Scaniox/Glassphones/V1 - esp32/electronics/glassphones - main pcb/components/esp32 - tinypico/TinyPICO V2 Schematics/README.rst

TinyPICO V2 Schematics
======================

PDF schematics for TinyPICO V2 for both USB-C and Micro-B boards

Unexpected Maker
===================

http://unexpectedmaker.com

http://youtube.com/c/unexpectedmaker

https://www.patreon.com/unexpectedmaker

http://twitter.com/unexpectedmaker

https://www.facebook.com/unexpectedmaker/

https://www.instagram.com/unexpectedmaker/
