Scaniox/Glassphones/V1 - esp32/mechanical/photogrammetry/photo/MeshroomCache/StructureFromMotion/d71c1582ed01c90abd0e8f21b0806b4d62578cae/bundle_adjustment.csv

Time/BA(s) | RefinedPose | ConstPose | IgnoredPose | RefinedPts | ConstPts | IgnoredPts | RefinedK | ConstK | IgnoredK | ResidualBlocks | SuccessIteration | BadIteration | InitRMSE | FinalRMSE | d=-1 | d=0 | d=1 | d=2 | d=3 | d=4 | d=5 | d=6 | d=7 | d=8 | d=9 | d=10+
0.0121821 | 2 | 0 | 0 | 1470 | 0 | 0 | 0 | 1 | 0 | 2940 | 4 | 0 | 0.357994 | 0.327687 | 0 | 0 | 0 | 0 | 0 | 0 | 0 | 0 | 0 | 0 | 0 | 0
0.137033 | 3 | 0 | 0 | 6186 | 0 | 0 | 1 | 0 | 0 | 12372 | 9 | 0 | 0.859424 | 0.383543 | 0 | 0 | 0 | 0 | 0 | 0 | 0 | 0 | 0 | 0 | 0 | 0
1.13852 | 4 | 0 | 0 | 8314 | 0 | 0 | 1 | 0 | 0 | 16628 | 48 | 3 | 1.23038 | 0.613462 | 0 | 0 | 0 | 0 | 0 | 0 | 0 | 0 | 0 | 0 | 0 | 0
1.58042 | 5 | 0 | 0 | 12751 | 0 | 0 | 1 | 0 | 0 | 25502 | 51 | 0 | 0.928391 | 0.694446 | 0 | 0 | 0 | 0 | 0 | 0 | 0 | 0 | 0 | 0 | 0 | 0
1.9575 | 6 | 0 | 0 | 16011 | 0 | 0 | 1 | 0 | 0 | 32022 | 51 | 0 | 1.33581 | 1.04123 | 0 | 0 | 0 | 0 | 0 | 0 | 0 | 0 | 0 | 0 | 0 | 0
2.25359 | 7 | 0 | 0 | 17949 | 0 | 0 | 1 | 0 | 0 | 35898 | 51 | 0 | 1.16084 | 0.9656 | 0 | 0 | 0 | 0 | 0 | 0 | 0 | 0 | 0 | 0 | 0 | 0
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
