Scaniox/Glassphones/V1 - esp32/mechanical/IMG_20210727_0002.jpg

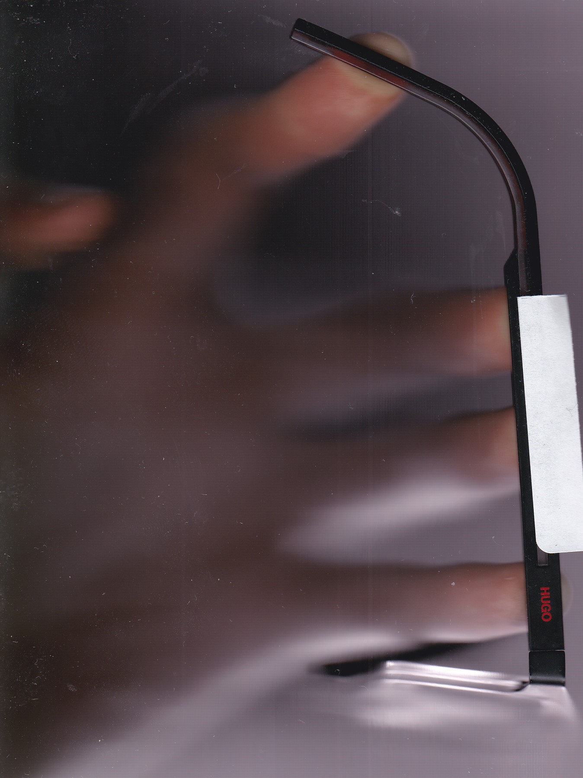
V1 - esp32/mechanical/IMG_20210727_0002.jpg
