Scaniox/Glassphones/V1 - esp32/mechanical/photogrammetry/photo/MeshroomCache/DepthMapFilter/24b79df3ac3274988167803b87b50ed05e469bb3/31802105_nmodMap.png

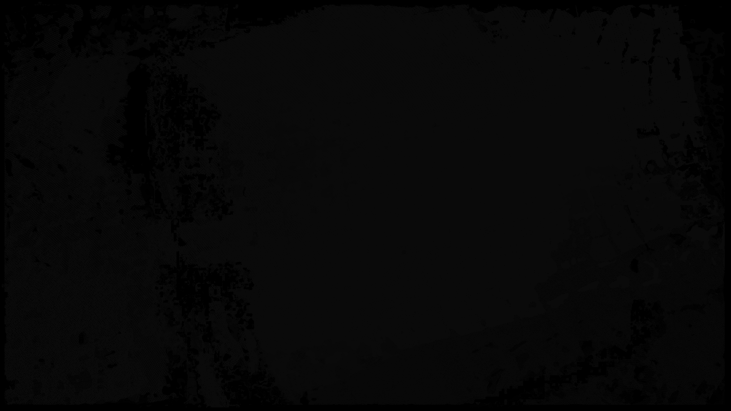
V1 - esp32/mechanical/photogrammetry/photo/MeshroomCache/DepthMapFilter/24b79df3ac3274988167803b87b50ed05e469bb3/31802105_nmodMap.png
