Scaniox/Glassphones/V1 - esp32/mechanical/photogrammetry/photo/MeshroomCache/DepthMapFilter/24b79df3ac3274988167803b87b50ed05e469bb3/286981042_nmodMap.png

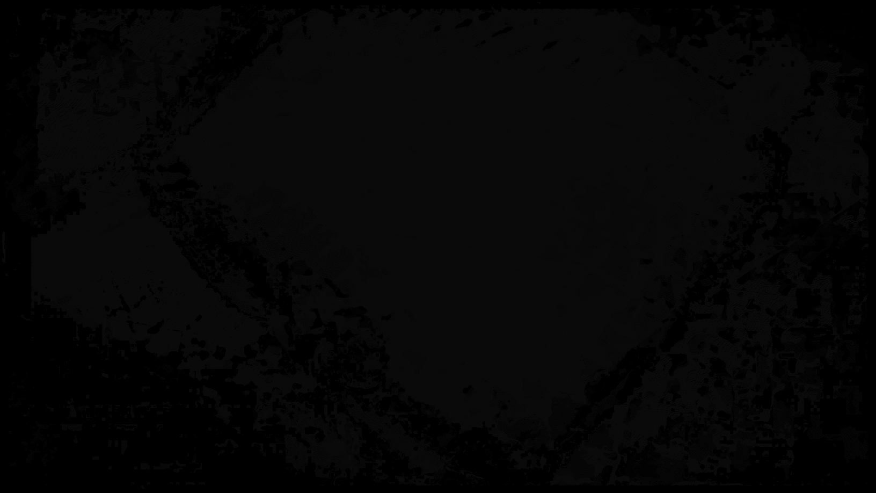
V1 - esp32/mechanical/photogrammetry/photo/MeshroomCache/DepthMapFilter/24b79df3ac3274988167803b87b50ed05e469bb3/286981042_nmodMap.png
