Scaniox/Glassphones/V1 - esp32/mechanical/photogrammetry/video/MeshroomCache/Texturing/2c468ecf00575808510a90f24e992894a4d70658/texture_1001.png

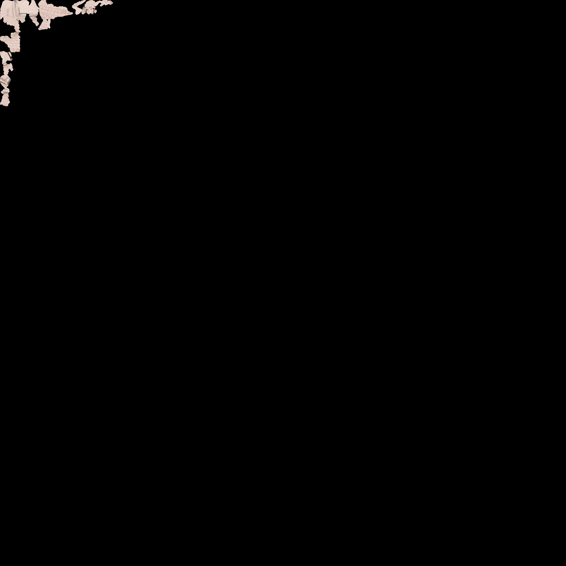
V1 - esp32/mechanical/photogrammetry/video/MeshroomCache/Texturing/2c468ecf00575808510a90f24e992894a4d70658/texture_1001.png
