Scaniox/Glassphones/V1 - esp32/mechanical/photogrammetry/video/r50 imgs/scene00001.png

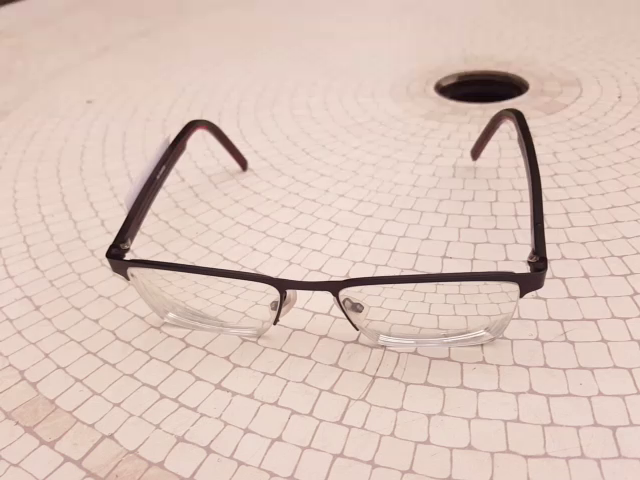
V1 - esp32/mechanical/photogrammetry/video/r50 imgs/scene00001.png
