Scaniox/Glassphones/V1 - esp32/mechanical/photogrammetry/video/r50 imgs/scene00701.png

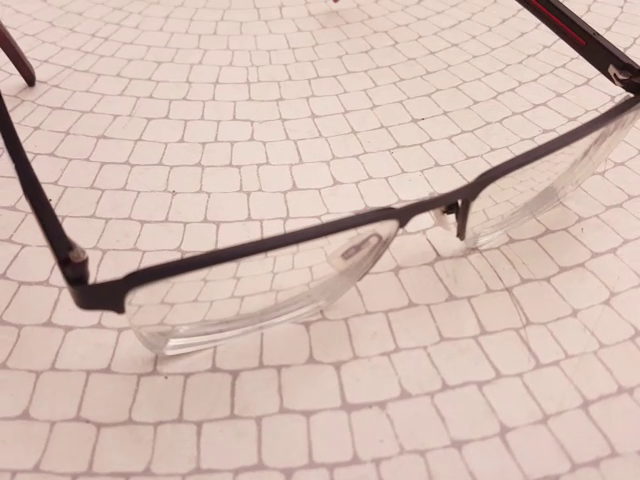
V1 - esp32/mechanical/photogrammetry/video/r50 imgs/scene00701.png
