Scaniox/Glassphones/V1 - esp32/mechanical/photogrammetry/video/r50 imgs/scene00851.png

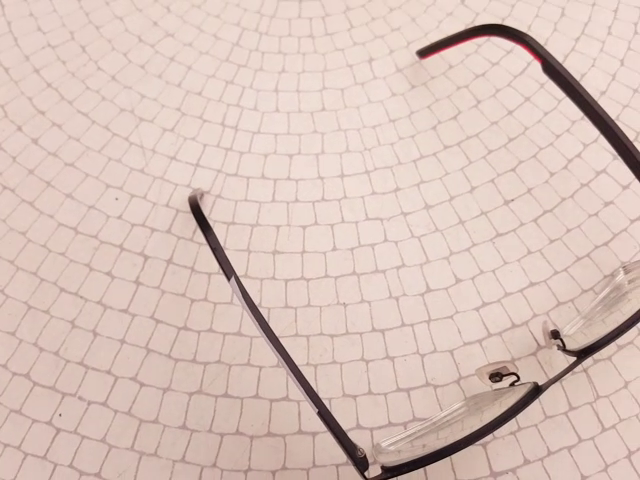
V1 - esp32/mechanical/photogrammetry/video/r50 imgs/scene00851.png
