Scaniox/Glassphones/V1 - esp32/mechanical/photogrammetry/video/r50 imgs/scene00901.png

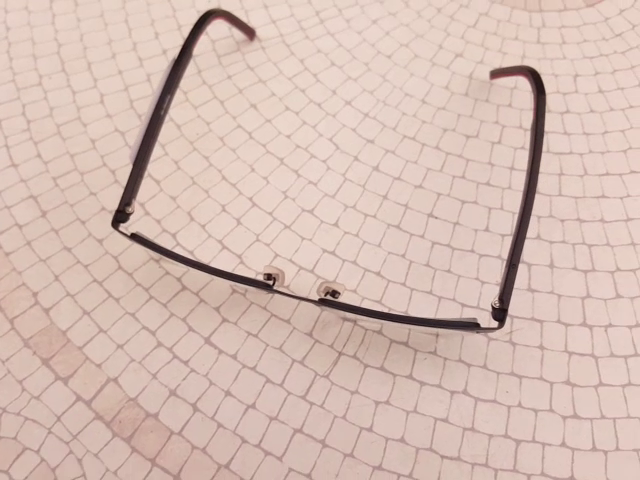
V1 - esp32/mechanical/photogrammetry/video/r50 imgs/scene00901.png
