Scaniox/Glassphones/V1 - esp32/mechanical/photogrammetry/video/r50 imgs/scene01051.png

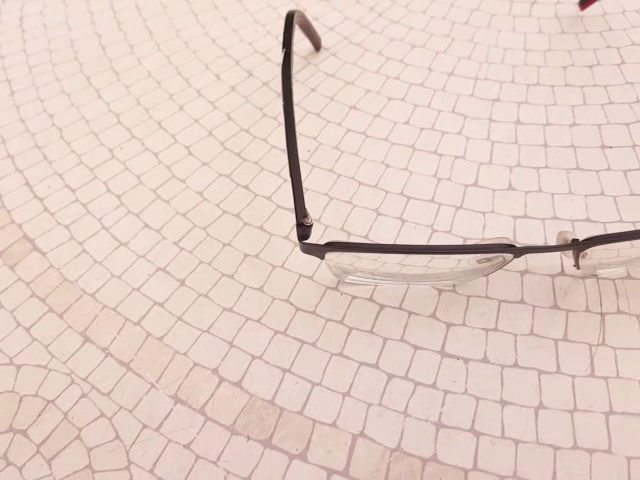
V1 - esp32/mechanical/photogrammetry/video/r50 imgs/scene01051.png
