Scaniox/Glassphones/V1 - esp32/mechanical/photogrammetry/video/r50 imgs/scene01151.png

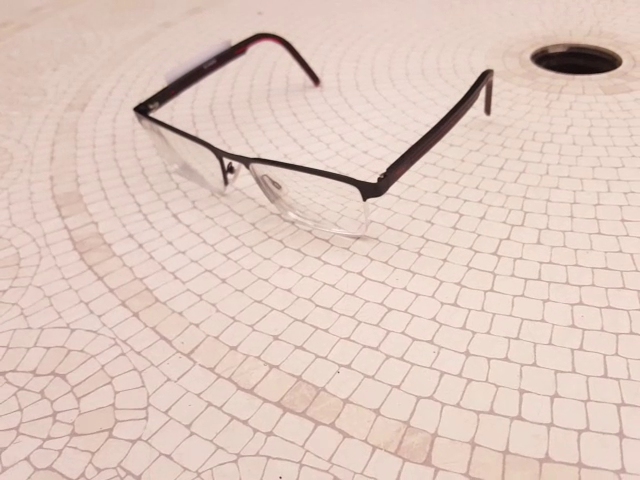
V1 - esp32/mechanical/photogrammetry/video/r50 imgs/scene01151.png
