Scaniox/Glassphones/V1 - esp32/mechanical/photogrammetry/video/r50 imgs/scene01651.png

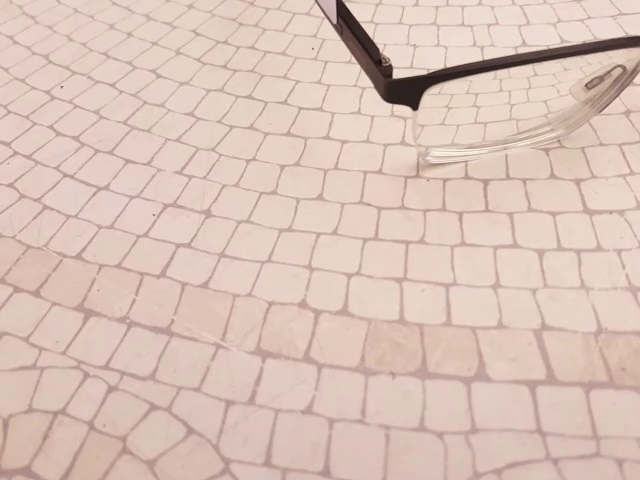
V1 - esp32/mechanical/photogrammetry/video/r50 imgs/scene01651.png
