Scaniox/Glassphones/V2/mechanical/power-led-1.snapshot.1/Power Led.jpg

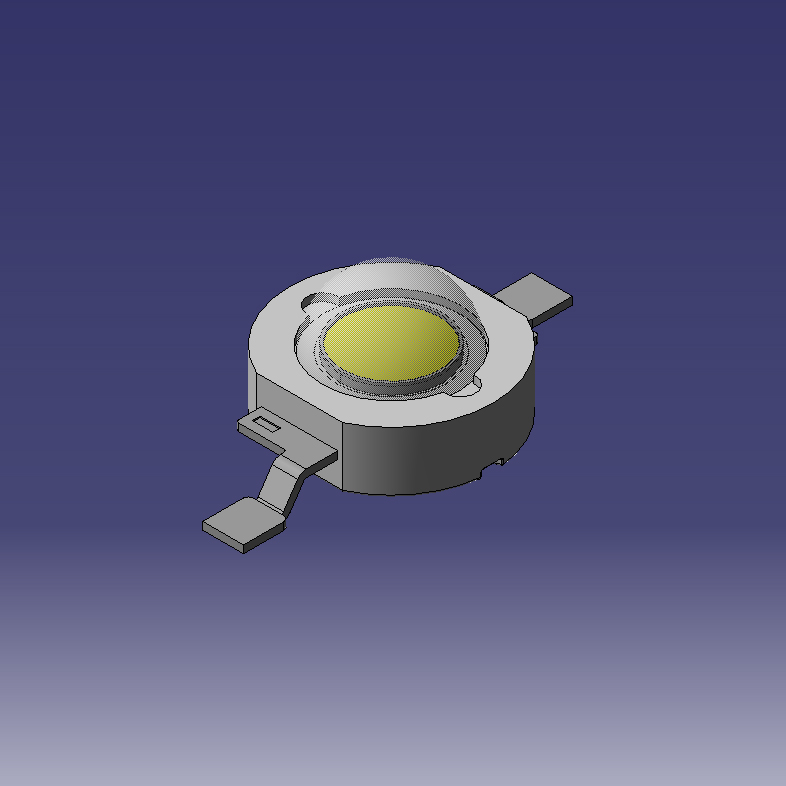
V2/mechanical/power-led-1.snapshot.1/Power Led.jpg
