Scaniox/Glassphones/V2/code/IS2083 Software & Tools (v1.0.3)/Tools/OTA DSP Tuning/IS187x_202_BLEDK3v2.00_UI v2.13/BLEDK_UI_Parameter_Table.xls

FW : | BLEDK3 v2 |  | Date: 2017/06/20
UI Table Version: | 0100
Parameter | Offset | Length | Name | Display | Range | Help | ID
NameFragment | 800 | 32 | Name Fragment | Edit Box | 32 characters | NameFragment is a local device name. If a remote device requires a local name, a local device replies the local device name. | IDC_STATIC_NAME_FRAGMENT
hci_baud_rate_index | 820 | 1 | HCI Baud Rate Index | ComboBox | 0x00 : 921600 0x01 : 460800 0x02 : 230400 0x03 : 115200 0x04 : 57600 0x05 : 38400 0x06 : 28800 0x07 : 19200 0x08 : 14400 0x09 : 9600 0x0A : 4800 0x0B : 2400 | Baud rate index of the HCI UART port. | IDC_STATIC_HCI_BAUD_RATE_INDEX
system_option_3 | 824 | bit0 | H/W Flow Control | ComboBox | Disable Enable | UART H/W flow control (CTS). This parameter need to be set as disable if MCU not support flow control. If Operation Pattern select Manual Pattern, the flow control will be set as disable automatically. | IDC_STATIC_CTS_RTS_FLOW_CONTROL
rxNotifyLength | 828 | 1 | Rx Notify Length | Edit Box | 0x00 ~ 0xFF | The time interval that BLEDK3 checks the received data buffer. When set as “00”, the default value in BLEDK3 for each baud rate is as below: 921600 ~ 19200:0x01 14400 ~ 9600:0x02 4800:0x04 Others:0x07 (Unit: 0.625ms) This parameter can be modified when the default setting can’t meet the requirement. The new set up value must greater than the default value. | IDC_STATIC_CHECK_RX_DATA_INTERVAL
system_option_1 | 822 | bit1 | UART RX_IND | ComboBox | Enable Disable | Enable / Disable UART RX IND | IDC_STATIC_UART_RX_IND
system_option_2 | 823 | bit2 | Operation Pattern | ComboBox | Auto Pattern Manual Pattern | This parameter is used to set the operation pattern between Auto Pattern and Manual Pattern. | IDC_STATIC_OPERATION_PATTERN
Configure_TO | 829 | 1 | Configure Mode Timeout | Edit Box | 0x00: Disable Configure Mode, 0x01~0xFF | This parameter is used to set BLEDK3 configure mode timeout period in Auto Pattern Tool option. | IDC_STATIC_CONFIGURE_MODE_TIMEOUT
PowerOn_Standby_Time | 825 | 1 | Power On Standby Time | Edit Box | 0x01 ~ 0xFF | The standby time duration after power on. Device will enter Shut Down mode when time is up. 0x00~0xFE: Standby time parameter range. 0xFF: Disable Enter shut down mode. | IDC_STATIC_POWER_ON_STANDBY_TIME
Remote_Disconnent_Standby_Time | 826 | 1 | Disconnection Standby Time | Edit Box | 0x01 ~ 0xFF | The standby time duration after link disconnected. Device will enter shut down mode when time is up. 0x00~0xFE: Standby time parameters. 0xFF: Disable enter shut down mode. | IDC_STATIC_REMOTE_DISCONNECT_STANDBY_TIME
Wakeup_External_MCU_Wait_Time | 827 | 1 | Wakeup Externel MCU Wait Time | Edit Box | 0x00 ~ 0xFF | The time interval between UART_TX_IND enabled and UART_TXD start transmit data. | IDC_STATIC_WAKEUP_EXTERNAL_MCU_WAIT_TIME
system_option_3 | 824 | bit2 | Wakeup Pin Option | ComboBox | Enable waken up from shutdown mode by wakeup pin Disable waken up from shutdown mode by wakeup pin | This parameter is used to decide BLEDK3 can be woken up from shutdown mode by wakeup pin or not. If option is enabled, GPIO P2_3 will be configured as wakeup Pin. | IDC_STATIC_WAKEUP_PIN_OPTION
system_option_1 | 822 | bit3~4 | BLE Security | ComboBox | Disable Pairing Request Permission Enable | This parameter is used to set BLE Security. Refer to BLUETOOTH SPECIFICATION 4.0 or latest version for the detail. | IDC_STATIC_BLE_SECURITY
IO_Capability | 87D | 1 | IO Capability | ComboBox | 0x00: DisplayOnly 0x01: DisplayYesNo 0x02: KeyboardOnly 0x03: NoInputNoOutput 0x04: KeyboardDisplay | This parameter is used to configure IO Capability. Refer to BLUETOOTH SPECIFICATION 4.0 or latest version for the detail. | IDC_STATIC_IO_CAPABILITY
system_option_2 | 823 | bit0 | BLE User Confirm Option | ComboBox | Disable LE user confirm refer to passkey Enable LE user confirm refer to passkey | This parameter is used to enable/disable LE(Low Energy) user confirmation referring to passkey. The passkey must set 6 digits if enabled. | IDC_STATIC_BLE_USER_CONFIRM_OPTION
Fix_Passkey | 8 | 6 | Passkey | Edit Box | 6 Numbers | The Passkey which is six byte ASCII code and be used in passkey confirm. | IDC_STATIC_PASSKEY
system_option_2 | 823 | bit6 | Trust Device Connection | ComboBox | Disable Enable | This parameter is used to enable/disable trust (paired) device connection. | IDC_STATIC_TRUST_DEVICE_CONNECTION
system_option_1 | 822 | bit2 | LE Secure Connections Only Mode | ComboBox | Disable Enable | This parameter is used to enable/disable bluetooth 4.2 LE secure connections only mode. | IDC_STATIC_LE_SECURE_CONNECTIONS
system_option_1 | 822 | bit5 | Link Manager Version | ComboBox | Link Manager version is BT4.0 Link Manager version is BT4.2 | This parameter is used to choose Link Manager Version between BT4.0 and BT4.2 . | IDC_STATIC_LINK_MANAGER_VERSION
system_option_1 | 822 | bit6 | Data Length Extension | ComboBox | Disable Enable | This parameter is used to enable/disable Data Length Extension. | IDC_STATIC_DATA_LENGTH_EXTENSION
system_option_1 | 822 | bit0 | Link Quality Detection | ComboBox | Disable Enable | Enable/Disable link quality detection. The RF_Tx_Power_Control_feature will be disabled if Enable this parameter. | IDC_STATIC_LINK_QUALITY_DETECTION
rssi_normal_threshold | 82A | 1 | RSSI Normal Threshold | Edit Box | 50 ~ 90 | RSSI: RF Signal Strength Indication. This parameter is used to set RSSI normal threshold value If detected RSSI value greater or lower than normal threshold level, the configured RSSI_IND GPIO pin will output high or low level respectively. | IDC_STATIC_RSSI_NORMAL_THRESHOLD
rssi_weak_threshold | 82B | 1 | RSSI Weak Threshold | Edit Box | 50 ~ 90 | If detected RSSI value greater or lower than weak threshold level, the configured RSSI_IND GPIO pin will output high or low level respectively. | IDC_STATIC_RSSI_WEAK_THRESHOLD
battery_det_interval | 83A | 1 | Battery Detection Interval | Edit Box | (1~255) | This parameter is used to set battery detection interval. | IDC_STATIC_BATTERY_DETECTION
High_Battery_Level | 83C | 1 | High Battery Level | ComboBox | 0x48 0x4C … 0x90 | High battery level. | IDC_STATIC_HIGH_BATTERY_LEVEL
Normal_Battery_Level | 83D | 1 | Normal Battery Level | ComboBox | 0x48 0x4C … 0x90 | This parameter is defined a normal voltage value of a battery. When the voltage is lower than this value,the device will start low battery warring. | IDC_STATIC_NORMAL_BATTERY_LEVEL
Low_Battery_Level | 83E | 1 | Low Battery Level | ComboBox | 0x48 0x4C … 0x90 | This parameter is defined a low voltage value of a battery. When the voltage is lower than this value, the configured “LOW_BATTERY_IND” GPIO will output low and the device will enter shutdown mode after the “Low Battery Into Shutdown Time”. | IDC_STATIC_LOW_BATTERY_LEVEL
Dangerous_Battery_Level | 83F | 1 | Dangerous Battery Level | ComboBox | 0x48 0x4C … 0x90 | When the voltage is lower than Dangerous Battery Level, the device will enter shutdown mode. | IDC_STATIC_DANGEROUS_BATTERY_LEVEL
Low_Battery_Into_Shutdown_Time | 839 | 1 | Low Battery Into Shutdown Time | Edit Box | 0x00:Disable，0x01~0xFF(Unit:640ms) | This parameter is used to set the waiting time befor enter into shutdown mode if low battery happens. (0x00: Disable enter into shutdown mode when low battery happens) | IDC_STATIC_LOW_BATTERY_INTO_POWER_DOWN_TIME
RF_Class | 821 | 1 | RF Class | ComboBox | 0x01: class 1 0x02: class 2 | The RF_Class is the RF class type. If class 1 is selected, GPIO P1_0 and P2_4 will be set as TX and RX control respectively (High Enable). | IDC_STATIC_RF_CLASS
GPIO_Configured_P36 | 868 | 1 | P36 | Button | 0x01: UART_RTS_CONFIGURE 0x02: BATTERY_LOW_CONFIGURE 0x03: LINK_QUALITY_CONFIGURE 0x05: LINK_DROP_CONFIGURE 0x06: UART_RX_IND_CONFIGURE 0x07: PAIRING_CONFIGURE 0x08: RF_ACTIVE_IND_CONFIGURE 0x09: STATUS1_IND 0x0A: STATUS2_IND 0x0B: AUTO_MODE_DATA_TX_CTRL | Configure function to the GPIO pins. For detail description please refer to the BLEDK3 release note in “IS187x_BM7X BLEDK3 Application Note” document. | IDC_STATIC_P36
GPIO_Configured_P10 | 869 | 1 | P10 | Button | 0x02: BATTERY_LOW_CONFIGURE 0x03: LINK_QUALITY_CONFIGURE 0x05: LINK_DROP_CONFIGURE 0x06: UART_RX_IND_CONFIGURE 0x07: PAIRING_CONFIGURE 0x08: RF_ACTIVE_IND_CONFIGURE 0x09: STATUS1_IND 0x0A: STATUS2_IND 0x0B: AUTO_MODE_DATA_TX_CTRL |  | IDC_STATIC_P10
GPIO_Configured_P00 | 86A | 1 | P00 | Button | 0x02: BATTERY_LOW_CONFIGURE 0x03: LINK_QUALITY_CONFIGURE 0x04: UART_CTS_CONFIGURE 0x05: LINK_DROP_CONFIGURE 0x06: UART_RX_IND_CONFIGURE 0x07: PAIRING_CONFIGURE 0x08: RF_ACTIVE_IND_CONFIGURE 0x09: STATUS1_IND 0x0A: STATUS2_IND 0x0B: AUTO_MODE_DATA_TX_CTRL |  | IDC_STATIC_P00
GPIO_Configured_P31 | 86B | 1 | P31 | Button | 0x02: BATTERY_LOW_CONFIGURE 0x03: LINK_QUALITY_CONFIGURE 0x05: LINK_DROP_CONFIGURE 0x06: UART_RX_IND_CONFIGURE 0x07: PAIRING_CONFIGURE 0x08: RF_ACTIVE_IND_CONFIGURE 0x09: STATUS1_IND 0x0A: STATUS2_IND 0x0B: AUTO_MODE_DATA_TX_CTRL |  | IDC_STATIC_P31
GPIO_Configured_P32 | 86C | 1 | P32 | Button | 0x02: BATTERY_LOW_CONFIGURE 0x03: LINK_QUALITY_CONFIGURE 0x05: LINK_DROP_CONFIGURE 0x06: UART_RX_IND_CONFIGURE 0x07: PAIRING_CONFIGURE 0x08: RF_ACTIVE_IND_CONFIGURE 0x09: STATUS1_IND 0x0A: STATUS2_IND 0x0B: AUTO_MODE_DATA_TX_CTRL |  | IDC_STATIC_P32
GPIO_Configured_P33 | 86D | 1 | P33 | Button | 0x02: BATTERY_LOW_CONFIGURE 0x03: LINK_QUALITY_CONFIGURE 0x05: LINK_DROP_CONFIGURE 0x06: UART_RX_IND_CONFIGURE 0x07: PAIRING_CONFIGURE 0x08: RF_ACTIVE_IND_CONFIGURE 0x09: STATUS1_IND 0x0A: STATUS2_IND 0x0B: AUTO_MODE_DATA_TX_CTRL |  | IDC_STATIC_P33
GPIO_Configured_P34 | 86E | 1 | P34 | Button | 0x02: BATTERY_LOW_CONFIGURE 0x03: LINK_QUALITY_CONFIGURE 0x05: LINK_DROP_CONFIGURE 0x06: UART_RX_IND_CONFIGURE 0x07: PAIRING_CONFIGURE 0x08: RF_ACTIVE_IND_CONFIGURE 0x09: STATUS1_IND 0x0A: STATUS2_IND 0x0B: AUTO_MODE_DATA_TX_CTRL |  | IDC_STATIC_P34
GPIO_Configured_P07 | 86F | 1 | P07 | Button | 0x02: BATTERY_LOW_CONFIGURE 0x03: LINK_QUALITY_CONFIGURE 0x05: LINK_DROP_CONFIGURE 0x06: UART_RX_IND_CONFIGURE 0x07: PAIRING_CONFIGURE 0x08: RF_ACTIVE_IND_CONFIGURE 0x09: STATUS1_IND 0x0A: STATUS2_IND 0x0B: AUTO_MODE_DATA_TX_CTRL |  | IDC_STATIC_P07
GPIO_Configured_P11 | 870 | 1 | P11 | Button | 0x02: BATTERY_LOW_CONFIGURE 0x03: LINK_QUALITY_CONFIGURE 0x05: LINK_DROP_CONFIGURE 0x06: UART_RX_IND_CONFIGURE 0x07: PAIRING_CONFIGURE 0x08: RF_ACTIVE_IND_CONFIGURE 0x09: STATUS1_IND 0x0A: STATUS2_IND 0x0B: AUTO_MODE_DATA_TX_CTRL |  | IDC_STATIC_P11
GPIO_Configured_P22 | 871 | 1 | P22 | Button | 0x02: BATTERY_LOW_CONFIGURE 0x03: LINK_QUALITY_CONFIGURE 0x05: LINK_DROP_CONFIGURE 0x06: UART_RX_IND_CONFIGURE 0x07: PAIRING_CONFIGURE 0x08: RF_ACTIVE_IND_CONFIGURE 0x09: STATUS1_IND 0x0A: STATUS2_IND 0x0B: AUTO_MODE_DATA_TX_CTRL |  | IDC_STATIC_P22
GPIO_Configured_P24 | 872 | 1 | P24 | Button | 0x02: BATTERY_LOW_CONFIGURE 0x03: LINK_QUALITY_CONFIGURE 0x05: LINK_DROP_CONFIGURE 0x06: UART_RX_IND_CONFIGURE 0x07: PAIRING_CONFIGURE 0x08: RF_ACTIVE_IND_CONFIGURE 0x09: STATUS1_IND 0x0A: STATUS2_IND 0x0B: AUTO_MODE_DATA_TX_CTRL |  | IDC_STATIC_P24
GPIO_Configured_P35 | 873 | 1 | P35 | Button | 0x02: BATTERY_LOW_CONFIGURE 0x03: LINK_QUALITY_CONFIGURE 0x05: LINK_DROP_CONFIGURE 0x06: UART_RX_IND_CONFIGURE 0x07: PAIRING_CONFIGURE 0x08: RF_ACTIVE_IND_CONFIGURE 0x09: STATUS1_IND 0x0A: STATUS2_IND 0x0B: AUTO_MODE_DATA_TX_CTRL |  | IDC_STATIC_P35
GPIO_Configured_P12 | 864 | 1 | P12 | Button | 0x02: BATTERY_LOW_CONFIGURE 0x03: LINK_QUALITY_CONFIGURE 0x05: LINK_DROP_CONFIGURE 0x06: UART_RX_IND_CONFIGURE 0x07: PAIRING_CONFIGURE 0x08: RF_ACTIVE_IND_CONFIGURE 0x09: STATUS1_IND 0x0A: STATUS2_IND 0x0B: AUTO_MODE_DATA_TX_CTRL |  | IDC_STATIC_P12
GPIO_Configured_P13 | 865 | 1 | P13 | Button | 0x02: BATTERY_LOW_CONFIGURE 0x03: LINK_QUALITY_CONFIGURE 0x05: LINK_DROP_CONFIGURE 0x06: UART_RX_IND_CONFIGURE 0x07: PAIRING_CONFIGURE 0x08: RF_ACTIVE_IND_CONFIGURE 0x09: STATUS1_IND 0x0A: STATUS2_IND 0x0B: AUTO_MODE_DATA_TX_CTRL |  | IDC_STATIC_P13
GPIO_Configured_P16 | 866 | 1 | P16 | Button | 0x02: BATTERY_LOW_CONFIGURE 0x03: LINK_QUALITY_CONFIGURE 0x05: LINK_DROP_CONFIGURE 0x06: UART_RX_IND_CONFIGURE 0x07: PAIRING_CONFIGURE 0x08: RF_ACTIVE_IND_CONFIGURE 0x09: STATUS1_IND 0x0A: STATUS2_IND 0x0B: AUTO_MODE_DATA_TX_CTRL |  | IDC_STATIC_P16
GPIO_Configured_P17 | 867 | 1 | P17 | Button | 0x02: BATTERY_LOW_CONFIGURE 0x03: LINK_QUALITY_CONFIGURE 0x05: LINK_DROP_CONFIGURE 0x06: UART_RX_IND_CONFIGURE 0x07: PAIRING_CONFIGURE 0x08: RF_ACTIVE_IND_CONFIGURE 0x09: STATUS1_IND 0x0A: STATUS2_IND 0x0B: AUTO_MODE_DATA_TX_CTRL |  | IDC_STATIC_P17
 |  |  | LE Connection Parameter Update Request | ComboBox | Disable Enable | The LE Connection Setting will be assigned by remote side if select disable. If Enable, device will sent the LE connection parameter update request. | IDC_STATIC_LE_CONNECTION_PARAMETER_UPDATE
LE_Connection_Interval_Min | 82C | 2 | Min LE Connection Interval | Edit Box | 0x0006 ~ 0x0C80, Unit: 1.25ms | This parameter is used to set LE min connection interval | IDC_STATIC_MIN_LE_CONNECTION_INTERVAL
LE_Connection_Interval_Max | 82E | 2 | Max LE Connection Interval | Edit Box | 0x0006 ~ 0x0C80, Unit: 1.25ms | This parameter is used to set LE max connection interval | IDC_STATIC_MAX_LE_CONNECTION_INTERVAL
LE_Slave_Latency | 830 | 2 | LE Slave Latency | Edit Box | 0x0000 ~ 0x01F3 | This parameter is used to set LE slave latency. Slave Latency allows a slave to use a reduced number of connection events. The LE Slave Latency parameter defines the number of consecutive connection events that the slave device is not required to listen for the master. More latency, more power saving but reduced connection event. For example, If slave latency=3, Connection event interval is 100msec, Slave device will wake up every 400msec. (100*(1+3)=400). That is slave only has one Connection event while master already have three connection events. | IDC_STATIC_LE_SLAVE_LATENCY
LE_Supervision_Timeout | 832 | 2 | LE Supervision Timeout | Edit Box | 0x000A ~ 0x0C80 | This parameter is used to set LE supervision timeout | IDC_STATIC_LE_SUPERVISION_TIMEOUT
LE_Fast_Adv_Interval | 834 | 2 | LE Fast Advertising Interval | Edit Box | 0x0020 ~ 0x4000 | This parameter is used to set “LE fast advertising interval”, which will make LE device work in fast advertising interval after power on. The fast advertising time period is limited and can be set in“LE Fast Advertising Timeout”. | IDC_STATIC_LE_FAST_ADVERTISING_INTERVAL
LE_Reduced_Power_Adv_Interval | 836 | 2 | LE Reduced Power Advertising Interval | ComboBox | 645ms 768ms 961ms 1065ms 1294ms | This parameter is used to set LE reduced power advertising interval. The interval is longer than “Fast Advertising Interval” so that the power consumption can be reduced. | IDC_STATIC_LE_REDUCED_POWER_ADVERTISING
LE_Fast_Adv_Timeout | 838 | 1 | LE Fast Advertising Timeout | Edit Box | 0x00 ~ 0xFF 設為0x00就不會離開Fast Advertising Mode | This parameter is uesd to set LE fast advertising timeout value | IDC_STATIC_LE_FAST_ADVERTISING_TIMEOUT
 |  |  | Power On LE Reduced Power Advertising Timeout | Edit Box |  | This parameter is uesd to show Power On LE Reduced Power Advertising timeout value. Power On LE Reduced Power Advertising timeout = Power on Standby Time - LE Fast Advertising Timeout. | IDC_STATIC_POWER_ON_LE_REDUCED_POWER_ADVERTISING_TIMEOUT
 |  |  | Disconnection LE Reduced Power Advertising Timeout | Edit Box |  | This parameter is uesd to show Disconnection LE Reduced Power Advertising Timeout value. Disconnection LE Reduced Power Advertising Timeout = Disconnection Standby Time - LE Fast Advertising Timeout | IDC_STATIC_DISCONNECTION_LE_REDUCED_POWER_ADVERTISING_TIMEOUT
ADV_Prefered_Power_Level | 87E | 1 | Advertising Prefered Power Level | ComboBox | 0x00: 0 dBm 0x01: -6 dBm 0x02: -12 dBm 0x03: -18 dBm 0x04: -24 dBm 0x05: -30 dBm | Preferred Tx power level when advertising. There are six power level can be selected.(0,-5,-10,-15,-20,-25 dBm) | IDC_STATIC_ADVERTISING_TX_POWER_LEVEL
CONN_Prefered_Power_Level | 87F | 1 | Connected Prefered Power Level | ComboBox | 0x00: 0 dBm 0x01: -6 dBm 0x02: -12 dBm 0x03: -18 dBm 0x04: -24 dBm 0x05: -30 dBm | Preferred TX power level when connected. (0,-5,-10,-15,-20,-25 dBm) | IDC_STATIC_CONNECTED_TX_POWER_LEVEL
Advertising_Data | 881 | 31 | Advertising Data Setting |  |  | This parameter is uesd to set advertising data. | IDC_STATIC_ADVERTISING_DATA_SETTING
Scan_Rsp_Data | 8A1 | 31 | Scan Response Data Setting |  |  | This parameter is uesd to set scan response data | IDC_STATIC_SCAN_RESPONSE_DATA_SETTING
LED_Type | 840 | 8 | Type | ComboBox | 0x00 : LED1 OFF, LED2 OFF 0x01 : LED1 ON, LED2 ON 0x02 : LED1 ON, LED2 OFF 0x03 : LED1 OFF, LED2 ON 0x04 : LED1 OFF, LED2 FLASH 0x05 : LED1 FLASH, LED2 OFF 0x06 : LED1 ON, LED2 FLASH 0x07 : LED1 FLASH, LED2 ON 0x08 : LED1, LED2 FLASH (simultaneous) 0x09 : LED1, LED2 FLASH (alternate) | The LED0(P0_2)display type setting for Standby, Link, Power On and Low Battery mode. There are 3 types are selectable: Always OFF, Always ON and Flash. The Flash method is set as below: | IDC_STATIC_LED_TYPE
LED_Flash_On_Time | 848 | 8 | On Duration | Edit Box | (1-255) Unit: 50ms | The LED on time during flash. | IDC_STATIC_LED_ON_TIME
LED_Flash_Off_Time | 850 | 8 | Off Duration | Edit Box | (1-255) Unit: 50ms | The LED off time during flash. | IDC_STATIC_LED_OFF_TIME
LED_Flash_Count | 858 | 8 | Count | Edit Box | (0-3) or (0-255) | This is the number of the flashing times for a cycle. | IDC_STATIC_LED_COUNT
LED_Flash_Interval | 860 | 4 | Interval | Edit Box | (0-255) Unit: 50ms | This is the time interval of a cycle. | IDC_STATIC_LED_INTERVAL
low_battery_LED_warning_time | 83B | 1 | Interval | Edit Box | 0x00:Disable，0x01~0xFF(Unit:1sec) | This parameter is uesd to set LED warning time interval if low battery happens | IDC_STATIC_LOW_BATTERY_LED_INTERVAL
system_option_2 | 823 | bit4 | Beacon Feature | ComboBox | Disable Enable | Enable/Disable Beacon function | IDC_STATIC_BEACON_FEATURE
system_option_2 | 823 | bit5 | Beacon Admin Mode | ComboBox | Disable Enable | Enable/Disable Beacon administration mode. | IDC_STATIC_BEACON_ADMIN_MODE
Beacon_Admin_TO | 874 | 1 | Beacon Admin Timeout | Edit Box | (0-255) Unit: 640ms | This parameter is used to configure Beacon administration timeout value 0x00: Disable Beacon Administration Feature Range: 0x01~0xFF, Unit: 640mS | IDC_STATIC_BEACON_ADMIN_TIMEOUT
system_option_2 | 823 | bit7 | Beacon In Connection | ComboBox | Stop Beacon Advertising Beacon Advertising | This option is enabled when BeaconThings function enabled on UI Feature page. If BeaconThings function is enabled: Stop Beacon Advertising: Stop beacon advertising when LE connection is established. Beacon Advertising: Continue beacon advertising when LE connection is established. | IDC_STATIC_BEACON_IN_CONNECTION
Beacon_ADV_Interval | 875 | 2 | Beacon Advertising Interval | Edit Box | (2 Bytes) | This parameter is used to configure the advertising interval for Beacon. | IDC_STATIC_BEACON_ADVERTISING_INTERVAL
Beacon_Adv_Data_Len | 8C0 | 1 | Beacon Advertising Data Length | Edit Box | (1 Bytes) | This paraeter is used to configure advertising data length for Beacon using | IDC_STATIC_BEACON_ADVERTISING_DATA_LENGTH
Beacon_Adv_Data | 8C1 | 31 | Beacon Advertising Data | Edit Box | Max: 31 bytes | This paraeter is used to configure advertising data for Beacon using | IDC_STATIC_BEACON_ADVERTISING_DATA
Beacon_Secret_Key | 877 | 6 | Beacon Secret Key | Edit Box | (6 Bytes) | This parameter is used to configure Secret key for Beacon Admin usage | IDC_STATIC_BEACON_SECRET_KEY
Specific_Pattern |  | 4 | Specific Pattern | Edit Box | (4 Bytes) | This parameter is used to configure specific pattern for auto connection feature. | IDC_STATIC_MANUFACTURE_DATA
Auto_Connection_TO | 8EB | 1 | Inquiry Timeout Value | Edit Box | 0x00:Disable，0x01~0xFF(Unit: 640 ms) |  | IDC_STATIC_INQUIRY_TIMEOUT_VALUE
system_option_2 | 823 | bit3 | Privacy | ComboBox | Disable Enable | If enabled the option, BLEDK3 will broadcast random address. | IDC_STATIC_PRIVACY
Private_Address_Diversification_Time | 8EC | 1 | Random Address Interval | Edit Box | 0x01~0xFF(Unit: 10.24 s) | This parameter is used to configure random address interval. Valid only when "Privacy" is enabled. | IDC_STATIC_PRIVATE_ADDRESS_DIVERSIFICATION_TIME
Manual_Handle_Value_Confirmation | 822 | bit5 | Manual Handle Value Confirmation | ComboBox | Disable Enable | This parameter is used to enable/disable Manual Handle Value Conrifmation.If this parameter is enable, ATT stack will be configured as manual transmission of confirmation when an indication is received. | IDC_STATIC_ATT_SETTING1
UART_Parity | 8ED | bit0 | UART Parity | ComboBox | Disable Enable | Enable/Disable UART parity. | IDC_STATIC_UART_PARITY
 |  | bit1~2 | Parity Mode | ComboBox | 0x00: Odd Parity 0x01: Space Parity 0x02: Even Parity 0x03: Mark Parity |  | IDC_STATIC_UART_PARITY_MODE
 |  | bit3 | Stop Bit | ComboBox | 1 stop bit 2 stop bit |  | IDC_STATIC_STOP_BIT
