Scaniox/Glassphones/V2/code/IS2083 Software & Tools (v1.0.3)/Tools/Config Tool/IS208x_Config_Parameter_Table_R0.xls

eeprom table file | BT5506_Multi-SPK_V1_eeprom_table_R8 |  |  |  |  | Release Date: 2018/10/17
default eeprom table file | UITool_IS206XGM_002_nSPK05_Default_Table.txt |  |  |  |  | Author: Kiki Ko(A23171)
Parameter File | IS206XGM_002_nSPK_UI_Parameter_Table_R0.xls |  |  |  |  | Contents Updated Conversation | Marked with Red
Tester |  |  |  |  |  | Report Date:
Parameter |  | Length Default:Byte | Default Value(Hex) | Name | Display | Range | Relation | Description | Help | ID
SYS_CFG_KEY_CLASS | 0x0101 | 3 | 0x140424 | Class of Device | Dropdown menu | Address 0x07: 0x04: Headset 0x14: Speaker |  |  | The Class is the class of device/service field (CoD). It is indicated using the 'Format Type field' within the CoD. The value could be 0x040424(HS) or 0x001F00(Uncategorized) | IDC_STATIC_MISC_OPTION11
SYS_CFG_KEY_HCI_BAUD_RATE_INDEX | 0x0102 | 1 | 0x03 | UART Baudrate | Dropdown menu | 0x00: 921600 0x01: 460800 0x02: 230400 0x03: 115200 0x04: 57600 0x05: 38400 0x06: 28800 0x07: 19200 0x08: 14400 0x09: 9600 0x0A: 4800 0x0B: 2400 |  | Valid only when 'HCI Uart' is enabled. | The UART Baudrate is the baud rate index of the HCI UART. (Unit: BPS) | IDC_STATIC_UART_SETTING2
SYS_CFG_KEY_AUTO_POWER_OFF_TIME | 0x0103 | 1 | 0x0F | Auto Power Off Time | Text box | 1~254 |  | Valid only when 'Auto Power Off Enable' is enabled | Set the Auto Power Off timer.The minimum is 1 | IDC_STATIC_POWER_SAVE1
SYS_CFG_KEY_MUTE_ALARM_TIME | 0x0104 | 1 | 0x05 | Mute Alarm Time | Text box | 3~254 |  |  | If the speaker has calls and its microphone is muted , it will ring the mute tone to alert user periodically with this interval(unit in 640 ms). | IDC_STATIC_WARRING_TIME3
SYS_CFG_KEY_MCU_WAKEUP_TIME | 0x0105 | 1 | 0x1E | Wake Up Delay Time | Text box | 0~254 |  | Valid only when 'CPU Idle Mode' is enabled. | Waiting time to start BT UART TX after wakeup MCU | IDC_STATIC_UART_SETTING4
SYS_CFG_KEY_USER_MMI_DATA | 0x0106 | 80 | {0} | User MMI Data Enable/n User MMI Data | Text box |  |  | The option can be configured only when SPK in embedded mode. | Enable/Disable embedded spp predefine user data | IDC_STATIC_USER_MMI_DATA0
SYS_CFG_KEY_OPTION1 | 0x010B | bit0:1bit | 0x42 | None | None |  |  | This bit will be enabled when 'HCI Uart' is enabled | Report status and event to MCU if this option is enabled. This option must be enabled if the speaker has external MCU.
 |  | bit1: 1bit |  | UART Command (in Mainfeature Window) Enable HCI UART | Check box Dropdown menu | 0: Not select Uart function 1: Select Uartr function 0: Disable 1: Enable |  | The enable setting in MAIN FEATURE table | Enable/Disable Application to use HCI UART. | IDC_STATIC_UART_SETTING1
 |  | bit2: 1bit |  | Disable Wait for ACK | Dropdown menu | 0: Disable 1: Enable |  |  | If this option is enabled, it will not wait the ACK of UART event from MCU after reporting transparent data (UART event ID 0x22) to MCU. It is usually used in throughput sensitive case and MCU has capability to process burst data. | IDC_STATIC_UART_SETTING9
 |  | bit4:1bit |  | UART Protocol Tx Padding | Dropdown menu | 0:Disable 1:Enable |  | Valid only when 'HCI Uart' is enabled | Pad one byte 0x00 in the front of the start byte 0xAA of UART event. | IDC_STATIC_UART_SETTING8
 |  | bit6: 1bit |  | CLIP Name or Number | Dropdown menu | 0: Phone Number Only; 1: Name Priority; |  |  | CLIP= Calling Line Identification Presentation "Number Only" : Send phone number to MCU only. "Name Piority" : Send name data to MCU is priority | IDC_STATIC_UART_SETTING6
 |  | bit7:1bit |  | None | None |  |  | This bit will be enabled when 'HCI Uart' is disabled | Embedded SPP for the case that has no MCU
SYS_CFG_KEY_OPTION2 | 0x010C | bit0:1bit | 0x99 | Simple Pairing | Dropdown menu | Disable Enable |  |  | Enable: Use simple pairing method when pairing. Disable: A PIN Code will be required when pairing. | IDC_STATIC_MISC_OPTION7
 |  | bit1: 1bit |  | Hang Up a Call When Switch Off | Dropdown menu | 0: Disable 1: Enable |  |  | Hang up all calls when the speaker is turned off by slide switch. | IDC_STATIC_MISC_OPTION20
 |  | bit2:1bit |  | Keep BLE In Power Off | Dropdown menu | 0: Disable 1: Enable |  |  | Enable/Disable keep BLE connection when SPK in power off state. | IDC_STATIC_MISC_OPTION27
 |  | bit3:1bit |  | Disconnect All In Pairing | Dropdown menu | 0: Disable 1: Enable |  |  | Enable/Disable disconnect all link when SPK in pairing state. | IDC_STATIC_MISC_OPTION26
 |  | bit6:1bit |  | Only Accept Paired Device | Dropdown menu | 0: Disable 1: Enable |  |  | If this option is enabled, the speaker only accepts the connect request from paired devices when it is not in pairing mode. | IDC_STATIC_MISC_OPTION25
 |  | bit7: 1bit |  | A2DP Link Silence | Check box | 0: Not Select 1: Select |  |  | If Enable this one, then system will be shut down automatically, when A2DP/AVRCP is only one link、'Auto Power Off Timer' has been timeout、no key is pressed、no adapter plug in and BT device doesn't receive any audio packet from AG any more. | IDC_CHECK_AUTO_POWER_OFF_MASK3
SYS_CFG_KEY_OPTION3 | 0x010D | bit0: 1bit | 0x00 | Auto Power Off Enable | Check box | 0: Not Select 1: Select |  |  | When system enter standby state, then set 'Auto Power Off Time' to shut down power. | IDC_CHECK_AUTO_POWER_OFF_MASK1
 |  | bit1: 1bit |  | Pairing Timeout Shut Down Directly Enable | Check box | 0: Not select 1: Select |  |  | When system pairing timeout, then shut down system directly if enable this option. | IDC_CHECK_AUTO_POWER_OFF_MASK2
 |  | bit3: 1bit |  | Line In Silence Detect | Dropdown menu | 0: Disable 1: Enable |  |  | Detect silence status for Aux-in signal if this option is enabled. The duration to determine the Aux-in is silence is about 33 seconds. | IDC_STATIC_LINE_IN_SETTING6
 |  | bit4:1bit |  | Rx IND (in Mainfeature Window) | Check box | 0: Not select 1: Select |  |  | If this option is enabled, UART RX data will wakeup the speaker from power down without GPIO.
 |  | bit6:1bit |  | Power On by "Power On" Command | Dropdown menu | 0: Disable 1: Enable |  | 1. Enable/Disable requre to send power on command after HW power on 2. Valid only when HCI Uart enabled | BTM enter fake power on(wait MCU send power on command) | IDC_STATIC_UART_SETTING7
SYS_CFG_KEY_MAX_PAIRED_DEVICES | 0x010E | 1 | 0x08 | Enable Save Max.Number of Paired Devices | Text box | 1~8 |  |  | The max number of paired device that the speaker stores in EEPROM. FW basically support 8 device records, and use this parameter for application to set really max paired records. | IDC_STATIC_CONNECTION_SETTING3
SYS_CFG_KEY_NFC_STABLE_TIME | 0x010F | 1 | 0x04 | NFC StableTime | Text box | 0~254 |  |  | The timing setting for system to make sure NFC contect happen | IDC_STATIC_NFC_SETTING2
SYS_CFG_KEY_POWER_SAVE_OPTION | 0x0110 | bit0:1bit | 0x01 | CPU Idle Mode | Dropdown menu | Bit 0~3 : Setting this bit to allow enter 32K mode. 0: Disable 32K mode 1: Enable 16M 32K mode. 2: Enable ULPC 32 mode Bit 4~7 : Setting this bit to allow enter CPU_IDLE mode. 0: Disable the CPU_IDLE function. 1: Enable the CPU_IDLE function. |  | The option can be configured only when 'UART command' is disabled or Rx is enabled. The UART command setting in MAIN FEATURE table. | Disable/Enable BT CPU idle function. | IDC_STATIC_UART_SETTING5
SYS_CFG_KEY_SNIFF_INTERVAL | 0x0112 | 2 | 0x0320 | Max Sniff Interval | Text box | 0~65535 |  |  |  | IDC_STATIC_POWER_SAVE4
 |  | 2 | 0x0320 | Min Sniff Interval | Text box | 0~65535 |  |  |  | IDC_STATIC_POWER_SAVE5
SYS_CFG_KEY_OPYION4 | 0x0113 | bit0:1bit | 0x00 | Auto Unsniff in Data Transmission | Dropdown menu | 0: Disable 1: Enable |  |  | After system enter sniff mode, it would not auto exit sniff mode if received packets or send packets. | IDC_STATIC_MISC_OPTION32
SYS_CFG_KEY_OTA_DFU_KEY | 0x0115 | 0x10 | 0x22222222222222222222222222222222 | OTA DFU Key | Text box |  |  |  | The encryption key for OTA DFU. | IDC_STATIC_OTA_DFU_SETTING1
BT_CFG_KEY_APP_FIX_PIN_CODE | 0x0201 | 4 | 0x30303030 | PIN Code | Text box | 0x30303030~0x39393939 |  | Valid when 'Eanble Simple Pairing' is disabled. | The PIN code which is four-byte ASCII code is a fixed PIN code of a local device. The local device replies the remote devices using the PIN code when remote devices send a PIN code request command. | IDC_STATIC_PIN_CODE
BT_CFG_KEY_NO_SERVICE_WARNING_TIME | 0x0202 | 1 | 0x1E | No Service Warning Time | Text box | 3~254 |  |  | When mobile phone can not receive the signal from base station, headset alert user periodically with this interval(unit in 640 ms). This function is through HFP. | IDC_STATIC_WARRING_TIME1
BT_CFG_KEY_LINK_LOSS_RECONNECT_TIME | 0x0203 | 1 | 0x0C | Link Loss Reconnect Timeout | Text box | 0~255 |  |  | When HF link loss, it will try to link back until page fail times reached this value | IDC_STATIC_CONNECTION_SETTING2
BT_CFG_KEY_PAGE_HS_TIME | 0x0204 | 1 | 0x0C | Link HF Timeout | Text box | 8~254 |  | Link HF Timeout' must greater or equal to 'Enable Save Max. Number of Paired' | The timeout to reconnecting to link loss device. 0x00 : don't reconnect 0xFF : recover without timeout other : (unit in 5 second) | IDC_STATIC_CONNECTION_SETTING7
BT_CFG_KEY_PAIRING_TIMEOUT | 0x0205 | 1 | 0x2F | Pairing Timeout | Text box | 0~254 |  |  | System will close pairing mode when time out(unit in 30 second), 0 means no timeout. | IDC_STATIC_CONNECTION_SETTING1
BT_CFG_KEY_PAGE_A2DP_TIME | 0x0207 | 1 | 0x0C | Link A2DP Timeout | Text box | 8~254 |  | Link A2DP Timeout' must greater or equal to 'Enable Save Max. Number of Paired' | A2DP device page fail retry duration | IDC_STATIC_CONNECTION_SETTING4
BT_CFG_KEY_RSSI_WEAK_THRESHOLD | 0x0208 | 1 | 0xBA | RSSI Weak Threshold | Text box | 0~90 |  |  | "RSSI Weak Threshold" will be compared with the average of real RSSI data , the average of real RSSI was calculated by (2^Average_RSSI_Counter) times RSSI data | IDC_STATIC_TONE_SETTING24
BT_CFG_KEY_SPECIFIC_SPP_UUID_0 | 0x0209 | 0x10 | 0x91,0x81,0x9D,0x50,0x5D,0x72,0x44,0x78,0xA0,0x01,0x29,0xEB,0x2C,0x76,0x35,0x68 | Custom SPP UUID 1 | Text box |  |  |  | custom SPP UUID | IDC_STATIC_SPP_UUID_SETTING3
BT_CFG_KEY_SPECIFIC_SPP_UUID_1 | 0x020A | 0x10 | 0x00 0x00 0x00 0x00 0x00 0x00 0x00 0x00 0x00 0x00 0x00 0x00 0x00 0x00 0x00 0x00 | Custom SPP UUID 2 | Text box |  |  |  | custom SPP UUID | IDC_STATIC_SPP_UUID_SETTING4
BT_CFG_KEY_DEVICE_NAME | 0x020B | 0x0B | "MCHP BM83" | Name Fragment | Text box |  |  |  | Name Fragment is your bluetooth product name that will be shown on a remote device,ex:a phone | IDC_STATIC_NAME1
BT_CFG_KEY_PAIRED_DEVICES[0][0] | 0x020C | 6 | {0} | Address | Text box |  |  |  | The BT address of a specified Audio Gateway. When you enter the data to a headset, it connects with a specified Audio Gateway directly after power on. | IDC_STATIC_AUDIO_GATEWAY_ADDRESS
BT_CFG_KEY_PAIRED_DEVICES[0][7] |  | 1 |  | Bundle | Dropdown menu | 0: Disable 1: Enable |  |  | The flag for the Audio Gateway that defined the chip inside from IS208x. This column must be enable if you want to connect with IS208x. | IDC_STATIC_AUDIO_GATEWAY_BUNDLE
BT_CFG_KEY_LINK_QUALITY_DETECT_OPTION | 0x020E | bit4: 1bit | 0x43 | Link Quality Detection | Dropdown menu | 0: Disable 1: Enable |  |  | Enable link quality detection. | IDC_STATIC_LINK_QUALITY_SETTING1
BT_CFG_KEY_SPP_OPTION | 0x020F | bit0~bit2:3bit | 0x04 | SPP Option | Dropdown menu | 0x01: Single customer SPP 0x02: Double customer SPP 0x04: Use standard UUID |  |  | Select to use standard UUID or customer SPP UUID. | IDC_STATIC_SPP_UUID_SETTING2
BT_CFG_KEY_LINK_OPTION | 0x0210 | bit[3~0] | 0x00 | Power On Link Back Profile(s) Setting | Dropdown menu | 0: Last Device; 1: Hands-free Profile; 2: A2DP Profile; |  | Last Device: the system will link back all proifle(s) that last disconnected device supported and recorded in the Device Hands-free Profile: only link back hands-free profile that last disconnected device supported and recorded in the Device A2DP Profile : only link back A2DP profile that last disconnected device supported and recorded in the Device Notice: for some mobile phone,even if you set the parameter on your bluetooth device side, but phone will perhaps establish the others profile(s) that supported by your bluetooth device and recorded in these phone | Select link back profils when power on. | IDC_STATIC_CONNECTION_SETTING6
BT_CFG_KEY_HF_SUPPORT_FEATURE_LLBYTE | 0x0211 | bit7: 1bit | 0x9E | Wide Band Speech Enable (mSBC) | Dropdown menu | 0: Disable 1: Enable |  |  |  | IDC_STATIC_MISC_OPTION29
BT_CFG_KEY_OPTION1 | 0x0212 | bit0:1bit | 0x00 | Power On Link Back Setting | Dropdown menu | 0: Disable 1: Enable |  |  | Enable link back feature when power on. | IDC_STATIC_CONNECTION_SETTING8
 |  | bit1: 1bit |  | Enter Pairing when Power On Link Back Failed | Dropdown menu | 0: Disable 1: Enable |  |  | Enable this option to enter pairing automatically if it fails to reconnect to phone when power on. | IDC_STATIC_MISC_OPTION23
 |  | bit2: 1bit |  | Search Paired Devices Pattern Setting | Dropdown menu | 0: Last Device Only; 1: All Devices; |  |  | If select All Devices,then Search all devices in paired device list and link back to one of all devices. If select Last Device Only,then only find the last disconnected device in Paired list and link it back. | IDC_STATIC_CONNECTION_SETTING10
 |  | bit4: 1bit |  | Always Answer Incoming Call | Dropdown menu | 0: Disable 1: Enable |  |  | If this option is enabled and HFP connection exists, it will always answer incoming calls automatically. | IDC_STATIC_MISC_OPTION18
 |  | bit5: 1bit |  | Auto Answer Incoming Call When Link Back | Dropdown menu | 0: Disable 1: Enable |  |  | When the speaker links back HF link and call status is incoming call, then it will answer the call automatically if this option is enabled. | IDC_STATIC_MISC_OPTION24
 |  | bit6: 1bit |  | Enter Pairing Mode When Power On | Dropdown menu | 0: Disable 1: Enable |  |  | If the speaker doesn't try to create CSB link when power on or doesn't need to reconnect to remove device when power on, then it will enter pairing mode when power on. | IDC_STATIC_MISC_OPTION5
 |  | bit7: 1bit |  | Enable Pairing as Standby Mode | Dropdown menu | 0: Disable 1: Enable |  |  | Open Inquiry scan window in when the speaker is in standby mode. That is, if this option is enabled the speaker is discoverable in not only pairing mode but also standby mode. | IDC_STATIC_MISC_OPTION4
BT_CFG_KEY_OPTION2 | 0x0213 | bit1: 1bit | 0x62 | Link Application | Dropdown menu | 0: Single-Link; 1: Multi-Link; |  |  | Single-link: Only one HF link exists. Multi-link: Two HF links exist. | IDC_STATIC_MISC_OPTION8
 |  | bit3: 1bit |  | NFC Handsover | Dropdown menu | 0: Disable 1: Enable |  |  | Force the speaker to disconnect original profile connection when second profile connection is connected if this option is enabled. | IDC_STATIC_NFC_SETTING3
 |  | bit4: 1bit |  | NFC (in Mainfeature Window) NFC Detection Enable | Dropdown menu | 0: Not Select 1: Select 0: Disable 1: Enable |  | The enable setting in MAIN FEATURE table | Enable/disable NFC function. It needs some hardware circuit to support NFC function. | IDC_STATIC_NFC_SETTING1
 |  | bit5: 1bit |  | Report Battery Status to Smart Phone | Dropdown menu | 0: Disable 1: Enable |  |  | Report speaker/hs battery status via AT command base on HFP to mobile phone. | IDC_STATIC_MISC_OPTION14
 |  | bit6:1bit |  | AVRCP Version Option | Dropdown menu | 0: AVRCP v1.3 1: AVRCP v1.6 |  |  | Select to use AVRCP v1.6 or AVRCP v1.3. | IDC_STATIC_MISC_OPTION31
BT_CFG_KEY_PROFILES_OPTION | 0x0214 | bit0: 1bit | 0x3F | Support HS Profile | Dropdown menu | 0: Disable 1: Enable | Interlocking address: 1.If A2DP is unselected, the AVRCP controller/Target will be forced set unselected. | The enable setting in MAIN FEATURE table. | This profile let your device can establish a voice channel with your mobile phone. | IDC_STATIC_PROFILE_SETTING1
 |  | bit1: 1bit |  | Support HF Profile | Dropdown menu Check box | 0: Disable 1: Enable |  |  | This profile let your device support more features than HS. E.g.calling line identification, three way calling, echo canceling and noise reducion, phone status information,includeing signal strength, and so on. | IDC_STATIC_PROFILE_SETTING2
 |  | bit2: 1bit |  | Support A2DP Profile | Dropdown menu Check box | 0: Disable 1: Enable |  |  | Supporting this profile means you can enjoy music by your device connected with an AG that also supports A2DP. | IDC_STATIC_PROFILE_SETTING3
 |  | bit3: 1bit |  | Support AVRCP Controller | Dropdown menu Check box | 0: Disable 1: Enable |  |  | If support AVRCP controller,it means your BT device could be controller that can remote another device by sending commands. | IDC_STATIC_PROFILE_SETTING4
 |  | bit4: 1bit |  | Support AVRCP Target | Dropdown menu Check box | 0: Disable 1: Enable |  |  | If support AVRCP target,it means your BT device can receive a command from a remote device. | IDC_STATIC_PROFILE_SETTING5
 |  | bit5: 1bit |  | Support SPP Profile | Dropdown menu Check box | 0: Disable 1: Enable |  |  | Response SPP profile in SDP query. The speaker supports SPP profile if this option is enabled. | IDC_STATIC_PROFILE_SETTING10
 |  | bit6:1bit |  | Support iAP Profile | Dropdown menu Check box | 0: Disable 1: Enable |  |  | Response iAP in SDP query, The speaker support Apple iAP protocol if this bit is enabled | IDC_STATIC_PROFILE_SETTING11
BT_CFG_KEY_MAX_RF_TX_POWER_LEVEL | 0x0217 | bit[3~0] | 0x66 | Inquiry TX Power Level | Dropdown menu | 0~6 |  | TX power is calibrated in MP process, where Power Level 6 (PL0 in MPSE setting) is configured around 10dBm as default. | The inquiry TX power level is selectable from 0 to 6. For level 6, the default TX power is around 10dBm. While decrease the level number, the TX power will degrade around 5 dB for one step. | IDC_STATIC_RF_TX_POWER_SETTING1
 |  | bit[7~4] |  | BT Connected TX Power Level | Dropdown menu | 0~6 |  | TX power is calibrated in MP process, where Power Level 6 (PL0 in MPSE setting) is configured around 10dBm as default. | The BT connected TX power level is selectable from 0 to 6. For level 6, the default TX power is around 10dBm. While decrease the level number, the TX power will degrade around 5 dB for one step. | IDC_STATIC_RF_TX_POWER_SETTING2
AUD_MCU_CFG_KEY_A2DP_LATENCY | 0x0301 | 1 | 0xF0 | A2DP Latency | Text box | 0~255 |  |  | To set a2dp latency timer. (Unit: ms) | IDC_STATIC_MULTI_SPK_SETTING3
AUD_MCU_CFG_KEY_SUPPORT_CODEC_TYPE | 0x0302 | bit0:1bit | 0x03 | SBC | Check box | 0: Not Select 1: Select |  |  |  | IDC_CHK_SBC_CODEC_MASK
 |  | bit1: 1bit |  | AAC | Check box | 0: Not Select 1: Select |  |  |  | IDC_CHK_AAC_CODEC_MASK
 |  | bit2: 1bit |  | LDAC | Check box | 0: Not Select 1: Select |  |  |  | IDC_CHK_NEWDAC_CODEC_MASK
AUD_MCU_CFG_KEY_TX_EQ_MODE | 0x0304 | 1 | 0x00 | Initial Equalizer Mode | Dropdown menu | 0: Disable 1: Enable |  |  | For audio(A2DP), similar to voice setting. | IDC_STATIC_EQUIZER_SETTING2
AUD_MCU_CFG_KEY_LINE_IN_GAIN | 0x0308 | 1 | 0x0A | Initial Line In SPK Gain | Dropdown menu | 0~15 |  |  | Default gain level for line in mode. "Initial Line In SPK Gain" should be between max and min level. | IDC_STATIC_LINE_IN_SETTING10
AUD_MCU_CFG_KEY_MAX_MIN_LINE_IN_GAIN | 0x0309 | bit[3~0]:4bit | 0xF0 | Line In Min Level | Dropdown menu | 0~15 |  |  | Minimum line in gain level. | IDC_STATIC_LINE_IN_SETTING12
 |  | bit[7~4]:4bit |  | Line In Max Level | Dropdown menu | 0~15 |  |  | Maximum line in gain level. | IDC_STATIC_LINE_IN_SETTING11
AUD_MCU_CFG_KEY_AUDIO_GAIN_TABLE | 0x030A | 16 | 0x00, 0xA2, 0xA5, 0xC2, 0xC5, 0xE2, 0xE5, 0xE8, 0xEB, 0xEE, 0xF1, 0xF4, 0xF7, 0xFA, 0xFB, 0xFC | Audio Speaker Gain Table | Dropdown menu |  |  |  | Audio speaker gain. | IDC_STATIC_AUDIO_SPK_GAIN_SETTING4
AUD_MCU_CFG_KEY_VOICE_GAIN_TABLE | 0x030E | 16 | 0x00, 0xA2, 0xA5, 0xC2, 0xC5, 0xE2, 0xE5, 0xE8, 0xEB, 0xEE, 0xF1, 0xF4, 0xF7, 0xFA, 0xFB, 0xFC | Voice Speaker Gain Setting | Dropdown menu |  |  |  | Voice speaker gain. | IDC_STATIC_VOICE_SPK_GAIN_SETTING
AUD_MCU_CFG_KEY_EQ_MASK | 0x030C | 2 | 0x0401 | Equalizer Mode Mask | Check box | bit1: OFF bit2: Soft bit3: Bass bit4: Treble bit5: Classical bit6: Jazz bit7: Pop bit8: Dance bit9: R&B bit10: Custom EQ |  |  | To mask which equalizer modes be used. | IDC_STATIC_EQUIZER_SETTING3
AUD_MCU_CFG_KEY_AUDIO_RPU_STATUS | 0x030F | bit5:1bit | 0x00 | Equalizer Function Enable | Dropdown menu | 0: Disable 1: Enable |  |  | Open EQ module if Enable. | IDC_STATIC_EQUIZER_SETTING1
 |  | bit7:1bit |  | Sound Effect | Dropdown menu | 0: Disable 1: Enable |  |  | Enable/Disable sound effect. | IDC_STATIC_SOUND_EFFECT_SETTING1
AUD_MCU_CFG_KEY_AEC_MODE | 0x0310 | 1 | 0x00 | AEC On/Off | Dropdown menu | 0: Disable 1: Enable |  |  | Modified on enabling/disabling AEC. | IDC_STATIC_DSP_OPTION1
AUD_MCU_CFG_KEY_MODULE_ACTIVE_FLAG | 0x0318 | bit4:1bit | 0x00
AUD_MCU_CFG_KEY_VOICE_RPU_STATUS | 0x0317 | bit0:1bit | 0x00
AUD_MCU_CFG_KEY_MSBC_RPU_STATUS | 0x0311 | bit0:1bit | 0x00
AUD_MCU_CFG_KEY_NR_EQ_MODE | 0x030D | 1 | 0x11 | NR EQ Mode | Dropdown menu | 0: Disable 1: Enable |  |  | Modified on enabling/disabling NR EQ mode. | IDC_STATIC_DSP_OPTION2
AUD_MCU_CFG_KEY_MODULE_ACTIVE_FLAG | 0x0318 | bit0:1bit | 0x00
AUD_MCU_CFG_KEY_VOICE_RPU_STATUS | 0x0317 | bit[2~1]:2bit | 0x00
AUD_MCU_CFG_KEY_CVSD_RX_EQ_MODE | 0x0312 | 1 | 0x00 | MIC - EQ | Dropdown menu | 0x00: Disable 0x0A: Enable |  |  | The index of mic EQ mode. | IDC_STATIC_VOICE_EQUIZER_SETTING2
AUD_MCU_CFG_KEY_CVSD_TX_EQ_MODE | 0x0313 | 1 | 0x00 | Speaker - EQ | Dropdown menu | 0x00: Disable 0x0A: Enable |  |  | The index of speaker EQ mode. | IDC_STATIC_VOICE_EQUIZER_SETTING1
AUD_MCU_CFG_KEY_MSBC_RX_EQ_MODE | 0x0314 | 1 | 0x00 | mSBC MIC EQ | Dropdown menu | 0x00: Disable 0x0A: Enable |  |  | The index of custom mic EQ mode. | IDC_STATIC_VOICE_EQUIZER_SETTING4
AUD_MCU_CFG_KEY_MSBC_TX_EQ_MODE | 0x0315 | 1 | 0x00 | mSBC Speaker EQ | Dropdown menu | 0x00: Disable 0x0A: Enable |  |  | The index of custom EQ speaker mode. | IDC_STATIC_VOICE_EQUIZER_SETTING3
AUD_MCU_CFG_KEY_AMPLIFIER_CTRL_TIME | 0x0316 | bit[2~0]:3bit | 0x00 | Off Amplifier T2 | Text box | 0~7 |  |  | when AMP_CTRL_T1 expired, then wait at least this time to start play audio. Notice: AMP_ENABLE means external amplifier enable pin | IDC_STATIC_AMP_CONTROL_SETTING4
 |  | bit[5~3]:3bit |  | Off Amplifier T1 | Text box | 0~7 |  |  | when config codec ACTIVE, wait this time to turn on external amplifier, if this value is 0, then wait 100ms. | IDC_STATIC_AMP_CONTROL_SETTING3
 |  | bit[7~6]:2bit |  | Off Amplifier T0 | Text box | 0~3 |  |  | when codec mute, set this timer to turn off external amplifier, if this value set to 0, then turn off external amplifier directly | IDC_STATIC_AMP_CONTROL_SETTING2
AUD_MCU_CFG_KEY_OPTION1 | 0x0319 | bit0:1bit | 0x0E | Line-in Path | Dropdown menu | 0: Digital Path; 1: Analog Path; |  |  | Select the path of Line-in data through: Digital Path or Analog Path | IDC_STATIC_LINE_IN_SETTING4
 |  | bit2: 1bit |  | CHG/AUX-IN Ind (in Mainfeature Window) Stereo Line in Loop Back | Check box Dropdown menu | 0: Not Select 1: Select 0: Disable 1: Enable |  | The enable setting in MAIN FEATURE table. | Enable/disable Aux-in detection. | IDC_STATIC_LINE_IN_SETTING1
 |  | bit3: 1bit |  | Line In Priority | Dropdown menu | 0: SBC>LineIn 1:Linein>SBC |  | Line In > SBC: means when system detects LINE_IN plugs in, it will switch to line in mode. SBC> Line In: means system will still be in A2DP mode even if Line In is plugged in. | This parameter is used to set the priority of Aux-in is higher than A2DP. When Aux-in and A2DP streaming coexist, the speaker will output the audio with higher priority. | IDC_STATIC_LINE_IN_SETTING2
 |  | bit4: 1bit |  | Line In Mute/Unmute | Dropdown menu | 0: Disable 1: Enable |  |  | Enable mute/unmute feature by Play/Pause event when Line In priority | IDC_STATIC_LINE_IN_SETTING3
 |  | bit7: 1bit |  | DSP CODEC Always On Enable | Dropdown menu | 0: Disable 1: Enable |  |  | Never power down codec and DSP if this function be enabled | IDC_STATIC_CODEC_FUNC9
AUD_MCU_CFG_KEY_OPTION2 | 0x031A | bit0:1bit | 0x01 | Concert Mode Resync | Dropdown menu | 0: Disable 1: Enable |  |  | Enable audio resync function in Concert Mode. | IDC_STATIC_MULTI_SPK_SETTING5
 |  | bit3: 1bit |  | Cut Off Amplifier When Mute | Dropdown menu | 0: Disable 1: Enable |  |  | Off amplifier when CODEC is mute. | IDC_STATIC_AMP_CONTROL_SETTING1
 |  | bit6: 1bit |  | Suspend Stream When SCO Established | Dropdown menu | 0: Disable 1: Enable |  |  | This setting use for multi link status. If system build multi link with A and B mobile phone and have a A2DP stream with A, when phone B have a incoming call, system send "Suspend" command to phone A before establish SCO link with phone B. | IDC_STATIC_MISC_OPTION9
AUD_MCU_CFG_KEY_OPTION3 | 0x031B | bit0: 1bit | 0x2E | Audio SRC | Dropdown menu | 0: Disable 1: Enable |  |  | 44.1K to 48K for A2DP audio | IDC_STATIC_CODEC_FUNC13
 |  | bit1: 1bit |  | Voice SRC | Dropdown menu | 0: Disable 1: Enable |  |  | 8K/16K to 48K for ring tone or SCO voice | IDC_STATIC_CODEC_FUNC14
 |  | bit2:1bit |  | Voice Stereo | Dropdown menu | 0: Disable 1: Enable |  | The option can be configured only when "Voice SRC" is enabled | Enable the function that voice outputs both of L and R channel. | IDC_STATIC_CODEC_FUNC15
 |  | bit3:1bit |  | Tone Stereo | Dropdown menu | 0: Disable 1: Enable |  | The option can be configured only when "Voice SRC" is enabled | Enable the function that single tone and VP output both of L and R channel. | IDC_STATIC_CODEC_FUNC16
 |  | bit[6~5]: 2bit |  | CODEC Output Type | Dropdown menu | 1:External codec with I2S1 output 2:Internal codec |  |  | Select to use external codec or internal codec. | IDC_STATIC_CODEC_FUNC12
AUD_MCU_CFG_KEY_AUDIO_OUTPUT_CHANNEL_STYLE | 0x031C | bit0~bit2:3bit | 0x01 | Enable LR Sound Mix | Dropdown menu | 0x00:Disable 0x03:Enable |  | CODEC_STEREO_DAC_path.b2 =1 | Mix left and right channel speaker output to mono speaker output. | IDC_STATIC_CODEC_FUNC5
AUD_MCU_CFG_KEY_CODEC_ADC_PATH | 0x031E | 1 | 0x45 | ADC Path | Dropdown menu | 0x43: MIC2 to L 0x44: MIC2 to L, MIC1 to R 0x45: MIC1 to L 0x46: MIC1 to L, MIC2 to R |  |  | To set the ADP path for analog and digital Mics. | IDC_STATIC_GAIN_LEVEL_SETTING3
AUD_MCU_CFG_KEY_EFFECT_MASK | 0x0320 | 1 | 0x01 | Audio Effect Mask Selection | Check box | Bit 0 :All Off Bit 1:MB-DRC On Bit 2:AW Bit 3:All On |  |  | To mask which sound effect be used. | IDC_STATIC_SOUND_EFFECT_SETTING4
AUD_MCU_CFG_KEY_EFFECT | 0x0321 | bit0~bit1:2bit | 0x00 | Default Audio Effect | Check box | Bit 0 :All Off Bit 1:MB-DRC On Bit 2:AW Bit 3:All On |  |  | Default sound effect mode. | IDC_STATIC_SOUND_EFFECT_SETTING3
AUD_MCU_CFG_KEY_LINE_IN_LATENCY | 0x0322 | 1 | 0xF0 | Line In Latency | Text box | 0~240 |  |  | Line-in latency adjustment (unit: *1/3 ms) ex: 0xF0 => 240 * 1/3 = 80 ms | IDC_STATIC_LINE_IN_SETTING9
AUD_MCU_CFG_KEY_CLOSE_CODEC_TIME | 0x0323 | 1 | 0x08 | Close CODEC Time | Text box | 1~254 |  |  | When DSP in SBC decode state, and FW do not receive any stream data,it will close CODEC after this time | IDC_STATIC_CODEC_FUNC10
AUD_MCU_CFG_KEY_CODEC_PARAMETERS[0] | 0x0324 | bit[2~0]:3bit | 0x01 | Speaker Output | Dropdown menu | bit2~0: 001: Capless Speaker Output 010: Single End Speaker Output 110: Single End External Amp. |  |  | Capless: Speaker output without a DC blocking capacitor. Single end: Speaker output with a DC blocking capacitor | IDC_STATIC_CODEC_FUNC1
AUD_MCU_CFG_KEY_CODEC_PARAMETERS[1] |  | bit2~bit1:2bit | 0x00 | Filter Type For Stereo Audio Quality | Dropdown menu | 0: Filter Type 1; 1: Filter Type 2; 2: Filter Type 3; 3: Filter Type 4; |  |  | Stereo audio quality by selecting different filter type. Filter Type 1: Clear. Filter Type 2: Warm for Vocal. Filter Type 3: Filter 2 extended to 17KHz. Filter Type 4: Filter 2 extended to 15KHz. | IDC_STATIC_CODEC_FUNC3
 |  | bit1:1bit |  | Enable LR Sound Channel Swap | Dropdown menu | 0: L/R Normal 1: L/R Swap |  |  | Swap left and right channel speaker output(only for A2DP) | IDC_STATIC_CODEC_FUNC4
 |  | bit2:1bit
AUD_MCU_CFG_KEY_MICROPHONE_GAIN_LEVEL | 0x0326 | 1 | 0x04 | Analog Microphone Gain Level | Dropdown menu | 0x00 0x01 0x02 …. 0x0E 0x0F |  |  | To set the analog mic gain. | IDC_STATIC_GAIN_LEVEL_SETTING1
AUD_MCU_CFG_KEY_MICROPHONE_DIGITAL_GAIN_LEVEL | 0x0327 | 1 | 0x0C | Digital Microphone Gain Level | Dropdown menu | 0x00(means mute) 0x01 0x02 …. 0x0E 0x0F |  |  | To set the digital mic gain. | IDC_STATIC_GAIN_LEVEL_SETTING2
AUD_MCU_CFG_KEY_DIGITAL_MIC | 0x0328 | bit0:1bit | 0x00 | Digital Mic | Dropdown menu | 0: Disable 1: Enable |  |  | Enable/disable digital MIC. | IDC_STATIC_GAIN_LEVEL_SETTING4
 |  | bit[3~1]:3bit |  | Digital Mic Mode | Dropdown menu | 0 0 0 : Mono Raising 0 0 1 : Mono Falling 1 0 0 : L Rising - R Falling stereo 1 0 1 : L Falling - R Rising stereo |  |  | Configuring the digital Mic modes. | IDC_STATIC_GAIN_LEVEL_SETTING5
BLE_CFG_KEY_ADV_DATA | None | None | None | Advertising Data Length | Text box | 十六进制数据 | This is only used to show an information, it is not the real value that is wrotten into the setting file. | 1.Total Length = Name Length+1*Name Length+UUID Length+1*UUID Length+Manufacture Length+1*Manufacture Length+Others1 Length+1*Others1 Length+Others2 Length+1*Others2 Length | This parameter is uesd to set advertising data. | IDC_STATIC_ADVERTISING_DATA_SETTING
 | 0x0401 | Name Length | 0x00,0x00 | Device Name | Text box | 十六进制数据 |  | Name Length = Length of Device Name+Device Name Type(0x09)
 |  | UUID Length | 0x00,0x00 | UUID | Text box | 十六进制数据 |  | 1. 0x7xx = 0x772+Name Length+1 2. UUID Length = UUID type(0x06)
 |  | Manufacture Length | 0x00,0x00,0x00,0x00,0x00,0x00,0x00,0x00,0x00,0x00,0x00, 0x00 | Manufacture Data | Text box | 十六进制数据 |  | 1. 0x7yy = 0x7xx+UUID Length+1 2. Manufacture Length = Manufacture type(0xFF)+ Data Length
 |  | Others1 Length | 0x00,0x00,0x00,0x00,0x00,0x00,0x00,0x00,0x00,0x00,0x00, 0x00 | Others | Text box | 十六进制数据 |  | 1. 0x7zz = 0x7yy+Manufacture Length+1 2. Others Length = Other type(User Define)+ Data Length
 |  | Others2 Length | 0x00,0x00,0x00,0x00,0x00,0x00,0x00,0x00,0x00,0x00,0x00, 0x00 | Others | Text box | 十六进制数据 |  | 1. 0x7mm = 0x7zz+Others Length+1 2. Others Length = Other type(User Define)+ Data Length
BLE_CFG_KEY_SCAN_RSP_DATA | None | None | None | Scan Response Data Length | Text box | 十六进制数据 |  | 1.Total Length = Name Length+1*Name Length+UUID Length+1*UUID Length+Manufacture Length+1*Manufacture Length+Others1 Length+1*Others1 Length+Others2 Length+1*Others2 Length | This feature is uesd to set scan response data, the information will be sent to a LE scaner. | IDC_STATIC_SCAN_RESPONSE_DATA_SETTING
 | 0x0402 | Name Length | 0x0A, 0x09, 0x4D, 0x43, 0x48, 0x50, 0x00, 0x42, 0x4D, 0x38, 0x33 | Device Name | Text box | 十六进制数据 |  | Name Length = Length of Device Name+Device Name Type(0x09)
 |  | Tx Power Length | 02,0x0A,0x05 | Tx Power | Text box | 十六进制数据 |  | Tx Power Length = Type(0x0A)+Data Length
 |  | Scan Manufacture Length | 0x00, 0x00, 0x00, 0x00,0x00,0x00,0x00,0x00,0x00, 0x00,0x00,0x00,0x00,0x00,0x00, 0x00,0x00,0x00,0x00,0x00,0x00, 0x00,0x00,0x00,0x00,0x00,0x00,0x00 | Manufacture Data | Text box | 十六进制数据 |  | 1.0x7xx = 0x78E+Tx Power Length+1 2.Scan Manufacture Length = Type(0xFF)+Data Length
 |  | Scan Other1 Length |  | Others | Text box | 十六进制数据 |  | 1.0x7yy = 0x7xx+Scan Manufacture Length+1 2.Scan Other1 Length = Type(User Define)+Data Length
 |  | Scan Other2 Length |  | Others | Text box | 十六进制数据 |  | 1. 0x7zz = 0x7yy+Scan Other1 Length+1 2.Scan Other2 Length = Type(User Define)+Data Length
BLE_CFG_KEY_AUTO_DISCONNECT_TIME | 0x0403 | 1 | 0x00 | LE Reconnection Timeout | Text box | 0~255 |  |  | If no data is transmitted over this time, disconnect LE connection. (Unit: min, 0 means this function is disabled) | IDC_STATIC_LE_RECONNECTION_TIMEOUT
 |  |  | None | LE Update Request | Dropdown menu | 0: Disable 1: Enable |  |  | If Disable,then max and min connection inveral parameters will be cleared to 0 and disable max and min windows. If Enable,max and min windows will be enable. If Max or Min connection interval value is 0, then tool will set this item to disable.
BLE_CFG_KEY_CONNECTION_INTERVAL_MIN | 0x0407 | 2 | 0x0000 | Min. LE Connection Interval | Text box | 0:Disable 0x0008~0x0C80:Enable |  |  | This parameter is used to set LE min connection interval. (Unit: 1.25ms) The value 0x0000 means Speaker won't issue parameter update request command. | IDC_STATIC_MIN_LE_CONNECTION_INTERVAL
BLE_CFG_KEY_CONNECTION_INTERVAL_MAX | 0x0408 | 2 | 0x0000 | Max. LE Connection Interval | Text box | 0:Disable 0x000A~0x0C80:Enable |  |  | This parameter is used to set LE max connection interval. (Unit: 1.25ms) The value 0x0000 means Dual Speaker won't issue parameter update request command. | IDC_STATIC_MAX_LE_CONNECTION_INTERVAL
BLE_CFG_KEY_SLAVE_LATENCY | 0x0409 | 2 | 0x0000 | LE Slave Latency | Text box | 0x0000~0x03E8 |  |  | This parameter is used to set LE slave latency. | IDC_STATIC_LE_SLAVE_LATENCY
BLE_CFG_KEY_SUPERVISION_TIMEOUT | 0x040A | 2 | 0x0000 | LE Supervision Timeout | Text box | 0x000A~0x0C80 |  | The connection parameter request may be rejected if it does not comply with all of these rules: 1. Interval Max * (LE Slave Latency + 1) ≤2 seconds 2. Interval Min ≥20 ms 3. Interval Min + 20 ms ≤Interval Max 4. LE Slave Latency ≤4 5. LE Supervision Timeout ≤6 seconds 6.Interval Max * (LE Slave Latency + 1) * 3 < LE Supervision Timeout | This parameter is used to set LE supervision timeout. (Unit: 10ms) | IDC_STATIC_LE_SUPERVISION_TIMEOUT
BLE_CFG_KEY_BLE_OPTION | 0x040C | bit2:1bit | 0x0D | BLE Application in Embedded Mode | Dropdown menu | 0: Disable 1: Enable |  |  |  | IDC_STATIC_BLE_APPLICATION_SETTING1
 |  | bit3:1bit |  | Audio Beacon | Dropdown menu | 0: Disable 1: Enable |  |  | Enable/disable audio beacon. Put some information in Service data in advertising data such as battery level, BTM status. This option is used in Embedded mode. | IDC_STATIC_ADDITIONAL_DATA_IN_ADVERTISING
 |  | bit4:1bit |  | Audio Beacon | Dropdown menu | 0: Disable 1: Enable |  |  | Enable/disable audio beacon. Put some information in Service data to scan response data such as battery level, BTM status. This option is used in Embedded mode. | IDC_STATIC_ADDITIONAL_DATA_IN_SCAN_RESPONSE
 |  | bit5:1bit |  | Initiate Pairing Request in BLE Connected | Dropdown menu | 0: Disable 1: Enable |  |  | Enable/disable authentication for transparent service. | IDC_STATIC_PAIRING_REQEST_IN_BLE_CONNECTED
 |  | bit6:ibit |  | OTA DFU service | Dropdown menu | 0: Enable 1: Disable |  |  | Enable/disable OTA DFU service. | IDC_STATIC_OTA_DFU_SETTING2
BLE_CFG_KEY_TRANSPARENT_SRV_UUID | 0x040D | 16 | 0x49, 0x53, 0x53, 0x43, 0xFE, 0x7D, 0x4A, 0xE5, 0x8F, 0xA9, 0x9F, 0xAF, 0xD2, 0x05, 0xE4, 0x55 | Transparent Service UUID | Text box | 十六进制数据 |  |  | This parameter is used to config the sepcific Transparent Service UUID. | IDC_STATIC_UART_SERVICE_UUID
BLE_CFG_KEY_TRANSPARENT_TX_UUID | 0x040E | 16 | 0x49, 0x53, 0x53, 0x43, 0x1E, 0x4D, 0x4B, 0xD9, 0xBA, 0x61, 0x23, 0xC6, 0x47, 0x24, 0x96, 0x16 | Transparent TX UUID | Text box | 十六进制数据 |  |  | This parameter is used to config the sepcific Transparent TX UUID. | IDC_STATIC_UART_TX_UUID
BLE_CFG_KEY_TRANSPARENT_RX_UUID | 0x040F | 16 | 0x49, 0x53, 0x53, 0x43, 0x88, 0x41, 0x43, 0xF4, 0xA8, 0xD4, 0xEC, 0xBE, 0x34, 0x72, 0x9B, 0xB3 | Transparent RX UUID | Text box | 十六进制数据 |  |  | This parameter is used to config the sepcific Transparent RX UUID. | IDC_STATIC_UART_RX_UUID
BLE_CFG_KEY_MANUFACTURE_NAME_STRING | 0x0410 | 16 | "MCHP: | Manufacture Name | Text box | ASCII |  |  | This parameter is used to configure the name of the manufacturer of the device. | IDC_LE_DIS_SETTING_MANUNAME
BLE_CFG_KEY_MODEL_NAME_STRING | 0x0411 | 16 | "Dual Speaker" | Model Name | Text box | ASCII |  |  | Thisparameter is used to configure the model number that is assigned by the device vendor. | IDC_LE_DIS_SETTING_MODELNAME
BLE_CFG_KEY_SERIAL_NUMBERSTRING | 0x0412 | 16 | 0x00,0x00,0x00,0x00,0x00,0x00,0x00,0x00,0x00,0x00,0x00,0x00,0x00,0x00,0x00,0x00 | Serial Number | Text box | ASCII |  |  | This parameter is used to configure the serial number for a particular instance of the device. | IDC_LE_DIS_SETTING_SERIALNO
BLE_CFG_KEY_SOFTWARE_REVISION_STRING | 0x0413 | 16 | 0x00,0x00,0x00,0x00,0x00,0x00,0x00,0x00,0x00,0x00,0x00,0x00,0x00,0x00,0x00,0x00 | Software Revision | Text box | ASCII |  |  | This parameter is used to configure the software revision for the software within the device. | IDC_LE_DIS_SETTING_SW_REV
BLE_CFG_KEY_SLAVE_ADV_POLICY | 0x0418 | bit[3~0]:4bit | 0x33 | ADV Policy in Stereo Slave | Dropdown menu | 0x00: Disable 0x01: Non-Connectable Advertising 0x02: Scannable Advertising 0x03: Connectable Advertising |  |  | The Advertising policy for the TWS Slave. | IDC_STATIC_MULTI_SPK_SETTING8
 |  | bit[7~4]:4bit |  | ADV Policy in Concert Mode Slave | Dropdown menu | 0x00: Disable 0x01: Non-Connectable Advertising 0x02: Scannable Advertising 0x03: Connectable Advertising |  |  | The Advertising policy for the Concert Mode Slave. | IDC_STATIC_MULTI_SPK_SETTING7
BLE_CFG_KEY_MAX_RF_TX_POWER_LEVEL | 0x0419 | bit[3~0]:4bit | 0x66 | Advertising TX Power Level | Dropdown menu | 0~6 |  |  | The ADV TX power level. Level 0 ~ 6 (max) The max reference power is 5 dBm and decrease 5 dBm for each following level. The actual power is upon calibration in MP process. | IDC_STATIC_ADVERTISING_TX_POWER_LEVEL
 |  | bit[7~4]:4bit |  | Connected TX Power Level | Dropdown menu | 0~6 |  |  | The BLE connected TX power level. Level 0 ~ 6 (max) The max reference power is 5 dBm and decrease 5 dBm for each following level. The actual power is upon calibration in MP process. | IDC_STATIC_CONNECTED_TX_POWER_LEVEL
 |  |  | None | High Temp. Stop Charging | Dropdown menu | Degree: 35 degree C 40 degree C 45 degree C 50 degree C 55 degree C |  |  | To set the stop charging degree for high temperature.
 |  |  | None | Low Temp. Stop Charging | Dropdown menu | Degree: -5 degree C 0 degree C 5 degree C 10 degree C 15 degree C |  |  | To set the stop charging degree for low temperature.
POWER_CFG_KEY_STOP_CHARGING_SAR_MIN | 0x0501 | 2 | 0x00A7 | Stop Charging SAR Min | Text box | Degree: 0x00C3: 35 degree C 0x00A7: 40 degree C 0x0092: 45 degree C 0x0082: 50 degree C 0x0072: 55 degree C Customize: 0000~FFFF |  | Valid only when 'Ambient Temperature Charging Detection' is Degree or Customize. | The minimum SAR voltage for ambient temperature detection to stop charger. | IDC_STATIC_CHARGING_SETTING17
POWER_CFG_KEY_STOP_CHARGING_SAR_MAX | 0x0502 | 2 | 0x0331 | Stop Charging SAR Max | Text box | Degree: 0x0331: -5 degree C 0x02B0: 0 degree C 0x0239: 5 degree C 0x01D6: 10 degree C 0x0186: 15 degree C Customize: 0000~FFFF |  | Valid only when 'Ambient Temperature Charging Detection' is Degree or Customize. | The maximum SAR voltage for ambient temperature detection to stop charger. | IDC_STATIC_CHARGING_SETTING19
POWER_CFG_KEY_RESTART_CHARGING_SAR_MIN | 0x0503 | 2 | 0x00C3 | Restart Charging SAR Min | Text box | Degree: 0x00E4: 35 degree C 0x00C3: 40 degree C 0x00A7: 45 degree C 0x0092: 50 degree C 0x0082: 55 degree C Customize: 0000~FFFF |  | Valid only when 'Ambient Temperature Charging Detection' is Degree or Customize. | The minimum SAR voltage for ambient temperature detection to restart charger. | IDC_STATIC_CHARGING_SETTING18
POWER_CFG_KEY_RESTART_CHARGING_SAR_MAX | 0x0504 | 2 | 0x02B0 | Restart Charging SAR Max | Text box | Degree: 0x02B0: -5 degree C 0x0239: 0 degree C 0x01D6: 5 degree C 0x0186: 10 degree C 0x0144: 15 degree C Customize: 0000~FFFF |  | Valid only when 'Ambient Temperature Charging Detection' is Degree or Customize. | The maximum SAR voltage for ambient temperature detection to restart charger. | IDC_STATIC_CHARGING_SETTING20
POWER_CFG_KEY_BATTERY_CAPACITY | 0x0505 | 2 | 0x015F | Constant Current of Charging Complete | Text box | 8~5000 |  |  |  | IDC_STATIC_CHARGING_SETTING5
POWER_CFG_KEY_WARNING_BATTERY_LEVEL | 0x0506 | 2 | 0x0DAC | Low Battery Warning Level | Dropdown menu | 0x0BB8: 3.0V 0x0C1C: 3.1V 0x0C80: 3.2V 0x0CE4: 3.3V 0x0D48: 3.4V 0x0DAC: 3.5V 0x0E10: 3.6V |  |  | The lowest voltage level that device can work well,when battery voltage is under this value, device will generate some warning, such as tone, LED and buzzer (if buzzer is enabled). Range:(3V-to-4.2V) or( 3000 to 4200) | IDC_STATIC_BATTERY_DETECTION2
POWER_CFG_KEY_SHUTDOWN_BATTERY_LEVEL | 0x0507 | 2 | 0x0BB8 | Battery Shut Down Level | Dropdown menu | 0x0BB8: 3.0V 0x0C1C: 3.1V 0x0C80: 3.2V 0x0CE4: 3.3V 0x0D48: 3.4V 0x0DAC: 3.5V 0x0E10: 3.6V |  |  | When the battery voltage level is lower this value, the speaker will shutdown automatically. The value definitionl is the same with Warning_Battery_Level. Range:(3V-to-4.2V) or( 3000 to 4200) | IDC_STATIC_BATTERY_DETECTION3
POWER_CFG_KEY_CC_SUB_MODE_PROTECT_TIME | 0x0508 | 1 | 0x14 | Constant Current Protect Time for First Charging Stage | Text box | 0~254 |  |  | When cc mode over protective time expired, charging will be completed and stop charging. CC Mode protective timer stage 0 (unit in min) | IDC_STATIC_CHARGING_SETTING9
 |  | 1 | 0x14 | Constant Current Protect Time for Second Charging Stage |  | 0~254 |  |  | When cc mode over protective time expired, charging will be completed and stop charging. CC Mode protective timer stage 1 (unit in min) | IDC_STATIC_CHARGING_SETTING21
 |  | 1 | 0xB4 | Constant Current Protect Time for Third Charging Stage |  | 0~254 |  |  | When cc mode over protective time expired, charging will be completed and stop charging. CC Mode protective timer stage 2 (unit in min) | IDC_STATIC_CHARGING_SETTING23
 |  | 1 | 0xB4 | Constant Current Protect Time for Fourth Charging Stage |  | 0~254 |  |  | When cc mode over protective time expired, charging will be completed and stop charging. CC Mode protective timer stage 3 (unit in min) | IDC_STATIC_CHARGING_SETTING26
POWER_CFG_KEY_CV_PROTECT_TIME | 0x0509 | 1 | 0x78 | Constant Voltage Protect Time | Text box | 0~254 |  |  | Protect time in constant voltage charging mode. Charger will stop charging function when over this time. | IDC_STATIC_CHARGING_SETTING10
POWER_CFG_KEY_OPTION1 | 0x050A | bit0: 1bit | 0xE2 | Extra Charging Complete Led | Dropdown menu | 0:Disable 1:Enable |  | This option can be configured only when 'Charge OK Led Ind.' is enabled. The Charge OK Led Ind. setting in MAIN FEATURE table. | Use GPIO as acive low to indicate charging complete. | IDC_STATIC_CHARGING_LED_SETTING4
 |  | bit1: 1bit |  | Shut Down Power in Off State | Dropdown menu | 0: Disable 1: Enable |  |  | Cut off the power when the speaker enter off state. | IDC_STATIC_MISC_OPTION21
 |  | bit2: 1bit |  | Charging Detect Enable | Dropdown menu | 0: Disable 1: Enable |  |  | Enable/disable charger function. | IDC_STATIC_CHARGING_SETTING1
 |  | bit3: 1bit |  | Battery Detection Enable | Dropdown menu | 0: Disable 1: Enable |  |  | Enable/Disable polling the battery voltage. | IDC_STATIC_BATTERY_DETECTION1
 |  | bit6:1bit |  | None | None |  |  | This bit will be enabled when 'Charging Detect Enable' is enabled | Enable charger for all USB battery charging type.
 |  | bit7:1bit |  | Ambient Temperature Charging Detection | Dropdown menu | 0: Disable 1: Degree 1: Customize; |  | Both degree and customize can enable the 'Ambient Temperature Charging Detection'. | Enable/Disable ambient temperature detection during charging. | IDC_STATIC_CHARGING_SETTING13
POWER_CFG_KEY_OPTION2 | 0x050B | bit0:1bit | 0x00 | Low Battery Debounce | Dropdown menu | 0: Disable 1: Enable |  |  | If this option is enabled, the low battery warning will keep until power adaptor in or power cycle. | IDC_STATIC_BATTERY_DETECTION9
 |  | bit1: 1bit |  | Re-Charging As Charge Complete | Dropdown menu | 0: Disable 1: Enable |  |  | If this option is enabled, the speaker will check the battery voltage every minute after charging complete. If the battery voltage is less than 4.1V, it will start charging again. | IDC_STATIC_CHARGING_SETTING3
 |  | bit2:1bit |  | Working Temperature | Dropdown menu | 0: Disable 1: Enable |  |  | If this option is set to enable: •In operation mode: Once the ambient temperature is out of working temperature range, app code will process power off procedure. •In power off mode: If the ambient temperature is out of working temperature range, product will not powered on. | IDC_STATIC_CHARGING_SETTING27
POWER_CFG_KEY_VOLTAGE_LEVELS | 0x050D | 2 | 0x0BB8 | Voltage Level for First Charging Stage | Dropdown menu | 0x0BB8: 3.0V 0x0C1C: 3.1V 0x0C80: 3.2V 0x0CE4: 3.3V … 0x1004: 4.1V 0x1068: 4.2V |  |  | Constant current voltage for charging stage 0. Range:(3V-to-4.2V) or( 3000 to 4200) Unit :Voltage. Size:2bytes | IDC_STATIC_CHARGING_SETTING6
 |  | 2 | 0x0C80 | Voltage Level for Second Charging Stage | Dropdown menu | 0x0BB8: 3.0V 0x0C1C: 3.1V 0x0C80: 3.2V 0x0CE4: 3.3V … 0x1004: 4.1V 0x1068: 4.2V |  |  | Constant current voltage for charging stage 1. Range:(3V-to-4.2V) or( 3000 to 4200) Unit :Voltage. Size:2bytes | IDC_STATIC_CHARGING_SETTING16
 |  | 2 | 0x0E74 | Voltage Level for Third Charging Stage | Dropdown menu | 0x0BB8: 3.0V 0x0C1C: 3.1V 0x0C80: 3.2V 0x0CE4: 3.3V … 0x1004: 4.1V 0x1068: 4.2V |  |  | Constant current voltage for charging stage 2. Range:(3V-to-4.2V) or( 3000 to 4200) Unit :Voltage. Size:2bytes | IDC_STATIC_CHARGING_SETTING7
 |  | 2 | 0x0FA0 | Voltage Level for Fourth Charging Stage | Dropdown menu | 0x0BB8: 3.0V 0x0C1C: 3.1V 0x0C80: 3.2V 0x0CE4: 3.3V … 0x1004: 4.1V 0x1068: 4.2V |  |  | Constant current voltage for charging stage 3. Range:(3V-to-4.2V) or( 3000 to 4200) Unit :Voltage. Size:2bytes | IDC_STATIC_CHARGING_SETTING24
POWER_CFG_KEY_MAX_CC_CHARGING_CURRENT | 0x050E | 2 | 0x001E | Maximum Charging Current for First Charging Stage | Text box | 0~455 |  |  | Maximum charging current(unit :mA) for charging stage 0 Unit :mA Range :0 - Max 455mA. | IDC_STATIC_CHARGING_SETTING8
 |  | 2 | 0x001E | Maximum Charging Current for Second Charging Stage | Text box | 0~455 |  |  | Maximum charging current(unit :mA) for charging stage 1 Unit :mA (0 - Max 455mA) | IDC_STATIC_CHARGING_SETTING22
 |  | 2 | 0x012C | Maximum Charging Current for Third Charging Stage | Text box | 0~455 |  |  | Maximum charging current(unit :mA) for charging stage 2 Unit :mA (0 - Max 455mA) | IDC_STATIC_CHARGING_SETTING12
 |  | 2 | 0x012C | Maximum Charging Current for Fourth Charging Stage | Text box | 0~455 |  |  | Maximum charging current(unit :mA) for charging stage 3 Unit :mA (0 - Max 455mA) | IDC_STATIC_CHARGING_SETTING25
POWER_CFG_KEY_LOW_BATTERY_WARNING_TIME | 0x050F | 1 | 0x1E | Low Battery Warning Time | Text box | 3~254 |  |  | When the voltage battery is lower than Warning_Battery_Level (the voltage setting for low battery), the speaker alerts users periodically with this interval(unit in 640 ms). | IDC_STATIC_WARRING_TIME2
POWER_CFG_KEY_STOP_WORKING_SAR_MIN | 0x0510 | 2 | 0x0092 | Stop Working SAR Min | Text box | Degree: 0x00C3: 35 degree C 0x00A7: 40 degree C 0x0092: 45 degree C 0x0082: 50 degree C 0x0072: 55 degree C Customize: 0000~FFFF |  |  | The minimum SAR voltage for ambient temperature detection to stop charger. | IDC_STATIC_CHARGING_SETTING30
POWER_CFG_KEY_STOP_WORKING_SAR_MAX | 0x0511 | 2 | 0x0331 | Stop Working SAR Max | Text box | Degree: 0x0331: -5 degree C 0x02B0: 0 degree C 0x0239: 5 degree C 0x01D6: 10 degree C 0x0186: 15 degree C Customize: 0000~FFFF |  |  | The maximum SAR voltage for ambient temperature detection to stop charger. | IDC_STATIC_CHARGING_SETTING32
LED_CFG_KEY_CHARGER_LED_OPTION | 0x0601 | bit[3~0]:4bit | 0x00 | Charging Complete Led Indication Setting | Dropdown menu | 0x00 Normal; 0x01 Led1 On Then Normal; 0x02 Led1 always On; 0x03 Led1 always Off; |  |  | 0x00:Normal, No extra action to indicate. 0x01:LED1 flash one time then return to normal. 0x02:LED1 always On. 0x03:LED1 always Off | IDC_STATIC_CHARGING_LED_SETTING2
 |  | bit[7~4]:4bit |  | Charging Error Led Indication Setting | Dropdown menu | 0x00 Same as Charge Complete; 0x01 Led2 Flash, Led1 Always Off; |  |  | 0x00 Same as charge Complete, The LED behavior is the same as charging complete. 0x01 LED2 keeping flash and LED1 always off | IDC_STATIC_CHARGING_LED_SETTING3
LED_CFG_KEY_STANDBY_LED_INDICATION | 0x0602 | 1 | 0x01 | On Duration | Text box | 1~254 |  |  | This the LED turn on duration for flash | IDC_STATIC_LED_ON_TIME
 |  | 1 | 0x04 | Off Duration | Text box | 1~254 |  |  | This the LED turn off duration for flash | IDC_STATIC_LED_OFF_TIME
 |  | 1 | 0x01 | Count | Text box | 0~254 |  |  | This is the number of the flash times for a round | IDC_STATIC_LED_COUNT
 |  | 1 | 0x64 | Interval | Text box | 0~254 |  |  | This is the time interval for a round | IDC_STATIC_LED_INTERVAL
 |  | 1 | 0x05 | Type | Dropdown menu | 0~9 |  |  | Select one LED display type for specific function | IDC_STATIC_LED_TYPE
LED_CFG_KEY_LINK_LED_INDICATION | 0x0603 | 1 | 0x01 | On Duration | Text box | 1~254 |  |  | This the LED turn on duration for flash | IDC_STATIC_LED_ON_TIME
 |  | 1 | 0x04 | Off Duration | Text box | 1~254 |  |  | This the LED turn off duration for flash | IDC_STATIC_LED_OFF_TIME
 |  | 1 | 0x02 | Count | Text box | 0~254 |  |  | This is the number of the flash times for a round | IDC_STATIC_LED_COUNT
 |  | 1 | 0x64 | Interval | Text box | 0~254 |  |  | This is the time interval for a round | IDC_STATIC_LED_INTERVAL
 |  | 1 | 0x05 | Type | Dropdown menu | 0~9 |  |  | Select one LED display type for specific function | IDC_STATIC_LED_TYPE
LED_CFG_KEY_TALK_LED_INDICATION | 0x0604 | 1 | 0x01 | On Duration | Text box | 1~254 |  |  | This the LED turn on duration for flash | IDC_STATIC_LED_ON_TIME
 |  | 1 | 0x04 | Off Duration | Text box | 1~254 |  |  | This the LED turn off duration for flash | IDC_STATIC_LED_OFF_TIME
 |  | 1 | 0x03 | Count | Text box | 0~254 |  |  | This is the number of the flash times for a round | IDC_STATIC_LED_COUNT
 |  | 1 | 0x3C | Interval | Text box | 0~254 |  |  | This is the time interval for a round | IDC_STATIC_LED_INTERVAL
 |  | 1 | 0x08 | Type | Dropdown menu | 0~9 |  |  | Select one LED display type for specific function | IDC_STATIC_LED_TYPE
LED_CFG_KEY_PAIRING_LED_INDICATION | 0x0605 | 1 | 0x0A | On Duration | Text box | 1~254 |  |  | This the LED turn on duration for flash | IDC_STATIC_LED_ON_TIME
 |  | 1 | 0x0A | Off Duration | Text box | 1~254 |  |  | This the LED turn off duration for flash | IDC_STATIC_LED_OFF_TIME
 |  | 1 | 0x00 | Count | Text box | 0~3 |  |  | This is the number of the flash times for a round | IDC_STATIC_LED_COUNT
 |  | 1 | 0x00 | Interval | Text box | 0~254 |  |  | This is the time interval for a round | IDC_STATIC_LED_INTERVAL
 |  | 1 | 0x09 | Type | Dropdown menu | 0~9 |  |  | Select one LED display type for specific function | IDC_STATIC_LED_TYPE
LED_CFG_KEY_POWER_ON_LED_INDICATION | 0x0606 | 1 | 0x02 | On Duration | Text box | 1~254 |  |  | This the LED turn on duration for flash | IDC_STATIC_LED_ON_TIME
 |  | 1 | 0x02 | Off Duration | Text box | 1~254 |  |  | This the LED turn off duration for flash | IDC_STATIC_LED_OFF_TIME
 |  | 1 | 0x03 | Count | Text box | 1~254 |  |  | This is the number of the flash times for a round | IDC_STATIC_LED_COUNT
 |  | 1 | 0x08 | Type | Dropdown menu | 0~9 |  |  | Select one LED display type for specific function | IDC_STATIC_LED_TYPE
LED_CFG_KEY_POWER_OFF_LED_INDICATION | 0x0607 | 1 | 0x02 | On Duration | Text box | 1~254 |  |  | This the LED turn on duration for flash | IDC_STATIC_LED_ON_TIME
 |  | 1 | 0x02 | Off Duration | Text box | 1~254 |  |  | This the LED turn off duration for flash | IDC_STATIC_LED_OFF_TIME
 |  | 1 | 0x03 | Count | Text box | 1~254 |  |  | This is the number of the flash times for a round | IDC_STATIC_LED_COUNT
 |  | 1 | 0x08 | Type | Dropdown menu | 0~9 |  |  | Select one LED display type for specific function | IDC_STATIC_LED_TYPE
LED_CFG_KEY_PAIRING_OK_LED_INDICATION | 0x0608 | 1 | 0x02 | On Duration | Text box | 1~254 |  |  | This the LED turn on duration for flash | IDC_STATIC_LED_ON_TIME
 |  | 1 | 0x02 | Off Duration | Text box | 1~254 |  |  | This the LED turn off duration for flash | IDC_STATIC_LED_OFF_TIME
 |  | 1 | 0x0A | Count | Text box | 0~254 |  |  | This is the number of the flash times for a round | IDC_STATIC_LED_COUNT
 |  | 1 | 0x05 | Type | Dropdown menu | 0~9 |  |  | Select one LED display type for specific function | IDC_STATIC_LED_TYPE
LED_CFG_KEY_LOW_BATTERY_LED_INDICATION | 0x0609 | 1 | 0x02 | On Duration | Text box | 1~254 |  |  | This the LED turn on duration for flash | IDC_STATIC_LED_ON_TIME
 |  | 1 | 0x02 | Off Duration | Text box | 1~254 |  |  | This the LED turn off duration for flash | IDC_STATIC_LED_OFF_TIME
 |  | 1 | 0x02 | Count | Text box | 1~254 |  |  | This is the number of the flash times for a round | IDC_STATIC_LED_COUNT
 |  | 1 | 0x04 | Type | Dropdown menu | 0~9 |  |  | Select one LED display type for specific function | IDC_STATIC_LED_TYPE
LED_CFG_KEY_AV_LED_INDICATION | 0x060A | 1 | 0x02 | On Duration | Text box | 1~254 |  |  | This the LED turn on duration for flash | IDC_STATIC_LED_ON_TIME
 |  | 1 | 0x02 | Off Duration | Text box | 1~254 |  |  | This the LED turn off duration for flash | IDC_STATIC_LED_OFF_TIME
 |  | 1 | 0x01 | Count | Text box | 0~3 |  |  | This is the number of the flash times for a round | IDC_STATIC_LED_COUNT
 |  | 1 | 0x64 | Interval | Text box | 0~254 |  |  | This is the time interval for a round | IDC_STATIC_LED_INTERVAL
 |  | 1 | 0x08 | Type | Dropdown menu | 0~9 |  |  | Select one LED display type for specific function | IDC_STATIC_LED_TYPE
LED_CFG_KEY_INCOMING_CALL_LED_INDICATION | 0x060B | 1 | 0x01 | On Duration | Text box | 1~254 |  |  | This the LED turn on duration for flash | IDC_STATIC_LED_ON_TIME
 |  | 1 | 0x03 | Off Duration | Text box | 1~254 |  |  | This the LED turn off duration for flash | IDC_STATIC_LED_OFF_TIME
 |  | 1 | 0x03 | Count | Text box | 0~3 |  |  | This is the number of the flash times for a round | IDC_STATIC_LED_COUNT
 |  | 1 | 0x64 | Interval | Text box | 0~254 |  |  | This is the time interval for a round | IDC_STATIC_LED_INTERVAL
 |  | 1 | 0x05 | Type | Dropdown menu | 0~9 |  |  | Select one LED display type for specific function | IDC_STATIC_LED_TYPE
LED_CFG_KEY_LINK_BACK_LED_INDICATION | 0x060C | 1 | 0x01 | On Duration | Text box | 1~254 |  |  | This the LED turn on duration for flash | IDC_STATIC_LED_ON_TIME
 |  | 1 | 0x03 | Off Duration | Text box | 1~254 |  |  | This the LED turn off duration for flash | IDC_STATIC_LED_OFF_TIME
 |  | 1 | 0x01 | Count | Text box | 0~3 |  |  | This is the number of the flash times for a round | IDC_STATIC_LED_COUNT
 |  | 1 | 0x0A | Interval | Text box | 0~254 |  |  | This is the time interval for a round | IDC_STATIC_LED_INTERVAL
 |  | 1 | 0x05 | Type | Dropdown menu | 0~9 |  |  | Select one LED display type for specific function | IDC_STATIC_LED_TYPE
LED_CFG_KEY_MULTILINK_LED_INDICATION | 0x060D | 1 | 0x01 | On Duration | Text box | 1~254 |  |  | This the LED turn on duration for flash | IDC_STATIC_LED_ON_TIME
 |  | 1 | 0x04 | Off Duration | Text box | 1~254 |  |  | This the LED turn off duration for flash | IDC_STATIC_LED_OFF_TIME
 |  | 1 | 0x02 | Count | Text box | 0~3 |  |  | This is the number of the flash times for a round | IDC_STATIC_LED_COUNT
 |  | 1 | 0x64 | Interval | Text box | 0~254 |  |  | This is the time interval for a round | IDC_STATIC_LED_INTERVAL
 |  | 1 | 0x04 | Type | Dropdown menu | 0~9 |  |  | Select one LED display type for specific function | IDC_STATIC_LED_TYPE
LED_CFG_KEY_MIC_MUTE_LED_INDICATION | 0x060E | 1 | 0x01 | On Duration | Text box | 1~254 |  |  | This the LED turn on duration for flash | IDC_STATIC_LED_ON_TIME
 |  | 1 | 0x04 | Off Duration | Text box | 1~254 |  |  | This the LED turn off duration for flash | IDC_STATIC_LED_OFF_TIME
 |  | 1 | 0x03 | Count | Text box | 0~3 |  |  | This is the number of the flash times for a round | IDC_STATIC_LED_COUNT
 |  | 1 | 0x3C | Interval | Text box | 0~254 |  |  | This is the time interval for a round | IDC_STATIC_LED_INTERVAL
 |  | 1 | 0x08 | Type | Dropdown menu | 0~9 |  |  | Select one LED display type for specific function | IDC_STATIC_LED_TYPE
LED_CFG_KEY_LINEIN_LED_INDICATION | 0x060F | 1 | 0x02 | On Duration | Text box | 1~254 |  |  | This the LED turn off duration for flash | IDC_STATIC_LED_ON_TIME
 |  | 1 | 0x02 | Off Duration | Text box | 1~254 |  |  | This is the number of the flash times for a round | IDC_STATIC_LED_OFF_TIME
 |  | 1 | 0x01 | Count | Text box | 0~3 |  |  | This is the time interval for a round | IDC_STATIC_LED_COUNT
 |  | 1 | 0x64 | Interval | Text box | 0~254 |  |  | This the LED turn on duration for flash | IDC_STATIC_LED_INTERVAL
 |  | 1 | 0xFF | Type | Dropdown menu |  |  |  | This the LED turn on duration for flash | IDC_STATIC_LED_TYPE
LED_CFG_KEY_VOL_ADJUST_LED_INDICATION | 0x0610 | 1 | 0x02 | On Duration | Text box | 1~254 |  |  | This the LED turn on duration for flash | IDC_STATIC_LED_ON_TIME
 |  | 1 | 0x02 | Off Duration | Text box | 1~254 |  |  | This is the number of the flash times for a round | IDC_STATIC_LED_OFF_TIME
 |  | 1 | 0x02 | Count | Text box | 0~254 |  |  | This the LED turn off duration for flash | IDC_STATIC_LED_COUNT
 |  | 1 | 0xFF | Type | Dropdown menu |  |  |  | This is the number of the flash times for a round | IDC_STATIC_LED_TYPE
LED_CFG_KEY_TWIN_MODE_PAIRING_MASTER_INDICATION | 0x0611 | 1 | 0x03 | On Duration | Text box | 1~254 |  |  | This the LED turn off duration for flash | IDC_STATIC_LED_ON_TIME
 |  | 1 | 0x03 | Off Duration | Text box | 1~254 |  |  | This is the number of the flash times for a round | IDC_STATIC_LED_OFF_TIME
 |  | 1 | 0x03 | Count | Text box | 0~3 |  |  | This is the time interval for a round | IDC_STATIC_LED_COUNT
 |  | 1 | 0x25 | Interval | Text box | 0~254 |  |  | This the LED turn on duration for flash | IDC_STATIC_LED_INTERVAL
 |  | 1 | 0x05 | Type | Dropdown menu |  |  |  | This the LED turn on duration for flash | IDC_STATIC_LED_TYPE
LED_CFG_KEY_TWIN_MODE_PAIRING_SLAVE_INDICATION | 0x0612 | 1 | 0x03 | On Duration | Text box | 1~254 |  |  | This the LED turn off duration for flash | IDC_STATIC_LED_ON_TIME
 |  | 1 | 0x03 | Off Duration | Text box | 1~254 |  |  | This is the number of the flash times for a round | IDC_STATIC_LED_OFF_TIME
 |  | 1 | 0x03 | Count | Text box | 0~3 |  |  | This is the time interval for a round | IDC_STATIC_LED_COUNT
 |  | 1 | 0x25 | Interval | Text box | 0~254 |  |  | This the LED turn on duration for flash | IDC_STATIC_LED_INTERVAL
 |  | 1 | 0x04 | Type | Dropdown menu |  |  |  | This the LED turn on duration for flash | IDC_STATIC_LED_TYPE
LED_CFG_KEY_TWIN_MODE_CONNECTED_BT_CONNECTED_MASTER_INDICATION | 0x0613 | 1 | 0x01 | On Duration | Text box | 1~254 |  |  | This the LED turn off duration for flash | IDC_STATIC_LED_ON_TIME
 |  | 1 | 0x04 | Off Duration | Text box | 1~254 |  |  | This is the number of the flash times for a round | IDC_STATIC_LED_OFF_TIME
 |  | 1 | 0x02 | Count | Text box | 0~3 |  |  | This is the time interval for a round | IDC_STATIC_LED_COUNT
 |  | 1 | 0x05 | Interval | Text box | 0~254 |  |  | This the LED turn on duration for flash | IDC_STATIC_LED_INTERVAL
 |  | 1 | 0x02 | Type | Dropdown menu |  |  |  | This the LED turn on duration for flash | IDC_STATIC_LED_TYPE
LED_CFG_KEY_TWIN_MODE_CONNECTED_BT_PAIRING_MASTER_INDICATION | 0x0614 | 1 | 0x03 | On Duration | Text box | 1~254 |  |  | This the LED turn off duration for flash | IDC_STATIC_LED_ON_TIME
 |  | 1 | 0x03 | Off Duration | Text box | 1~254 |  |  | This is the number of the flash times for a round | IDC_STATIC_LED_OFF_TIME
 |  | 1 | 0x00 | Count | Text box | 0~3 |  |  | This is the time interval for a round | IDC_STATIC_LED_COUNT
 |  | 1 | 0x01 | Interval | Text box | 0~254 |  |  | This the LED turn on duration for flash | IDC_STATIC_LED_INTERVAL
 |  | 1 | 0x05 | Type | Dropdown menu |  |  |  | This the LED turn on duration for flash | IDC_STATIC_LED_TYPE
LED_CFG_KEY_TWIN_MODE_CONNECTED_BT_PAGING_MASTER_INDICATION | 0x0615 | 1 | 0x02 | On Duration | Text box | 1~254 |  |  | This the LED turn off duration for flash | IDC_STATIC_LED_ON_TIME
 |  | 1 | 0x02 | Off Duration | Text box | 1~254 |  |  | This is the number of the flash times for a round | IDC_STATIC_LED_OFF_TIME
 |  | 1 | 0x01 | Count | Text box | 0~3 |  |  | This is the time interval for a round | IDC_STATIC_LED_COUNT
 |  | 1 | 0x64 | Interval | Text box | 0~254 |  |  | This the LED turn on duration for flash | IDC_STATIC_LED_INTERVAL
 |  | 1 | 0xff | Type | Dropdown menu |  |  |  | This the LED turn on duration for flash | IDC_STATIC_LED_TYPE
LED_CFG_KEY_TWIN_MODE_CONNECTED_BT_WAITING_MASTER_INDICATION | 0x0616 | 1 | 0x10 | On Duration | Text box | 1~254 |  |  | This the LED turn off duration for flash | IDC_STATIC_LED_ON_TIME
 |  | 1 | 0x10 | Off Duration | Text box | 1~254 |  |  | This is the number of the flash times for a round | IDC_STATIC_LED_OFF_TIME
 |  | 1 | 0x00 | Count | Text box | 0~3 |  |  | This is the time interval for a round | IDC_STATIC_LED_COUNT
 |  | 1 | 0x00 | Interval | Text box | 0~254 |  |  | This the LED turn on duration for flash | IDC_STATIC_LED_INTERVAL
 |  | 1 | 0x05 | Type | Dropdown menu |  |  |  | This the LED turn on duration for flash | IDC_STATIC_LED_TYPE
LED_CFG_KEY_TWIN_MODE_CONNECTED_BT_WAINTING_SLAVE_INDICATION | 0x0617 | 1 | 0x10 | On Duration | Text box | 1~254 |  |  | This the LED turn off duration for flash | IDC_STATIC_LED_ON_TIME
 |  | 1 | 0x10 | Off Duration | Text box | 1~254 |  |  | This is the number of the flash times for a round | IDC_STATIC_LED_OFF_TIME
 |  | 1 | 0x00 | Count | Text box | 0~3 |  |  | This is the time interval for a round | IDC_STATIC_LED_COUNT
 |  | 1 | 0x00 | Interval | Text box | 0~254 |  |  | This the LED turn on duration for flash | IDC_STATIC_LED_INTERVAL
 |  | 1 | 0x03 | Type | Dropdown menu |  |  |  | This the LED turn on duration for flash | IDC_STATIC_LED_TYPE
LED_CFG_KEY_BROADCAST_MODE_CONNECTED_BT_WAITING_SLAVE_INDICATION | 0x0618 | 1 | 0x10 | On Duration | Text box | 1~254 |  |  | This the LED turn off duration for flash | IDC_STATIC_LED_ON_TIME
 |  | 1 | 0x10 | Off Duration | Text box | 1~254 |  |  | This is the number of the flash times for a round | IDC_STATIC_LED_OFF_TIME
 |  | 1 | 0x00 | Count | Text box | 0~3 |  |  | This is the time interval for a round | IDC_STATIC_LED_COUNT
 |  | 1 | 0x00 | Interval | Text box | 0~254 |  |  | This the LED turn on duration for flash | IDC_STATIC_LED_INTERVAL
 |  | 1 | 0x03 | Type | Dropdown menu |  |  |  | This the LED turn on duration for flash | IDC_STATIC_LED_TYPE
LED_CFG_KEY_LED_OPTION | 0x0619 | bit0: 1bit | 0x00 | Line In Indicate Led | Dropdown menu | 0: Disable 1: Enable |  | This option can be configured only when 'CHG/AUX-IN' is enabled and P3_7 is selected. The CHG/AUX-IN setting in MAIN FEATURE table. | Use the GPIO pin to indicate Aux-in status. | IDC_STATIC_LINE_IN_SETTING5
 |  | bit1: 1bit |  | Charging Led Indication Setting | Dropdown menu | 0x00: Led2 on 0x01: Led2 off |  |  | Don't indicate the charging status in LED1 and LED2 if this option is enabled. | IDC_STATIC_CHARGING_LED_SETTING1
LED_CFG_KEY_LED_BRIGHTNESS | 0x061A | bit3[3~0]:4bit | 0x88 | LED2 Brightness | Dropdown menu | 0~15 |  |  | The brightness setting of LED2 | IDC_STATIC_LED_BRIGHTNESS_SETTING2
 |  | bit[7~4]:4bit |  | LED1 Brightness | Dropdown menu | 0~15 |  |  | The brightness setting of LED1 | IDC_STATIC_LED_BRIGHTNESS_SETTING1
LED_CFG_KEY_LOW_BATT_DISALLOW_POWER_ON_LED_INDICATION | 0x061B | 1 | 0x02 | On Duration | Text box | 1~254 |  |  | This the LED turn on duration for flash | IDC_STATIC_LED_ON_TIME
 |  | 1 | 0x02 | Off Duration | Text box | 1~254 |  |  | This is the number of the flash times for a round | IDC_STATIC_LED_OFF_TIME
 |  | 1 | 0x03 | Count | Text box | 0~254 |  |  | This the LED turn off duration for flash | IDC_STATIC_LED_COUNT
 |  | 1 | 0x08 | Type | Dropdown menu |  |  |  | This is the number of the flash times for a round | IDC_STATIC_LED_TYPE
TONE_CFG_KEY_TONE_SET | 0x0701 | 1 | 0X00 | Use Tone Set | Dropdown menu | Tone Set1 Tone Set2 Tone Set3 Tone Set4 |  |  | which tone set been used : currently support max 4 tone sets:(0~3) | IDC_STATIC_TONE_SETTING23
TONE_CFG_KEY_SHORT_PRESS_TONE | 0x0702 | 1 | 0x02 | Short Press Tone | Dropdown menu | 0~0x26 |  |  | Tone type for button short press. It is uesd if the option 'Button Press Alarm' is enabled or the triggered button event is related to HFP or voice functions such as voice dial and redial. | IDC_STATIC_TONE_SETTING1
TONE_CFG_KEY_LONG_PRESS_TONE | 0x0703 | 1 | 0x07 | Long Press Tone | Dropdown menu | 0~0x26 |  |  | Tone type for button long press. | IDC_STATIC_TONE_SETTING2
TONE_CFG_KEY_DOUBLE_CLICK_TONE | 0x0704 | 1 | 0x0D | Double Click Tone | Dropdown menu | 0~0x26 |  |  | Tone type for button double click. It is uesd if the option 'Button Press Alarm' is enabled or the triggered button event is related to HFP or voice functions such as voice dial and redial. | IDC_STATIC_TONE_SETTING3
TONE_CFG_KEY_LINK_QUALITY_WARNING_TONE | 0x0705 | 1 | 0x00 | Link Quality Warning Tone | Dropdown menu | 0~0x26 |  |  | Tone type when out of range | IDC_STATIC_TONE_SETTING28
TONE_CFG_KEY_TONE_SET_MASK | 0x0706 | bit0:1bit | 0x0F | Tone Set1 | Check box | 0: Not select 1: Select |  |  | Tone set mask(English). | IDC_CHK_TONE_SET1
 |  | bit1:1bit |  | Tone Set2 | Check box | 0: Not select 1: Select |  |  | Tone set mask(Chinese). | IDC_CHK_TONE_SET2
 |  | bit2:1bit |  | Tone Set3 | Check box | 0: Not select 1: Select |  |  | Tone set mask(Spanish). | IDC_CHK_TONE_SET3
 |  | bit3:1bit |  | Tone Set4 | Check box | 0: Not select 1: Select |  |  | Tone set mask(French). | IDC_CHK_TONE_SET4
TONE_CFG_KEY_CONNECTED_TONE2 | 0x0708 | 1 | 0x1B | Connected Second Profile Tone | Dropdown menu | 0~0x26 |  |  | Select the tone type for the second profile connected | IDC_STATIC_TONE_SETTING62
TONE_CFG_KEY_FUNCTION_ALARM_TONE | 0x0709 | 1 | 0x02 | Master Reset Tone | Dropdown menu | 0~0x26 |  |  | Tone type when specific function be triggered | IDC_STATIC_TONE_SETTING32
TONE_CFG_KEY_RINGTONE_VOLUME | 0x070A | 1 | 0x09 | Ring Tone Volume | Text box | 0~15 |  |  | Gain level(0~15) for fix ring tone volume usage | IDC_STATIC_TONE_SETTING20
TONE_CFG_KEY_TONE MODE[0] | 0x070B | 1 | 0x1E | Power On Tone | Dropdown menu | 0~0x26, 0x80 |  |  | Tone type for power on | IDC_STATIC_TONE_SETTING10
 |  | 1 | 0x1F | Power Off Tone | Dropdown menu | 0~0x26, 0x81 |  |  | Tone type for power off | IDC_STATIC_TONE_SETTING11
 |  | 1 | 0x1D | Enter Pairing Tone | Dropdown menu | 0~0x26, 0x82 |  |  | Tone type for enter pairing mode | IDC_STATIC_TONE_SETTING12
 |  | 1 | 0x02 | Pairing Complete Tone | Dropdown menu | 0~0x26, 0x83 |  |  | Tone type for pariring complete | IDC_STATIC_TONE_SETTING6
 |  | 1 | 0x00 | Pairing Not Complete Tone | Dropdown menu | 0~0x26, 0x84 |  |  | Tone type for pairing fail | IDC_STATIC_TONE_SETTING29
 |  | 1 | 0x1C | Incoming Call Tone | Dropdown menu | 0~0x26, 0x87 |  |  | Tone type for incoming call | IDC_STATIC_TONE_SETTING7
 |  | 1 | 0x00 | Reject Incoming Call Tone | Dropdown menu | 0~0x26, 0x88 |  |  | Tone type for rejecting an incoming call | IDC_STATIC_TONE_SETTING34
 |  | 1 | 0x1B | Call Actvie Tone | Dropdown menu | 0~0x26 |  |  | Tone type for answering a call | IDC_STATIC_TONE_SETTING4
 |  | 1 | 0x1A | End Call Tone | Dropdown menu | 0~0x26,0x89 |  |  | Tone type for ending a call | IDC_STATIC_TONE_SETTING5
 |  | 1 | 0x00 | Charging Initiate Tone | Dropdown menu | 0~0x26,0x8F |  |  | Tone type for charger initialize | IDC_STATIC_TONE_SETTING35
 |  | 1 | 0x00 | Charging Complete Tone | Dropdown menu | 0~0x26,0x90 |  |  | Tone type for charging is completed | IDC_STATIC_TONE_SETTING36
 |  | 1 | 0x00 | Battery Level 1 Tone | Dropdown menu | 0~0x26,0x8D |  |  | Tone type for battery level one.(>=3.5v) | IDC_STATIC_TONE_SETTING37
 |  | 1 | 0x00 | Battery Level 2 Tone | Dropdown menu | 0~0x26,0x8D |  |  | Tone type for battery level two.(>=3.6v) | IDC_STATIC_TONE_SETTING38
 |  | 1 | 0x00 | Battery Level 3 Tone | Dropdown menu | 0~0x26,0x8D |  |  | Tone type for battery level three.(>=3.7v) | IDC_STATIC_TONE_SETTING39
 |  | 1 | 0x00 | Battery Level 4 Tone | Dropdown menu | 0~0x26,0x8D |  |  | Tone type for battery level four.(>=3.8v) | IDC_STATIC_TONE_SETTING40
 |  | 1 | 0x00 | Battery Level 5 Tone | Dropdown menu | 0~0x26,0x8D |  |  | Tone type for battery level five.(>=3.9v) | IDC_STATIC_TONE_SETTING41
 |  | 1 | 0x00 | Battery Level 6 Tone | Dropdown menu | 0~0x26,0x8D |  |  | Tone type for battery level six.(>=4.0v) | IDC_STATIC_TONE_SETTING42
 |  | 1 | 0x00 | Full Battery Tone | Dropdown menu | 0~0x26,0x8E |  |  | Tone type when battery is full.(>=4.1v) | IDC_STATIC_TONE_SETTING43
 |  | 1 | 0x16 | Low Battery Tone | Dropdown menu | 0~0x26,0x8C |  |  | Tone type for battery low | IDC_STATIC_TONE_SETTING8
 |  | 1 | 0x0C | Max Volume Tone | Dropdown menu | 0~0x26,0x91 |  |  | Tone type when volume level is maximum | IDC_STATIC_TONE_SETTING44
 |  | 1 | 0x0C | Min Volume Tone | Dropdown menu | 0~0x26,0x92 |  |  | Tone type when volume level is minimum | IDC_STATIC_TONE_SETTING45
 |  | 1 | 0x00 | HF Connected Tone | Dropdown menu | 0~0x26,0x85 |  |  | Tone type for HF Connected | IDC_STATIC_TONE_SETTING27
 |  | 1 | 0x1B | Music Mode Ready Tone | Dropdown menu | 0~0x26 |  |  | Tone type when A2DP linked | IDC_STATIC_TONE_SETTING17
 |  | 1 | 0x00 | Link Disconnect Tone | Dropdown menu | 0~0x26,0x86 |  |  | Tone type for normal ACL link disconnect | IDC_STATIC_TONE_SETTING13
 |  | 1 | 0x0F | Link Loss Tone | Dropdown menu | 0~0x26,0x86 |  |  | Tone type for link lost | IDC_STATIC_TONE_SETTING18
 |  | 1 | 0x00 | Toggle Tone Set Tone | Dropdown menu | 0~0x26,0x93 |  |  | Tone type when changing tone set. | IDC_STATIC_TONE_SETTING46
 |  | 1 | 0x00 | Voice Dial Tone | Dropdown menu | 0~0x26,0x8A |  |  | Tone type when initiate voice dial. | IDC_STATIC_TONE_SETTING47
 |  | 1 | 0x00 | Last Number Redial Tone | Dropdown menu | 0~0x26,0x8B |  |  | Tone type when redialing last phone number. | IDC_STATIC_TONE_SETTING48
 |  | 1 | 0x00 | No Service Tone | Dropdown menu | 0~0x26 |  |  | Tone type for no service waring tone. | IDC_STATIC_TONE_SETTING9
 |  | 1 | 0x01 | Mute Tone | Dropdown menu | 0~0x26 |  |  | Tone type when micphone mute. | IDC_STATIC_TONE_SETTING15
 |  | 1 | 0x06 | Button Lock Tone | Dropdown menu | 0~0x26 |  |  | Tone type when button lock. | IDC_STATIC_TONE_SETTING16
TONE_CFG_KEY_CSB_ENTER_PAIRING_TONE | 0x070C | 1 | 0x0F | CSB Enter Pairing Tone | Dropdown menu | 0~0x26 |  |  | The tone rings when the speaker enters CSB pairing. | IDC_STATIC_TONE_SETTING53
TONE_CFG_KEY_CSB_CONNECTION_TONE | 0x070D | 1 | 0x02 | CSB Connect Tone | Dropdown menu | 0~0x26 |  |  | The tone rings when the CSB link is connected. If Master of CSB link is playing music at this moment, it won’t ring the tone. | IDC_STATIC_TONE_SETTING54
TONE_CFG_KEY_CSB_DISCONNECTION_TONE | 0x070E | 1 | 0x0F | CSB Disconnect Tone | Dropdown menu | 0~0x26 |  |  | The tone rings when the CSB link is disconnected. | IDC_STATIC_TONE_SETTING55
TONE_CFG_KEY_TONE_OPTION | 0x070F | bit0: 1bit | 0x10 | Incoming Call Repetition | Dropdown menu | 0: Disable 1: Enable |  |  | Repeat incoming call ring tone automatically. This option is used for multi-tone. It isn't suitable for voice prompt. | IDC_STATIC_TONE_SETTING33
 |  | bit1: 1bit |  | Fixed Ring Tone Volume | Dropdown menu | 0: Disable 1: Enable |  | Using 0x00C7 value as ring tone volume | If enabled, the gain level of ring tone gain will use fixed value. Otherwise, it has two conditions: 1. The ring tone volume will follow the volume of playing sound. 2. The ring tone gain level will use the level of SCO if no sound is playing. | IDC_STATIC_TONE_SETTING19
 |  | bit2: 1bit |  | MFB Long Press Force Alarm | Dropdown menu | 0: No 1: Yes |  |  | Always ring a long press tone when button 0 is pressed over the time of Long Button Press. The button 0 is MFB button. | IDC_STATIC_TONE_SETTING22
 |  | bit3: 1bit |  | Button Press Alarm | Dropdown menu | 0: No 1: Yes |  |  | Always ring a tone when button(s) is pressed. The tone type depends on pressing behavior, it may be short press tone, long press tone and double click tone. | IDC_STATIC_TONE_SETTING21
 |  | bit4: 1bit |  | Use 2nd Connected Tone | Dropdown menu | 0: Disable 1: Enable |  |  | Disable: Use dedicate profile connected tone setting. Enable: Use connected_tone2 as 2nd connected profile indication tone | IDC_STATIC_TONE_SETTING50
 |  | bit5: 1bit |  | Battery Status Prompt When Button Triggered | Dropdown menu | 0: Disable 1: Enable |  |  | Enable/Disable Battery status prompt when triggered by MMI event | IDC_STATIC_TONE_SETTING51
 |  | bit6: 1bit |  | Battery Status Prompt When Power On | Dropdown menu | 0: Disable 1: Enable |  |  | Enable/Disable Battery Status Prompt When Power On | IDC_STATIC_TONE_SETTING52
BUZZER_CFG_KEY_POWER_ON_BUZZER_MODE | 0x0801 | 1 | 0x03 | Power On Buzzer Mode | Dropdown menu | 0x00~0x12 |  |  | Select a buzzer type for power on action | IDC_STATIC_BUZZER_SETTING4
BUZZER_CFG_KEY_POWER_OFF_BUZZER_MODE | 0x0802 | 1 | 0x02 | Power Off Buzzer Mode | Dropdown menu | 0x00~0x12 |  |  | Select a buzzer type for power off action | IDC_STATIC_BUZZER_SETTING5
BUZZER_CFG_KEY_RING_BUZZER_MODE | 0x0803 | 1 | 0x05 | Ring Buzzer Mode | Dropdown menu | 0x00~0x12 |  |  | Select a buzzer type for receive an incoming call | IDC_STATIC_BUZZER_SETTING6
BUZZER_CFG_KEY_ENTER_PAIRING_BUZZER_MODE | 0x0804 | 1 | 0x0A | Enter Pairing Buzzer Mode | Dropdown menu | 0x00~0x12 |  |  | Select a buzzer type for enter pairing mode | IDC_STATIC_BUZZER_SETTING7
BUZZER_CFG_KEY_PAIRING_COMPLETE_BUZZER_MODE | 0x0805 | 1 | 0x04 | Pairing Complete Buzzer Mode | Dropdown menu | 0x00~0x12 |  |  | Select a buzzer type for pairing complete | IDC_STATIC_BUZZER_SETTING8
BUZZER_CFG_KEY_BATTERY_LOW_BUZZER_MODE | 0x0806 | 1 | 0x06 | Battery Low Buzzer Mode | Dropdown menu | 0x00~0x12 |  |  | Select a buzzer type for low battery status | IDC_STATIC_BUZZER_SETTING9
BUZZER_CFG_KEY_LINK_LOSS_BUZZER_MODE | 0x0807 | 1 | 0x0C | Link Loss Buzzer Mode | Dropdown menu | 0~0x12 |  |  | Select a buzzer type for link loss status | IDC_STATIC_BUZZER_SETTING13
BUZZER_CFG_KEY_LINK_WEAK_BUZZER_MODE | 0x0808 | 1 | 0x08 | Link Weak Buzzer Mode | Dropdown menu | 0~0x12 |  |  | Select a buzzer type for bad link quality | IDC_STATIC_BUZZER_SETTING14
BUZZER_CFG_KEY_FUNCTION_ALARM_BUZZER_MODE | 0x0809 | 1 | 0x0B | NFC Buzzer Mode | Dropdown menu | 0~0x12 |  |  | Select a buzzer type for NFC contect | IDC_STATIC_BUZZER_SETTING15
BUZZER_CFG_KEY_PIEZO_PWM_FREQ | 0x080A | 2 | 0x0A8C | Piezo PWM Frequency | Text box | 50~20000 |  |  | Key in the PWM frequency of buzzer | IDC_STATIC_BUZZER_SETTING12
BUZZER_CFG_KEY_OPTION | 0x080B | bit0: 1bit | 0x00 | Buzzer Output Type | Dropdown menu | 0: Pulse 1: PWM |  |  | Choose the buzzer type. Pulse: For 1/0 type buzzer PWM: For PWM type buzzer | IDC_STATIC_BUZZER_SETTING2
 |  | bit1: 1bit |  | Buzzer (in Mainfeature window) Buzzer Output Enable | Check box Dropdown menu | 0: Not Select 1: Select 0: Disable 1: Enable |  | The enable setting in MAIN FEATURE table | Select to enable buzzer function. | IDC_STATIC_BUZZER_SETTING1
 |  | bit2:1bit |  | None |  |  | None | This bit will be enabled when 'Buzzer Output Enable' is enabled | Used to record some function status for next power cycle.
 |  | bit3: 1bit |  | Buzzer Default On/Off | Dropdown menu | 0: Off; 1: On; |  |  | Buzzer turn On/Off after system do MASTER(factory) reset | IDC_STATIC_BUZZER_SETTING3
BTN_GPIO_CFG_KEY_BUTTON_OPERATION_NUM_0 | 0x0901 | 1 | 0x06 | None |  |  |  |  | The number of button operation in BTN_GPIO_CFG_KEY_BUTTON_TABLE_0.
BTN_GPIO_CFG_KEY_BUTTON_OPERATION_NUM_1 | 0x0903 | 1 | 0x00 | None |  |  |  |  | The number of button operation in BTN_GPIO_CFG_KEY_BUTTON_TABLE_1.
BTN_GPIO_CFG_KEY_BUTTON_OPERATION_NUM_2 | 0x0905 | 1 | 0x00 | None |  |  |  |  | The number of button operation in BTN_GPIO_CFG_KEY_BUTTON_TABLE_2.
BTN_GPIO_CFG_KEY_BUTTON_TABLE_0 | 0x0902 | 228 | {...} |  |  | 0x00 None 0x04 Answer 0x05 Reject 0x06 End Call 0x07 Toggle Mic Mute 0x08 Mic Mute 0x09 Mic Unmute 0x0a Initial Voice Dial 0x0b Cancel Voice Dial 0x0c Last Number Redial 0x0d Call Waiting(Switch to Second Phone) 0x0e Transfer to Phone 0x10 Join two calls 0x11 Release Waiting Call 0x12 Release Active Call and Accept Waiting Call 0x16 Connnect HF Link 0x17 Disconnect HF Link 0x30 Volume Up 0x31 Volume Down 0x32 Play 0x33 Stop 0x34 Forward 0x35 Backward 0x36 Fast Forward 0x37 Rewind 0x38 EQ Up 0x39 EQ Down 0x3a Lock Button 0x3b Disconnect AV Link 0x57 Force Speaker Gain Toggle 0x58 Button Indication Toggle 0x59 Function0 0x5a Function1 0x5b Function2 0x5c Function3 0x5d Pairing Mode 0x60 Toggle Buzzer 0x61 Mute Buzzer 0x62 Unmute Buzzer 0x18 Enable RX_NR 0x19 Disable RX_NR 0x1a Toggle RX_NR 0x1b Enable TX_NR 0x1c Disable TX_NR 0x1d Toggle TX_NR 0x1e Enable AEC 0x1f Disable AEC 0x20 Toggle AEC 0x21 Enable AEC_RX_NR 0x22 Disable AEC_RX_NR 0x23 Toggle AEC_RX_NR |  |  | GPIO button table0.
BTN_GPIO_CFG_KEY_BUTTON_TABLE_1 | 0x0904 | 228 | {...} |  |  |  |  |  | GPIO button table1.
BTN_GPIO_CFG_KEY_BUTTON_TABLE_2 | 0x0906 | 152 | {...} |  |  |  |  |  | GPIO button table2.
BTN_GPIO_CFG_KEY_POWER_ON_INTERVAL | 0x0907 | 1 | 0x1E | Power On | Text box | 0~254 |  |  | This is the time interval to turn on the power after pressing power button | IDC_STATIC_BUTTON_PRSEE_TIME1
BTN_GPIO_CFG_KEY_POWER_OFF_INTERVAL | 0x0908 | 1 | 0x1E | Power Off | Text box | 0~254 |  |  | This is the time interval to turn off the power after pressing power button | IDC_STATIC_BUTTON_PRSEE_TIME2
BTN_GPIO_CFG_KEY_RESET_TO_DEAFULT_TIMER | 0x0909 | 1 | 0x80 | Factory Default Timer | Text box | 0: Disable 10~254 |  |  | If system in off mode and power button been pressed over this time, system will clear some EEPROM parameter to default value. (It call "MASTER RESET", too. This timer must bigger than Enter Pairing Press Duration) | IDC_STATIC_FACTORY_DEFAULT_SETTING2
BTN_GPIO_CFG_KEY_OUTPUT_INDICATION_TABLE | 0x090A | 1 | {GPIO_NULL, GPIO_VALUE_LOW, GPIO_NULL, GPIO_VALUE_LOW, GPIO_NULL, GPIO_VALUE_LOW, GPIO_NULL, GPIO_VALUE_LOW, GPIO_NULL, GPIO_VALUE_LOW, GPIO_NULL, GPIO_VALUE_LOW, GPIO_NULL, GPIO_VALUE_LOW, GPIO_NULL, GPIO_VALUE_LOW} | Audio(SBC) Indication | Dropdown menu | GPIO_P00 = 0, /**< P00 */ GPIO_P01, /**< P01 */ GPIO_P02, /**< P02 */ GPIO_P03, /**< P03 */ GPIO_P04, /**< P04 */ GPIO_P05, /**< P05 */ GPIO_P06, /**< P06 */ GPIO_P07, /**< P07 */ GPIO_P10, /**< P10 */ GPIO_P11, /**< P11 */ GPIO_P12, /**< P12 */ GPIO_P13, /**< P13 */ GPIO_P14, /**< P14 */ GPIO_P15, /**< P15 */ GPIO_P16, /**< P16 */ GPIO_P17, /**< P17 */ GPIO_P20, /**< P20 */ GPIO_P21, /**< P21 */ GPIO_P22, /**< P22 */ GPIO_P23, /**< P23 */ GPIO_P24, /**< P24 */ GPIO_P25, /**< P25 */ GPIO_P26, /**< P26 */ GPIO_P27, /**< P27 */ GPIO_P30, /**< P30 */ GPIO_P31, /**< P31 */ GPIO_P32, /**< P32 */ GPIO_P33, /**< P33 */ GPIO_P34, /**< P34 */ GPIO_P35, /**< P35 */ GPIO_P36, /**< P36 */ GPIO_P37, /**< P37 */ GPIO_MFB, /**< MFB */ GPIO_NULL |  |  | Indicate when playing music | IDC_STATIC_INDICATE1_SETTING1
 |  | 1 |  | Audio(SBC) Indication GPIO polarity | Dropdown menu | 0: Low Active 1: High Active |  |  | The polarity of Audio Output_Indicator.
 |  | 1 |  | Voice(SCO) Indication | Dropdown menu | GPIO_P00 = 0, /**< P00 */ GPIO_P01, /**< P01 */ GPIO_P02, /**< P02 */ GPIO_P03, /**< P03 */ GPIO_P04, /**< P04 */ GPIO_P05, /**< P05 */ GPIO_P06, /**< P06 */ GPIO_P07, /**< P07 */ GPIO_P10, /**< P10 */ GPIO_P11, /**< P11 */ GPIO_P12, /**< P12 */ GPIO_P13, /**< P13 */ GPIO_P14, /**< P14 */ GPIO_P15, /**< P15 */ GPIO_P16, /**< P16 */ GPIO_P17, /**< P17 */ GPIO_P20, /**< P20 */ GPIO_P21, /**< P21 */ GPIO_P22, /**< P22 */ GPIO_P23, /**< P23 */ GPIO_P24, /**< P24 */ GPIO_P25, /**< P25 */ GPIO_P26, /**< P26 */ GPIO_P27, /**< P27 */ GPIO_P30, /**< P30 */ GPIO_P31, /**< P31 */ GPIO_P32, /**< P32 */ GPIO_P33, /**< P33 */ GPIO_P34, /**< P34 */ GPIO_P35, /**< P35 */ GPIO_P36, /**< P36 */ GPIO_P37, /**< P37 */ GPIO_MFB, /**< MFB */ GPIO_NULL |  |  | Indicate when SCO link established | IDC_STATIC_INDICATE1_SETTING2
 |  | 1 |  | Voice(SCO) Indication GPIO polarity | Dropdown menu | 0: Low Active 1: High Active |  |  | The polarity of Voice Output_Indicator.
 |  | 1 |  | Ring Tone Indication | Dropdown menu | GPIO_P00 = 0, /**< P00 */ GPIO_P01, /**< P01 */ GPIO_P02, /**< P02 */ GPIO_P03, /**< P03 */ GPIO_P04, /**< P04 */ GPIO_P05, /**< P05 */ GPIO_P06, /**< P06 */ GPIO_P07, /**< P07 */ GPIO_P10, /**< P10 */ GPIO_P11, /**< P11 */ GPIO_P12, /**< P12 */ GPIO_P13, /**< P13 */ GPIO_P14, /**< P14 */ GPIO_P15, /**< P15 */ GPIO_P16, /**< P16 */ GPIO_P17, /**< P17 */ GPIO_P20, /**< P20 */ GPIO_P21, /**< P21 */ GPIO_P22, /**< P22 */ GPIO_P23, /**< P23 */ GPIO_P24, /**< P24 */ GPIO_P25, /**< P25 */ GPIO_P26, /**< P26 */ GPIO_P27, /**< P27 */ GPIO_P30, /**< P30 */ GPIO_P31, /**< P31 */ GPIO_P32, /**< P32 */ GPIO_P33, /**< P33 */ GPIO_P34, /**< P34 */ GPIO_P35, /**< P35 */ GPIO_P36, /**< P36 */ GPIO_P37, /**< P37 */ GPIO_MFB, /**< MFB */ GPIO_NULL |  |  | Indicate when system has a ring tone | IDC_STATIC_INDICATE1_SETTING3
 |  | 1 |  | Ring Tone Indication GPIO polarity | Dropdown menu | 0: Low Active 1: High Active |  |  | The polarity of Ring Tone Output_Indicator.
 |  | 1 |  | Incoming Call Indication | Dropdown menu | GPIO_P00 = 0, /**< P00 */ GPIO_P01, /**< P01 */ GPIO_P02, /**< P02 */ GPIO_P03, /**< P03 */ GPIO_P04, /**< P04 */ GPIO_P05, /**< P05 */ GPIO_P06, /**< P06 */ GPIO_P07, /**< P07 */ GPIO_P10, /**< P10 */ GPIO_P11, /**< P11 */ GPIO_P12, /**< P12 */ GPIO_P13, /**< P13 */ GPIO_P14, /**< P14 */ GPIO_P15, /**< P15 */ GPIO_P16, /**< P16 */ GPIO_P17, /**< P17 */ GPIO_P20, /**< P20 */ GPIO_P21, /**< P21 */ GPIO_P22, /**< P22 */ GPIO_P23, /**< P23 */ GPIO_P24, /**< P24 */ GPIO_P25, /**< P25 */ GPIO_P26, /**< P26 */ GPIO_P27, /**< P27 */ GPIO_P30, /**< P30 */ GPIO_P31, /**< P31 */ GPIO_P32, /**< P32 */ GPIO_P33, /**< P33 */ GPIO_P34, /**< P34 */ GPIO_P35, /**< P35 */ GPIO_P36, /**< P36 */ GPIO_P37, /**< P37 */ GPIO_MFB, /**< MFB */ GPIO_NULL |  |  | Indicate when Incoming call | IDC_STATIC_INDICATE1_SETTING4
 |  | 1 |  | Incoming Call Indication GPIO polarity | Dropdown menu | 0: Low Active 1: High Active |  |  | The polarity of Incoming Call Output_Indicator.
 |  | 1 |  | External Amplifier Indication | Dropdown menu | GPIO_P00 = 0, /**< P00 */ GPIO_P01, /**< P01 */ GPIO_P02, /**< P02 */ GPIO_P03, /**< P03 */ GPIO_P04, /**< P04 */ GPIO_P05, /**< P05 */ GPIO_P06, /**< P06 */ GPIO_P07, /**< P07 */ GPIO_P10, /**< P10 */ GPIO_P11, /**< P11 */ GPIO_P12, /**< P12 */ GPIO_P13, /**< P13 */ GPIO_P14, /**< P14 */ GPIO_P15, /**< P15 */ GPIO_P16, /**< P16 */ GPIO_P17, /**< P17 */ GPIO_P20, /**< P20 */ GPIO_P21, /**< P21 */ GPIO_P22, /**< P22 */ GPIO_P23, /**< P23 */ GPIO_P24, /**< P24 */ GPIO_P25, /**< P25 */ GPIO_P26, /**< P26 */ GPIO_P27, /**< P27 */ GPIO_P30, /**< P30 */ GPIO_P31, /**< P31 */ GPIO_P32, /**< P32 */ GPIO_P33, /**< P33 */ GPIO_P34, /**< P34 */ GPIO_P35, /**< P35 */ GPIO_P36, /**< P36 */ GPIO_P37, /**< P37 */ GPIO_MFB, /**< MFB */ GPIO_NULL |  |  | External amplifier control. | IDC_STATIC_INDICATE1_SETTING5
 |  | 1 |  | External Amplifier Indication GPIO polarity | Dropdown menu | 0: Low Active 1: High Active |  |  | The polarity of AMP Output_Indicator.
 |  | 1 |  | HF Link Indication | Dropdown menu | GPIO_P00 = 0, /**< P00 */ GPIO_P01, /**< P01 */ GPIO_P02, /**< P02 */ GPIO_P03, /**< P03 */ GPIO_P04, /**< P04 */ GPIO_P05, /**< P05 */ GPIO_P06, /**< P06 */ GPIO_P07, /**< P07 */ GPIO_P10, /**< P10 */ GPIO_P11, /**< P11 */ GPIO_P12, /**< P12 */ GPIO_P13, /**< P13 */ GPIO_P14, /**< P14 */ GPIO_P15, /**< P15 */ GPIO_P16, /**< P16 */ GPIO_P17, /**< P17 */ GPIO_P20, /**< P20 */ GPIO_P21, /**< P21 */ GPIO_P22, /**< P22 */ GPIO_P23, /**< P23 */ GPIO_P24, /**< P24 */ GPIO_P25, /**< P25 */ GPIO_P26, /**< P26 */ GPIO_P27, /**< P27 */ GPIO_P30, /**< P30 */ GPIO_P31, /**< P31 */ GPIO_P32, /**< P32 */ GPIO_P33, /**< P33 */ GPIO_P34, /**< P34 */ GPIO_P35, /**< P35 */ GPIO_P36, /**< P36 */ GPIO_P37, /**< P37 */ GPIO_MFB, /**< MFB */ GPIO_NULL |  |  | Indicate when HF link established | IDC_STATIC_INDICATE1_SETTING6
 |  | 1 |  | HF Link Indication GPIO polarity | Dropdown menu | 0: Low Active 1: High Active |  |  | The polarity of HF Link Output_Indicator.
 |  | 1 |  | A2DP Link Indication | Dropdown menu | GPIO_P00 = 0, /**< P00 */ GPIO_P01, /**< P01 */ GPIO_P02, /**< P02 */ GPIO_P03, /**< P03 */ GPIO_P04, /**< P04 */ GPIO_P05, /**< P05 */ GPIO_P06, /**< P06 */ GPIO_P07, /**< P07 */ GPIO_P10, /**< P10 */ GPIO_P11, /**< P11 */ GPIO_P12, /**< P12 */ GPIO_P13, /**< P13 */ GPIO_P14, /**< P14 */ GPIO_P15, /**< P15 */ GPIO_P16, /**< P16 */ GPIO_P17, /**< P17 */ GPIO_P20, /**< P20 */ GPIO_P21, /**< P21 */ GPIO_P22, /**< P22 */ GPIO_P23, /**< P23 */ GPIO_P24, /**< P24 */ GPIO_P25, /**< P25 */ GPIO_P26, /**< P26 */ GPIO_P27, /**< P27 */ GPIO_P30, /**< P30 */ GPIO_P31, /**< P31 */ GPIO_P32, /**< P32 */ GPIO_P33, /**< P33 */ GPIO_P34, /**< P34 */ GPIO_P35, /**< P35 */ GPIO_P36, /**< P36 */ GPIO_P37, /**< P37 */ GPIO_MFB, /**< MFB */ GPIO_NULL |  |  | Indicate when A2DP link established | IDC_STATIC_INDICATE1_SETTING7
 |  | 1 |  | A2DP Link Indication GPIO polarity | Dropdown menu | 0: Low Active 1: High Active |  |  | The polarity of A2DP Output_Indicator.
 |  | 1 |  | Button Event Trigger Indication | Dropdown menu | GPIO_P00 = 0, /**< P00 */ GPIO_P01, /**< P01 */ GPIO_P02, /**< P02 */ GPIO_P03, /**< P03 */ GPIO_P04, /**< P04 */ GPIO_P05, /**< P05 */ GPIO_P06, /**< P06 */ GPIO_P07, /**< P07 */ GPIO_P10, /**< P10 */ GPIO_P11, /**< P11 */ GPIO_P12, /**< P12 */ GPIO_P13, /**< P13 */ GPIO_P14, /**< P14 */ GPIO_P15, /**< P15 */ GPIO_P16, /**< P16 */ GPIO_P17, /**< P17 */ GPIO_P20, /**< P20 */ GPIO_P21, /**< P21 */ GPIO_P22, /**< P22 */ GPIO_P23, /**< P23 */ GPIO_P24, /**< P24 */ GPIO_P25, /**< P25 */ GPIO_P26, /**< P26 */ GPIO_P27, /**< P27 */ GPIO_P30, /**< P30 */ GPIO_P31, /**< P31 */ GPIO_P32, /**< P32 */ GPIO_P33, /**< P33 */ GPIO_P34, /**< P34 */ GPIO_P35, /**< P35 */ GPIO_P36, /**< P36 */ GPIO_P37, /**< P37 */ GPIO_MFB, /**< MFB */ GPIO_NULL |  |  | Indicate when button event trigger | IDC_STATIC_INDICATE1_SETTING8
 |  | 1 |  | Button Event Trigger Indication GPIO polarity | Dropdown menu | 0: Low Active 1: High Active |  |  | The polarity of Button Trigger Output_Indicator.
BTN_GPIO_CFG_KEY_OPTION1 | 0x090B | bit1: 1bit | 0x00 | Slide Switch (in Mainfeature Window) | Check box | 0: Not Select 1: Select |  |  | For special HW design, use a GPIO pin to be slide switch detetion if this option is enabled. The GPIO pin is active low. (0: power on the speaker, 1: power off the speaker)
BTN_GPIO_CFG_KEY_ENTER_PAIRING_PRESS_TIME | 0x0911 | 1 | 0x32 | Enter Pairing | Text box | 10~254 |  |  | The parameter is the time to enter the paring mode from the power on state. The total time from power off state to enter pairing mode = "Enter Pairing" time + "Power On" time" | IDC_STATIC_BUTTON_PRSEE_TIME3
BTN_GPIO_CFG_KEY_SLIDE_SWITCH_IO, | 0x0912 | 1 | GPIO_NULL | Slide Switch (in Mainfeature Window) | Dropdown menu | GPIO_P00 = 0, /**< P00 */ GPIO_P01, /**< P01 */ GPIO_P02, /**< P02 */ GPIO_P03, /**< P03 */ GPIO_P04, /**< P04 */ GPIO_P05, /**< P05 */ GPIO_P06, /**< P06 */ GPIO_P07, /**< P07 */ GPIO_P10, /**< P10 */ GPIO_P11, /**< P11 */ GPIO_P12, /**< P12 */ GPIO_P13, /**< P13 */ GPIO_P14, /**< P14 */ GPIO_P15, /**< P15 */ GPIO_P16, /**< P16 */ GPIO_P17, /**< P17 */ GPIO_P20, /**< P20 */ GPIO_P21, /**< P21 */ GPIO_P22, /**< P22 */ GPIO_P23, /**< P23 */ GPIO_P24, /**< P24 */ GPIO_P25, /**< P25 */ GPIO_P26, /**< P26 */ GPIO_P27, /**< P27 */ GPIO_P30, /**< P30 */ GPIO_P31, /**< P31 */ GPIO_P32, /**< P32 */ GPIO_P33, /**< P33 */ GPIO_P34, /**< P34 */ GPIO_P35, /**< P35 */ GPIO_P36, /**< P36 */ GPIO_P37, /**< P37 */ GPIO_MFB, /**< MFB */ GPIO_NULL |  |  | GPIO configuration for slide switch
BTN_GPIO_CFG_KEY_NFC_DETECTION_IO, | 0x0913 | 1 | GPIO_NULL | NFC Detect | Dropdown menu |  |  |  | GPIO configuration for NFC detection
BTN_GPIO_CFG_KEY_BUZZER_IO, | 0x0915 | 1 | GPIO_NULL | Buzzer (in Mainfeature Window) | Dropdown menu |  |  |  | GPIO configuration for buzzer
BTN_GPIO_CFG_KEY_NSPK_SWITCH_CTRL_IO, | 0x0916 | 2 | GPIO_NULL | Switch Control (in Mainfeature Window) | Dropdown menu |  |  |  | GPIO configuration for default CSB role and channel setting
BTN_GPIO_CFG_KEY_CHARGER_INDICATION_IO, | 0x0917 | 1 | GPIO_NULL | Charger OK Led Ind (in Mainfeature Window) | Dropdown menu |  |  |  | GPIO configuration for extra charger indication
BTN_GPIO_CFG_KEY_AUX_IN_INDICATION_IO, | 0x0918 | 1 | GPIO_NULL | Aux In Led Ind (in Mainfeature Window) | Dropdown menu |  |  |  | GPIO configuration for aux in indication
BTN_GPIO_CFG_KEY_CP_RESET_IO, | 0x0919 | 1 | GPIO_NULL | CP Reset (in Mainfeature Window) | Dropdown menu |  |  |  | GPIO configuration for iAP CP reset pin
BTN_GPIO_CFG_KEY_AUX_IN_DETECTION_IO | 0x091A | 1 | GPIO_P32 | Aux In Detect (in Mainfeature Window) | Dropdown menu |  |  |  | GPIO configuration for aux in detection
BTN_GPIO_CFG_KEY_UART_TX_INDICATION_IO | 0x091B | 1 | GPIO_NULL | Tx Ind. (in Mainfeature Window) | Dropdown menu |  |  |  | GPIO configuration for UART TX indication (BM8x TX)
BTN_GPIO_CFG_KEY_UART_RX_INDICATION_IO | 0x091C | 1 | GPIO_NULL | Rx Ind. (in Mainfeature Window) | Dropdown menu |  |  |  | GPIO configuration for UART RX indication (BM8x RX)
MSPK_CFG_KEY_CSB_GROUP_ID | 0x0A01 | 2 | 0x0B36 | General Twin Mode Group Code | Text box |  |  | The option can be configured only when 'MSPK Pairing Scheme' is General. | The group code for general CSB pairing | IDC_STATIC_NSPK_SETTING9
MSPK_CFG_KEY_MODEL_ID | 0x0A02 | 2 | 0x0000 | Stereo Model ID |  |  |  |  | The model ID is used with "General Twin Mode Group Code" for Stereo Mode. It will disallow the speakers with different model IDs form the connection of Stereo Mode. | IDC_STATIC_NSPK_SETTING19
MSPK_CFG_KEY_CSB_SYNC_TIMEOUT | 0x0A04 | 1 | 0x1E | Twin Pairing Duration | Text box | 1~15 |  | Twin Pairing Duration' must greater than 'MSPK Recovery Pairing Duration'. | The CSB pairing timeout. (Unit: 5s) | IDC_STATIC_NSPK_SETTING2
MSPK_CFG_KEY_CSB_SYNC_ONEKEY_SLAVE_TIMEOUT | 0x0A05 | 1 | 0x03 | Twin Aux. Pairing Duration | Text box | 1~15 |  |  | The CSB pairing timeout of Slave role in One_Key_Operation. (Unit: 2s) When the One_Key_Operation is triggered, it enters CSB pairing as Slave role first and then change to Master role after this timeout occurs. | IDC_STATIC_NSPK_SETTING4
MSPK_CFG_KEY_NSPK_CHANNEL | 0x0A06 | 1 | 0x21 | MSPK Audio Channel | Dropdown menu | 0x00: Master(L+R)+Slave(L+R) 0x12: Master(L+L)+Slave(R+R) 0x21: Master(R+R)+Slave(L+L) 0x33: Master(mix)+Slave(mix) |  | The channel definition: 0: No Mixing, (L, R) 1: only output audio from left channel ,(L, L) 2: only output audio from right channel, (R,R) 3: mix the audio of left channel and right channel, ( (L + R)/2 , (L + R)/2 ) | Audio channel setting for multi-speaker. | IDC_STATIC_NSPK_STEREO_SETTING2
MSPK_CFG_KEY_NSPK_CHANNEL_DEFAULT | 0x0A09 | 1 | 0x21
MSPK_CFG_KEY_SHS_STATE_AFTER_CSB_NG | 0x0A07 | bit[1~0]: 2bit | 0xE4 | At Bluetooth Standby State | Check box | bit1~0: 00: Standby 01: Connected 10: Link Back 11: Pairing |  |  | SHS state after CSB creation complete while CSB is trigged in SHS STANDBY | IDC_STATIC_TWIN_PAIRING_FAILED_SETTING1
 |  | bit[3~2]: 2bit |  | At Bluetooth Connected State | Check box | bit3~2: 00: Standby 01: Connected 10: Link Back 11: Pairing |  |  | SHS state after CSB creation complete while CSB is trigged in SHS CONNECTED | IDC_STATIC_TWIN_PAIRING_FAILED_SETTING2
 |  | bit[5~4]: 2bit |  | At Bluetooth Link Back State | Check box | bit5~4: 00: Standby 01: Connected 10: Link Back 11: Pairing |  |  | SHS state after CSB creation complete while CSB is trigged in SHS PAGING | IDC_STATIC_TWIN_PAIRING_FAILED_SETTING3
 |  | bit[7~6]: 5bit |  | At Bluetooth Pairing State | Check box | bit7~6: 00: Standby 01: Connected 10: Link Back 11: Pairing |  |  | SHS state after CSB creation complete while CSB is trigged in SHS PAIRING | IDC_STATIC_TWIN_PAIRING_FAILED_SETTING4
MSPK_CFG_KEY_SHS_STATE_AFTER_CSB_MASTER_OK | 0x0A08 | bit[1~0]: 2bit | 0xE4 | At Bluetooth Standby State | Check box | bit1~0: 00: Standby 01: Connected 10: Link Back 11: Pairing |  |  | SHS state after CSB creation complete while CSB is trigged in SHS STANDBY | IDC_STATIC_TWIN_PAIRING_SUCCESS_SETTING1
 |  | bit[3~2]: 2bit |  | At Bluetooth Connected State | Check box | bit3~2: 00: Standby 01: Connected 10: Link Back 11: Pairing |  |  | SHS state after CSB creation complete while CSB is trigged in SHS CONNECTED | IDC_STATIC_TWIN_PAIRING_SUCCESS_SETTING2
 |  | bit[5~4]: 2bit |  | At Bluetooth Link Back State | Check box | bit5~4: 00: Standby 01: Connected 10: Link Back 11: Pairing |  |  | SHS state after CSB creation complete while CSB is trigged in SHS PAGING | IDC_STATIC_TWIN_PAIRING_SUCCESS_SETTING3
 |  | bit[7~6]: 5bit |  | At Bluetooth Pairing State | Check box | bit7~6: 00: Standby 01: Connected 10: Link Back 11: Pairing |  |  | SHS state after CSB creation complete while CSB is trigged in SHS PAIRING | IDC_STATIC_TWIN_PAIRING_SUCCESS_SETTING4
MSPK_CFG_KEY_CSB_TRIGGER_SYNC_SCHEME | 0x0A0A | bit[2~0]:3bit | 0x04 | Power On MSPK Mode Pairing Setting | Check box | bit2~0: 000: Not Enter Twin Mode 001: Factory Paired 010: Switch Control 100: Back To Last Mode |  | Factory Paired: This option is to pre-assign CSB role in EEPROM. If this option is enable, it will check 'Master Role' and 'Slave Role' option to determine which role should be used when the speaker power on. Switch Control: If this option is enabled, it will determine the CSB role and audio channel by two assigned GPIO pins combination. Back To Last Mode: If this option is enabled, the speaker will store the CSB role in EEPROM when it power off. Once the speaker power on again, the role and CSB link will be recovered if need. All above three options are checked when the speaker power on. If they conflict, the highest priority is 'Factory Paired', second is 'Switch Control' and the last is 'Back To Last Mode'. Not Enter Twin Mode: If this option is enabled, it will not enter twin mode pairing when power on. | Select twin mode pairing mode when power on. | IDC_STATIC_TWIN_MODE_PAIRING_SETTING
MSPK_CFG_KEY_CSB_TRIGGER_SYNC_ROLE_SETTING | 0x0A0B | bit0: 1bit | 0x00 | Master Role | Check box | 0: Not Select 1: Select |  |  | Select to be slave role. | IDC_RDO_TWIN_MASTER
 |  | bit1: 1bit |  | Slave Role | Check box | 0: Not Select 1: Select |  |  | Select to be master role. | IDC_RDO_TWIN_SLAVE
 |  | bit2: 1bit |  | External Amplifier/Indicate Pin 1 Polarity | Check box | 0: P0_4 as external amplifier/indcate Pin 1 driver 1: P1_5 as external amplifierr/indcate Pin 1 driver
MSPK_CFG_KEY_MSPK_OPTION1 | 0x0A0C | bit0: 1bit | 0x69 | Recover MSPK Link As Twin Speaker Link Loss | Dropdown menu | 0 : Disable 1 : Recovery |  |  | If this option is enabled, the speaker will try to recover the CSB link when the CSB link disconnects abnormally. | IDC_STATIC_NSPK_SETTING6
 |  | bit3:1bit |  | Default Multi Speaker Mode | Dropdown menu | 0: Stereo Mode 1: Concert Mode |  |  | Select to use stereo mode or concert mode. | IDC_STATIC_NSPK_SETTING18
 |  | bit5:1bit |  | Line In CSB | Dropdown menu | 0: Disable 1: Enable |  |  | Enable/Disable Broadcast/2-SPK Aux-in mode. | IDC_STATIC_LINE_IN_SETTING7
 |  | bit6:1bit |  | Concert Mode Link Status Record | Dropdown menu | 0: Disable 1: Enable |  |  | Enable/Disable broadcast back to last mode. | IDC_STATIC_MULTI_SPK_SETTING6
MSPK_CFG_KEY_MSPK_OPTION2 | 0x0A0D | bit4:1bit | 0x0B | Enable AAC Codec in CSB | Dropdown menu | 0: Disable 1: Enable |  |  |  | IDC_STATIC_MULTI_SPK_SETTING9
MSPK_CFG_KEY_CSB_ACCESS_CODE | 0x0A0F | 4 | {0} | Dedicate Twin Mode Access Code | Text box |  |  |  | The access code for dedicated CSB pairing. | IDC_STATIC_NSPK_SETTING5
IAP_CFG_KEY_BONDLESEEDIDPREFTOKEN | 0x0B01 | 0A | "M8BZ28GSX7" | Bondle Seed ID Pref Token | Text box | (10 characters) |  |  | Please refer to the \"MFi Accessory Firmware specification\". | IDC_STATIC_MFI_DESCRIPTION_SETTING1
IAP_CFG_KEY_SDKPROTOCOLTOKEN | 0x0B02 | 30 | "com.issc.datapath" | SDK Protocol Token | Text box | (48 characters) |  |  |  | IDC_STATIC_MFI_DESCRIPTION_SETTING2
IAP_CFG_KEY_APPBOUNDLEID | 0x0B03 | 30 | "com.microchip.BtChat-DualMode" | APP Boundle ID | Text box | (48 characters) |  |  |  | IDC_STATIC_MFI_DESCRIPTION_SETTING3
IAP_CFG_KEY_ACC_NAME | 0x0B04 | 10 | "Chatboard" | Accessory Name | Text box | (24 characters) |  |  |  | IDC_STATIC_MFI_DESCRIPTION_SETTING4
IAP_CFG_KEY_ACC_FW_VER | 0x0B05 | 3 | {0x01,0x00,0x00} | Accessory FW Version | Text box | (3 bytes) |  |  |  | IDC_STATIC_MFI_DESCRIPTION_SETTING5
IAP_CFG_KEY_ACC_HW_VER | 0x0B06 | 3 | {0x01,0x00,0x00} | Accessory HW Version | Text box | (3 bytes) |  |  |  | IDC_STATIC_MFI_DESCRIPTION_SETTING6
IAP_CFG_KEY_ACC_MANU | 0x0B07 | 10 | {"MCHP"} | Accessory Manu | Text box | (16 characters) |  |  |  | IDC_STATIC_MFI_DESCRIPTION_SETTING7
IAP_CFG_KEY_ACC_MODEL_NUM | 0x0B08 | 10 | "BM63" | Accessory Model Number | Text box | (24 characters) |  |  |  | IDC_STATIC_MFI_DESCRIPTION_SETTING8
IAP_CFG_KEY_ACC_SERIAL_NUM | 0x0B09 | 10 | "V2" | Accessory Serial Number | Text box | (16 bytes) |  |  |  | IDC_STATIC_MFI_DESCRIPTION_SETTING9
IAP_CFG_KEY_SDKPROTOCOLTOKEN2 | 0x0B0A | 30 | "com.issc.datapath2" | SDK Protocol Token | Text box | (48 characters) |  |  |  | IDC_STATIC_MFI_DESCRIPTION_SETTING11
IAP_CFG_KEY_OPTION | 0x0B0B | bit0: 1bit | 0x09 | Iap (in Mainfeature Window) | Check box | 0: Not Select 1: Select |  |  | iAP protocol is handled by BTM if this option is selected.
 |  | bit1:1bit |  | Burst iAP Transmission | Dropdown menu | 0: Disable 1: Enable |  |  | If this option is enabled, the accessory even no receiving a successful acknowledgment of an AccessoryDataTransfer command, the accessory may immediately send a new command containing available data for any session ID. | IDC_STATIC_MFI_TRANS_SETTING1
 |  | bit2:1bit |  | iAP Data Transmission | Dropdown menu | 0: Disable 1: Enable |  |  | Enable/Disable data retransmission. | IDC_STATIC_MFI_TRANS_SETTING2
 |  | bit3:1bit |  | iAP2 (in Mainfeature Window) | Check box | 0: Not Select 1: Select |  |  | Enable/disable iAP2 protocol.
 |  | bit4:1bit |  | Enable Auto Launch APP | Dropdown menu | 0: Disable 1: Enable |  |  | Enable/Disable auto launch APP. | IDC_STATIC_MFI_TRANS_SETTING3
 |  | bit3: 1bit |  | Tx IND | Check box | 0: Disable 1: Enable |  |  | Enable/Disable Tx Ind.
 |  |  |  | Power Switch Type | Dropdown menu | BTN_GPIO_CFG_KEY_OPTION1.bit0(ENABLE_BUTTON_0_WITHOUT_PWR_DETECT) SYS_CFG_KEY_OPTION1.bit3 (ENABLE_DIRECT_POWER_ON) BTN_GPIO_CFG_KEY_OPTION1.bit1(ENABLE_SLIDE_SWITCH_DETECT) SYS_CFG_KEY_OPTION1.bit1(ENABLE_APP_HCI_UART) SYS_CFG_KEY_OPTION3.bit6 (ENABLE_UART_COMMAND_POWER_ON) 1 1 0 0 0: Power On Directly 0 0 0 0 0: MFB Power On/Off 1 0 0 1 1: UART CMD Power On 1 0 1 0 0: Slide Switch |  | UART CMD Power On:Valid only when 'HCI Uart'check box is enabled in the MainFeature page. Slide Switch: Valid only when 'Slide Switch' check box is enabled in the MainFeature page. | Display with picture. | IDC_STATIC_POWER_SWITCH_SETTING1
END
