Scaniox/Glassphones/V2/electronics/components/ul_max9725aetc-/KiCAD/2022-04-11_15-45-50/MAX9725AETC+.step

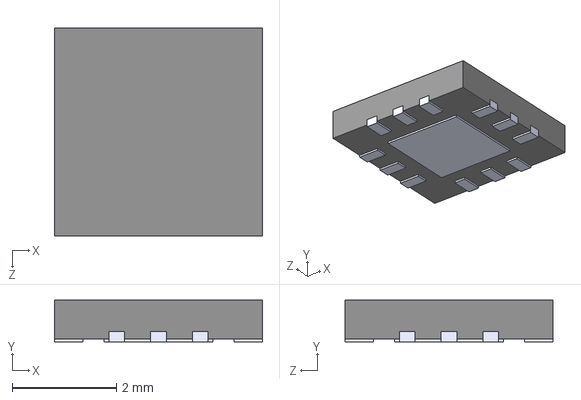
[picture p101: CAD file, 2022-04-24]
V2/electronics/components/ul_max9725aetc-/KiCAD/2022-04-11_15-45-50/MAX9725AETC+.step
4.00 x 0.8 x 4.00 mm
