Scaniox/Glassphones/V2/mechanical/power-led-1.snapshot.1/Power Led.stp

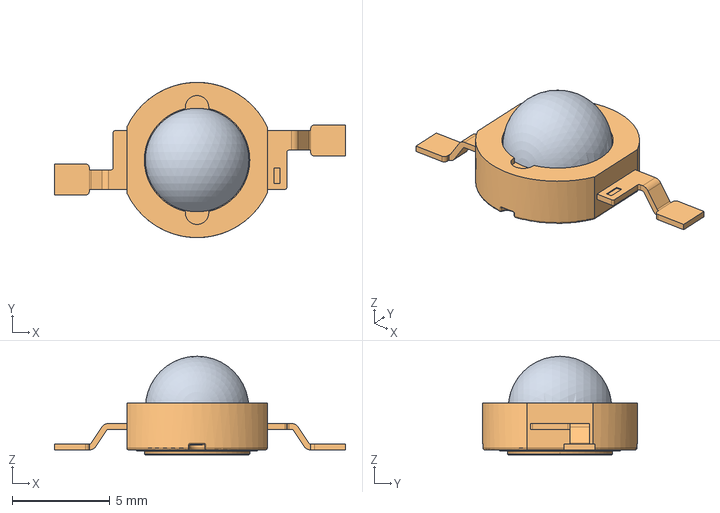
[picture p102: CAD file, 2022-11-03]
V2/mechanical/power-led-1.snapshot.1/Power Led.stp
14.9 x 7.95 x 5.05 mm
