Scaniox/Glassphones/V2/electronics/components/0.65mm pogo pin v0.step

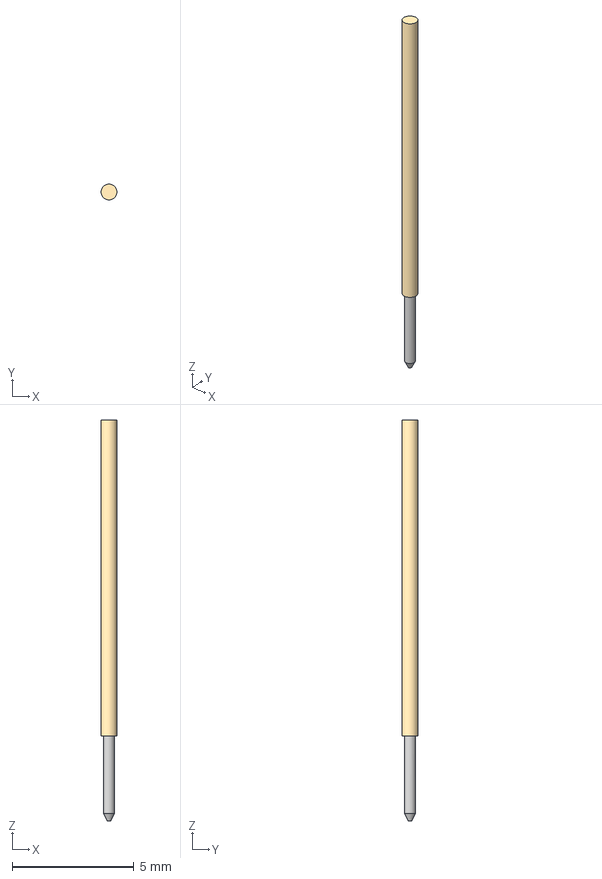
[picture p103: CAD file, 2022-04-24]
V2/electronics/components/0.65mm pogo pin v0.step
0.649 x 0.65 x 16.5 mm
