Scaniox/Glassphones/V2/electronics/components/df12Nx-20 connector/DF12NC-20DS-0.5V-51---3DModel-STEP-1.step

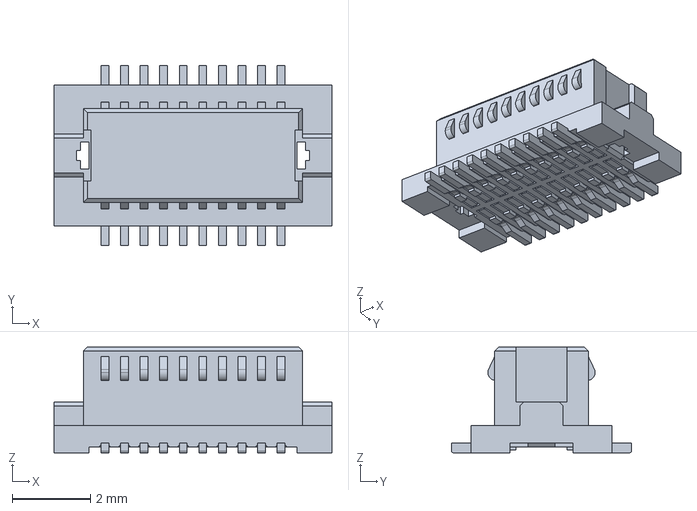
[picture p104: CAD file, 2022-04-24]
V2/electronics/components/df12Nx-20 connector/DF12NC-20DS-0.5V-51---3DModel-STEP-1.step
7.10 x 4.60 x 2.70 mm
