Scaniox/Glassphones/V2/electronics/components/df52 conn/DF52-4S-0.8H.stp

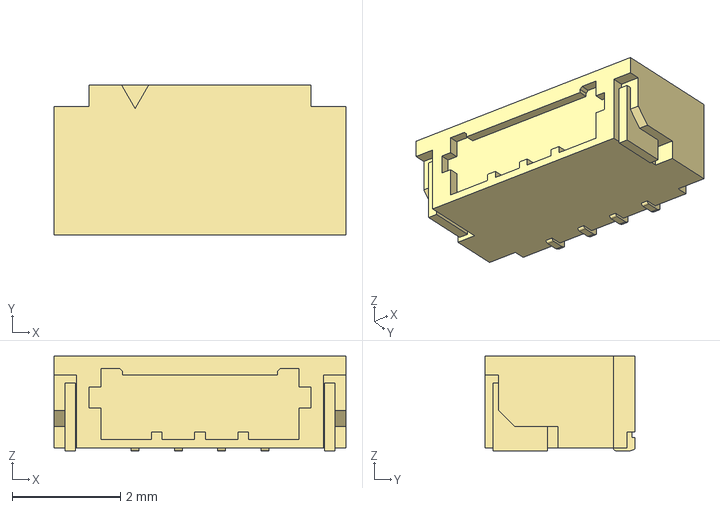
[picture p105: CAD file, 2022-04-24]
V2/electronics/components/df52 conn/DF52-4S-0.8H.stp
5.40 x 2.77 x 1.75 mm
