Scaniox/Glassphones/V2/electronics/components/df52 conn/DF52-5P-0.8C--3DModel-STEP-1.step

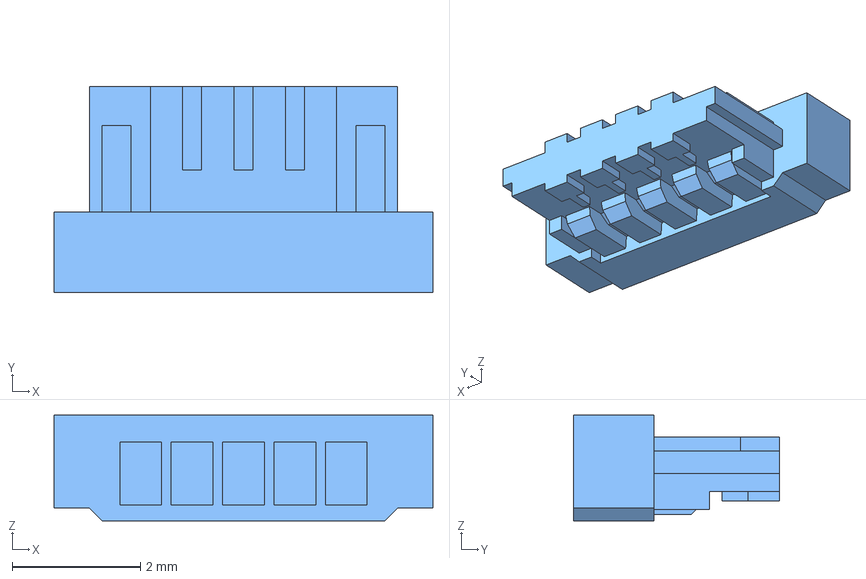
[picture p106: CAD file, 2022-04-24]
V2/electronics/components/df52 conn/DF52-5P-0.8C--3DModel-STEP-1.step
5.90 x 3.20 x 1.65 mm
