Scaniox/Glassphones/V2/electronics/components/df52 conn/DF52-5S-0.8H.stp

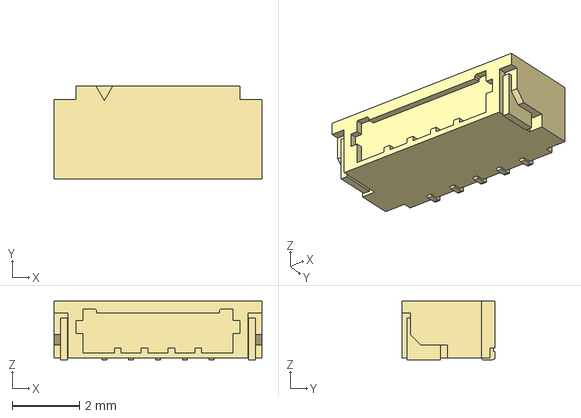
[picture p107: CAD file, 2021-08-21]
V2/electronics/components/df52 conn/DF52-5S-0.8H.stp
6.20 x 2.77 x 1.75 mm
