Scaniox/Glassphones/V1 - esp32/code/tests/pipeline_a2dp_sink_and_hfp/partitions_bt_sink_example.csv

# Espressif ESP32 Partition Table
#
# Note: if you change the phy_init or app partition offset
#       make sure to change the offset in Kconfig.projbuild
#
# Name,   Type, SubType, Offset,  Size, Flags
nvs,      data, nvs,     0x9000,  0x6000,
phy_init, data, phy,     0xf000,  0x1000,
factory,  app,  factory, 0x10000, 1200000,
