Scaniox/Glassphones/V1 - esp32/electronics/glassphones - main pcb/components/esp32 - tinypico/Shields/Play/Eagle/Shield_Play.brd

## EAGLE design V1 - esp32/electronics/glassphones - main pcb/components/esp32 - tinypico/Shields/Play/Eagle/Shield_Play.brd (2021-08-21)

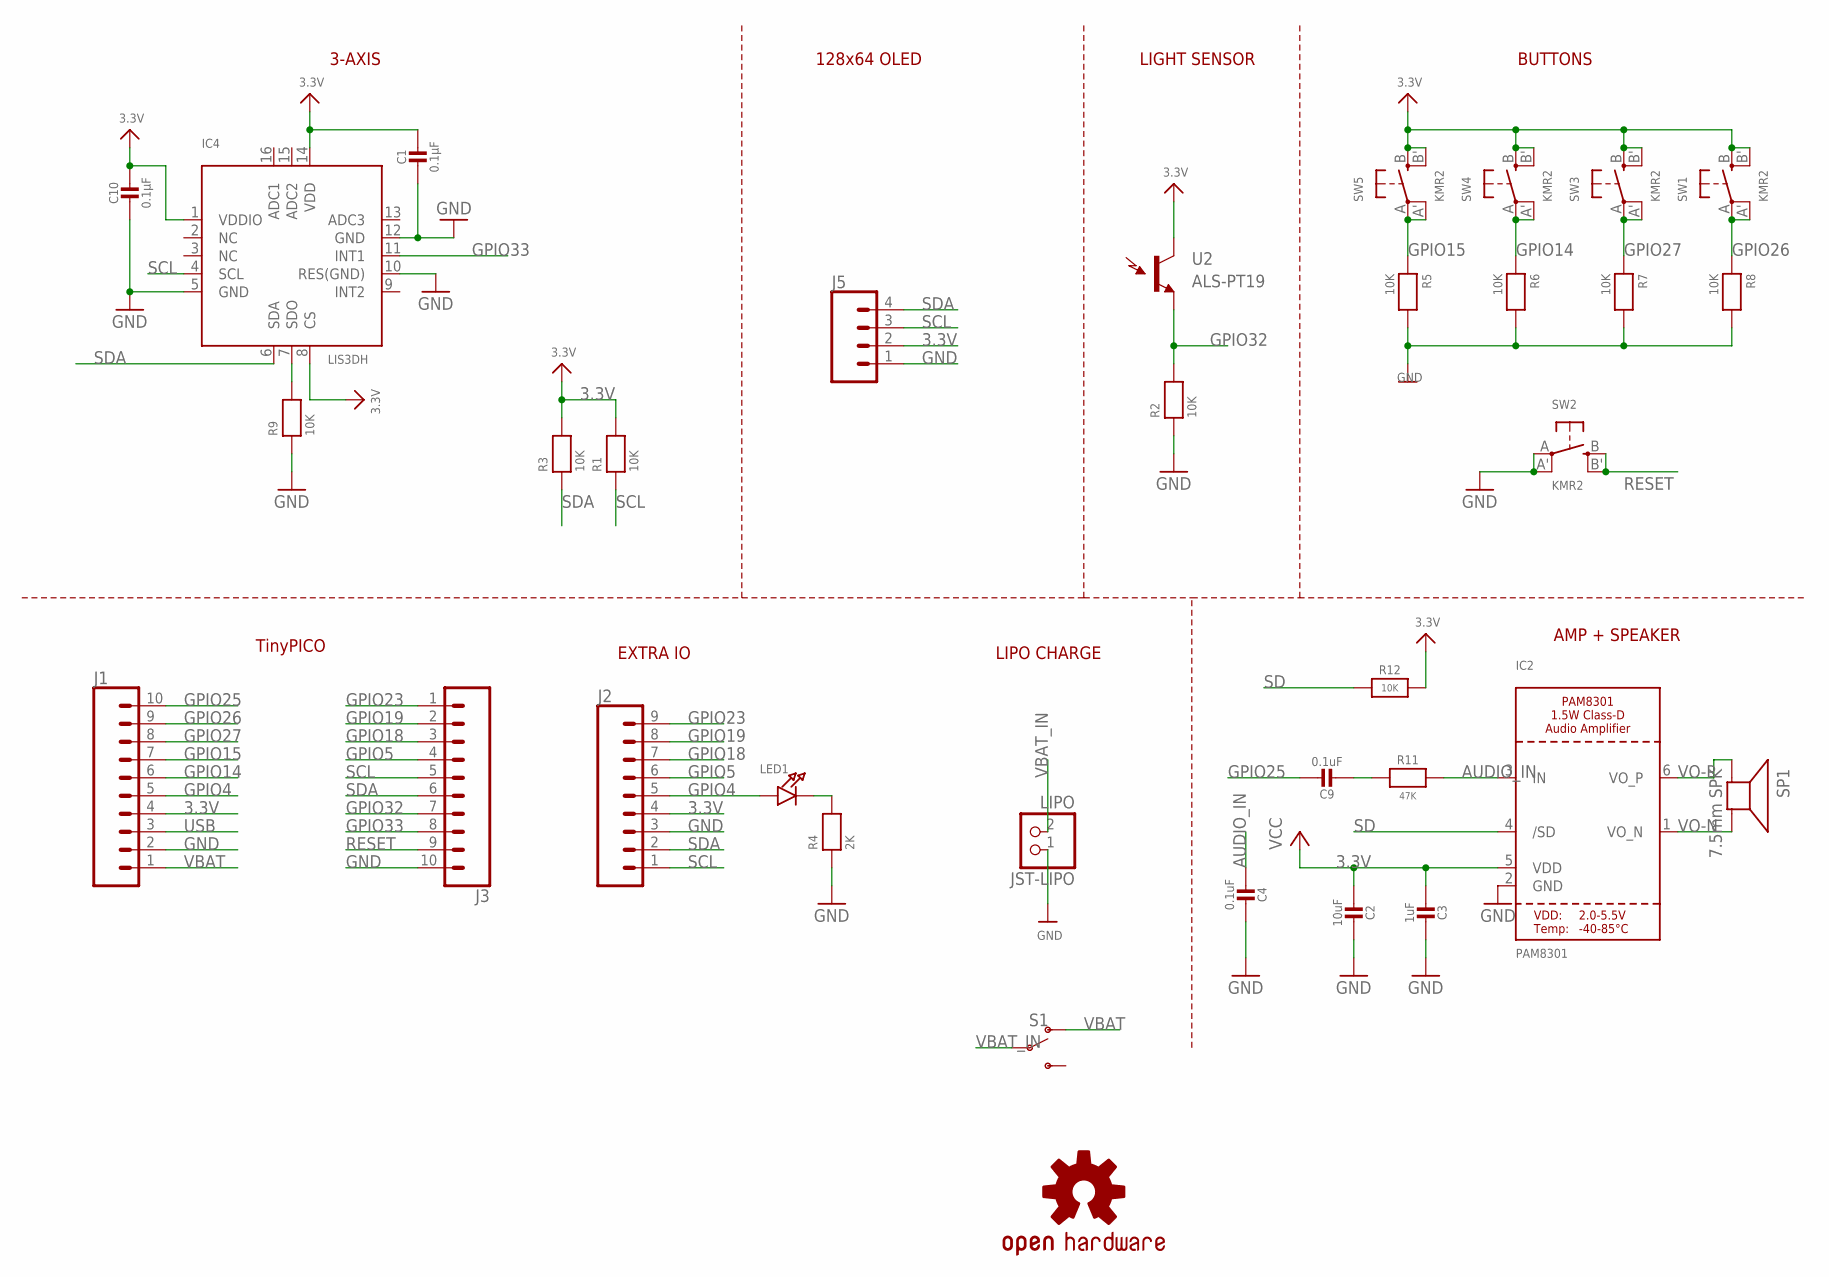
[picture p158: schematic Shield_Play.sch]

Parts:
C1, C10: 0.1µF; _0603MP
C2: 10uF; _0603MP
C3: 1uF; _0603MP
C4, C9: 0.1uF; _0603MP
IC2: PAM8301; SOT23-6
IC4: LIS3DH; LGA16_3X3MM
J1, J3: TINYPICO_HEADER_10NO_SILK_PTH_FEMALE; 1X10_NO_SILK
J2: CONN_09NO_SILK; 1X09_NO_SILK
J5: CONN_041X04_NO_SILK; 1X04_NO_SILK
JST-LIPO: LIPO; JSTPH2
LED1: LED0603_NOOUTLINE; CHIPLED_0603_NOOUTLINE
LOGO1: OSHW-LOGOS; OSHW-LOGO-S
R1, R2, R3, R5, R6, R7, R8, R9, R12: 10K; _0603MP
R4: 2K; _0603MP
R11: 47K; _0603MP
S1: SPARKFUN-SWITCHES_SWITCH-SPDT-SMD-RIGHT-ANGLE; SPARKFUN-SWITCHES_SWITCH_SPST_SMD_A
SP1: 7.5mm SPK; BUZZER_SMT_7.5MM
SW1, SW2, SW3, SW4, SW5: KMR2; BTN_KMR2_4.6X2.8
U2: ALS-PT19

Connections:
3.3V: C1.1, C2.2, C3.2, C10.1, IC2.5 (VDD), IC4.1 (VDDIO), IC4.8 (CS), IC4.14 (VDD), J1.4, J2.4, J5.2, R1.2, R3.2, R12.2, SW1.B (S), SW1.B' (S1), SW3.B (S), SW3.B' (S1), SW4.B (S), SW4.B' (S1), SW5.B (S), SW5.B' (S1), U2.C (C1)
AUDIO_IN: C4.2, IC2.3 (IN), R11.2
GND: C1.2, C2.1, C3.1, C4.1, C10.2, IC2.2 (GND), IC4.5 (GND), IC4.10 (RES(GND)), IC4.12 (GND), J1.2, J2.3, J3.10, J5.1, JST-LIPO.1, R2.1, R4.1, R5.2, R6.2, R7.2, R8.2, R9.1, SW2.A, SW2.A' (P1)
GPIO4: J1.5, J2.5, LED1.A
GPIO5: J2.6, J3.4
GPIO14: J1.6, R6.1, SW4.A, SW4.A' (P1)
GPIO15: J1.7, R5.1, SW5.A, SW5.A' (P1)
GPIO18: J2.7, J3.3
GPIO19: J2.8, J3.2
GPIO23: J2.9, J3.1
GPIO25: C9.1, J1.10
GPIO26: J1.9, R8.1, SW1.A, SW1.A' (P1)
GPIO27: J1.8, R7.1, SW3.A, SW3.A' (P1)
GPIO32: J3.7, R2.2, U2.E (E1)
GPIO33: IC4.11 (INT1), J3.8
unnamed: IC4.7 (SDO), R9.2
unnamed: LED1.C, R4.2
unnamed: C9.2, R11.1
RESET: J3.9, SW2.B (S), SW2.B' (S1)
SCL: IC4.4 (SCL), J2.1, J3.5, J5.3, R1.1
SD: IC2.4 (/SD), R12.1
SDA: IC4.6 (SDA), J2.2, J3.6, J5.4, R3.1
USB: J1.3
VBAT: J1.1, S1.1 (O)
VBAT_IN: JST-LIPO.2, S1.2
VO-N: IC2.1 (VO_N), SP1.-
VO-P: IC2.6 (VO_P), SP1.+

Notes on the sheet:
TinyPICO
LIPO CHARGE
BUTTONS
LIGHT SENSOR
3-AXIS
128x64 OLED
EXTRA IO
AMP + SPEAKER

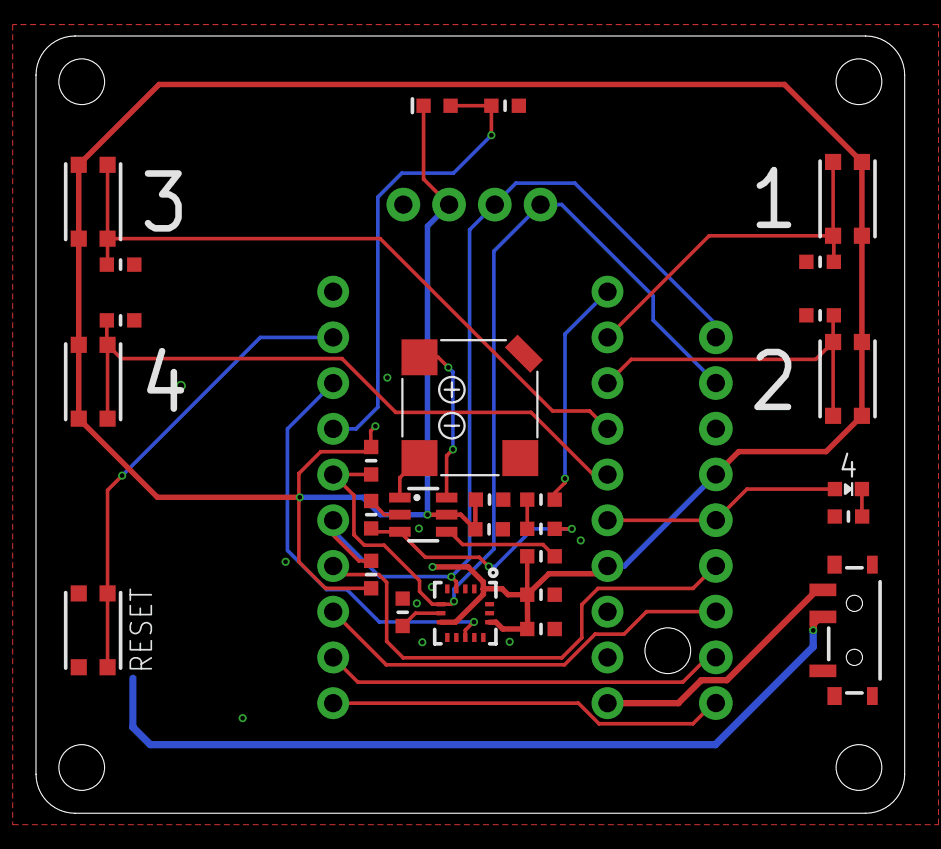
[picture p159: board Shield_Play.brd from above]

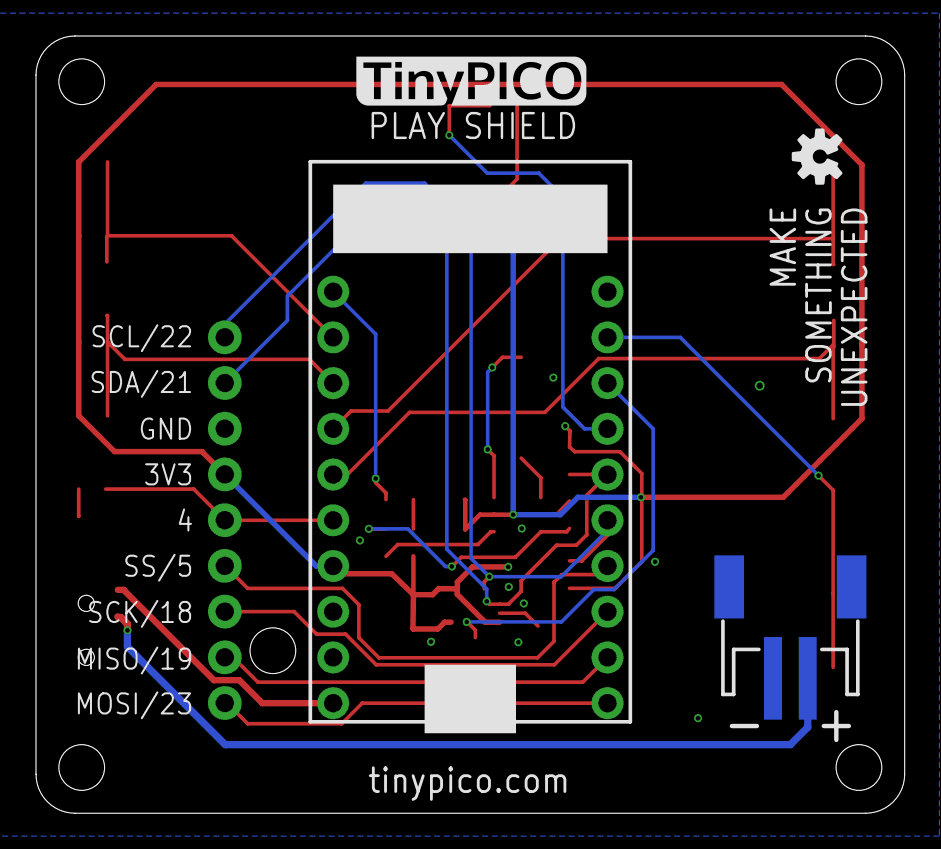
[picture p160: board Shield_Play.brd from below]

Board: 2 copper layers, 48.3 x 43.2 mm, 34 parts (2 on the bottom side), 26 nets.
