Scaniox/Glassphones/V1 - esp32/electronics/glassphones - main pcb/components/esp32 - tinypico/Shields/IPS Colour Display/Eagle/Shield_IPS_Color_Display.brd

## EAGLE design V1 - esp32/electronics/glassphones - main pcb/components/esp32 - tinypico/Shields/IPS Colour Display/Eagle/Shield_IPS_Color_Display.brd (2021-08-21)

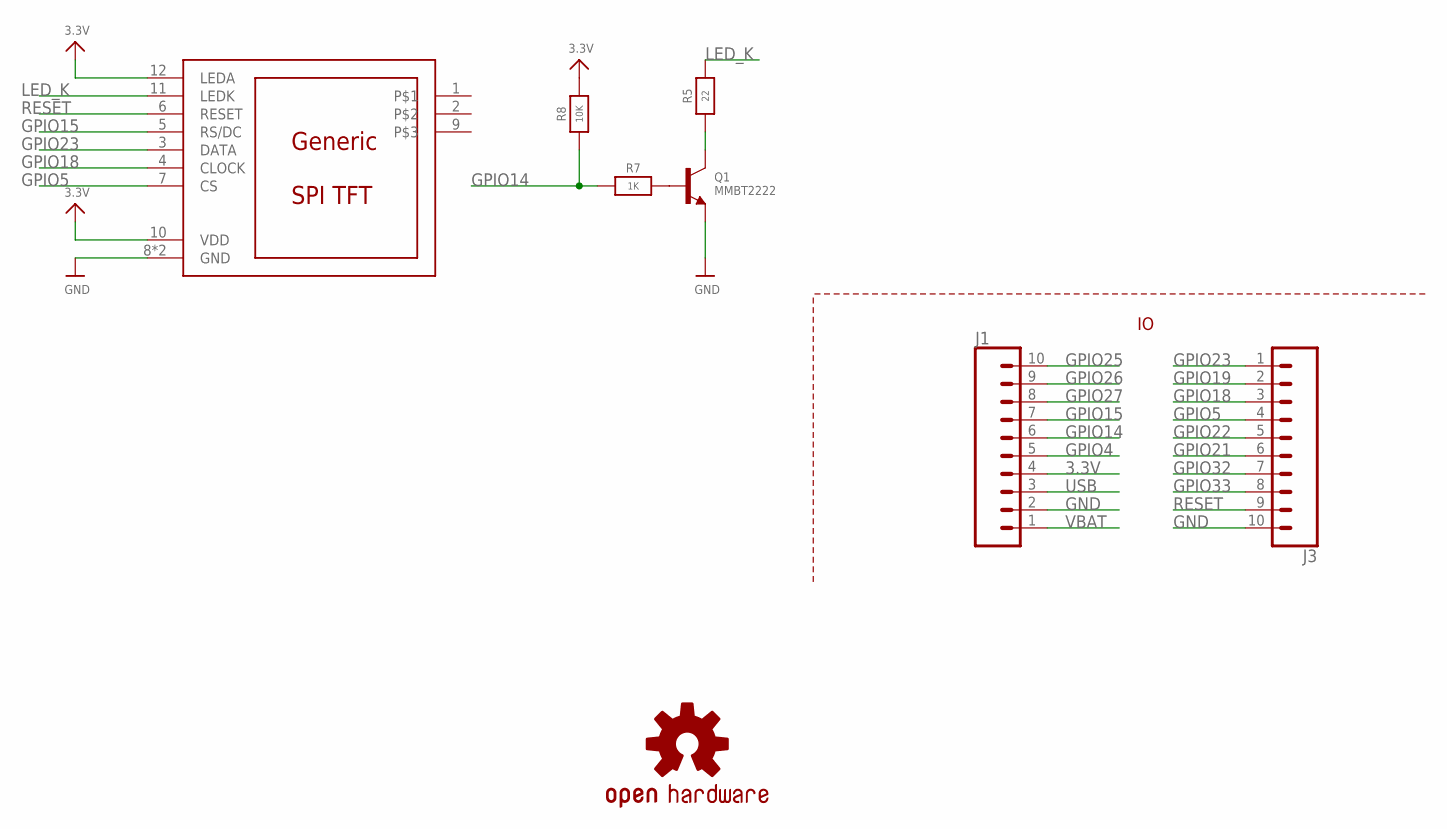
[picture p161: schematic Shield_IPS_Color_Display.sch]

Parts:
J1, J3: TINYPICO_HEADER_10SQR; 1X10_NO_SILK_SQR
LOGO1: OSHW-LOGOS; OSHW-LOGO-S
Q1: MMBT2222; SOT23-WIDE
R5: 22; _0603MP
R7: 1K; _0603MP
R8: 10K; _0603MP
U$2: MICROBUILDER_DISP_LCD_0.9IN_160X80; MICROBUILDER_TFT_0.96IN_160X80

Connections:
3.3V: J1.4, R8.2, U$2.10 (VDD), U$2.12 (LEDA)
GND: J1.2, J3.10, Q1.2 (E), U$2.8 (GND), U$2.13 (GND)
GPIO4: J1.5
GPIO5: J3.4, U$2.7 (CS)
GPIO14: J1.6, R7.1, R8.1
GPIO15: J1.7, U$2.5 (RS/DC)
GPIO18: J3.3, U$2.4 (CLOCK)
GPIO19: J3.2
GPIO21: J3.6
GPIO22: J3.5
GPIO23: J3.1, U$2.3 (DATA)
GPIO25: J1.10
GPIO26: J1.9
GPIO27: J1.8
GPIO32: J3.7
GPIO33: J3.8
LED_K: R5.2, U$2.11 (LEDK)
unnamed: Q1.1 (B), R7.2
unnamed: Q1.3 (C), R5.1
RESET: J3.9, U$2.6 (RESET)
USB: J1.3
VBAT: J1.1

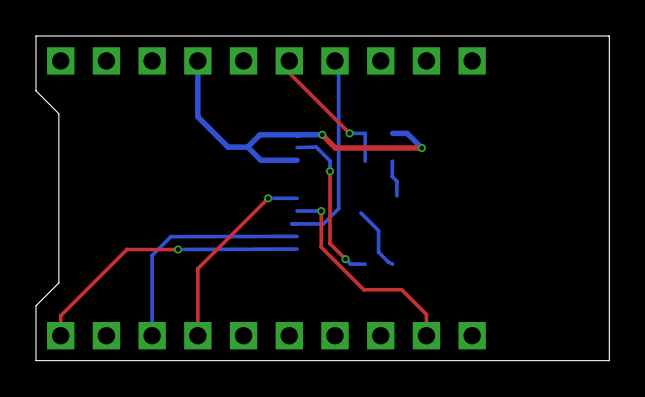
[picture p162: board Shield_IPS_Color_Display.brd from above]

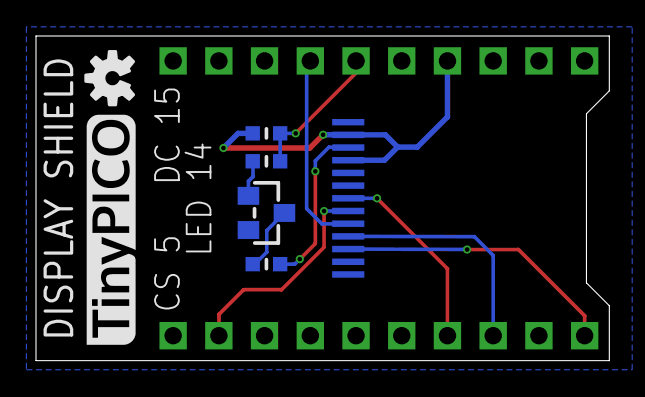
[picture p163: board Shield_IPS_Color_Display.brd from below]

Board: 2 copper layers, 31.9 x 18.0 mm, 8 parts (6 on the bottom side), 11 nets.
