Scaniox/Glassphones/V1 - esp32/electronics/glassphones - main pcb/components/esp32 - tinypico/Shields/RTC/Eagle/Shield_RTC_MCP7940N.brd

## EAGLE design V1 - esp32/electronics/glassphones - main pcb/components/esp32 - tinypico/Shields/RTC/Eagle/Shield_RTC_MCP7940N.brd (2021-08-21)

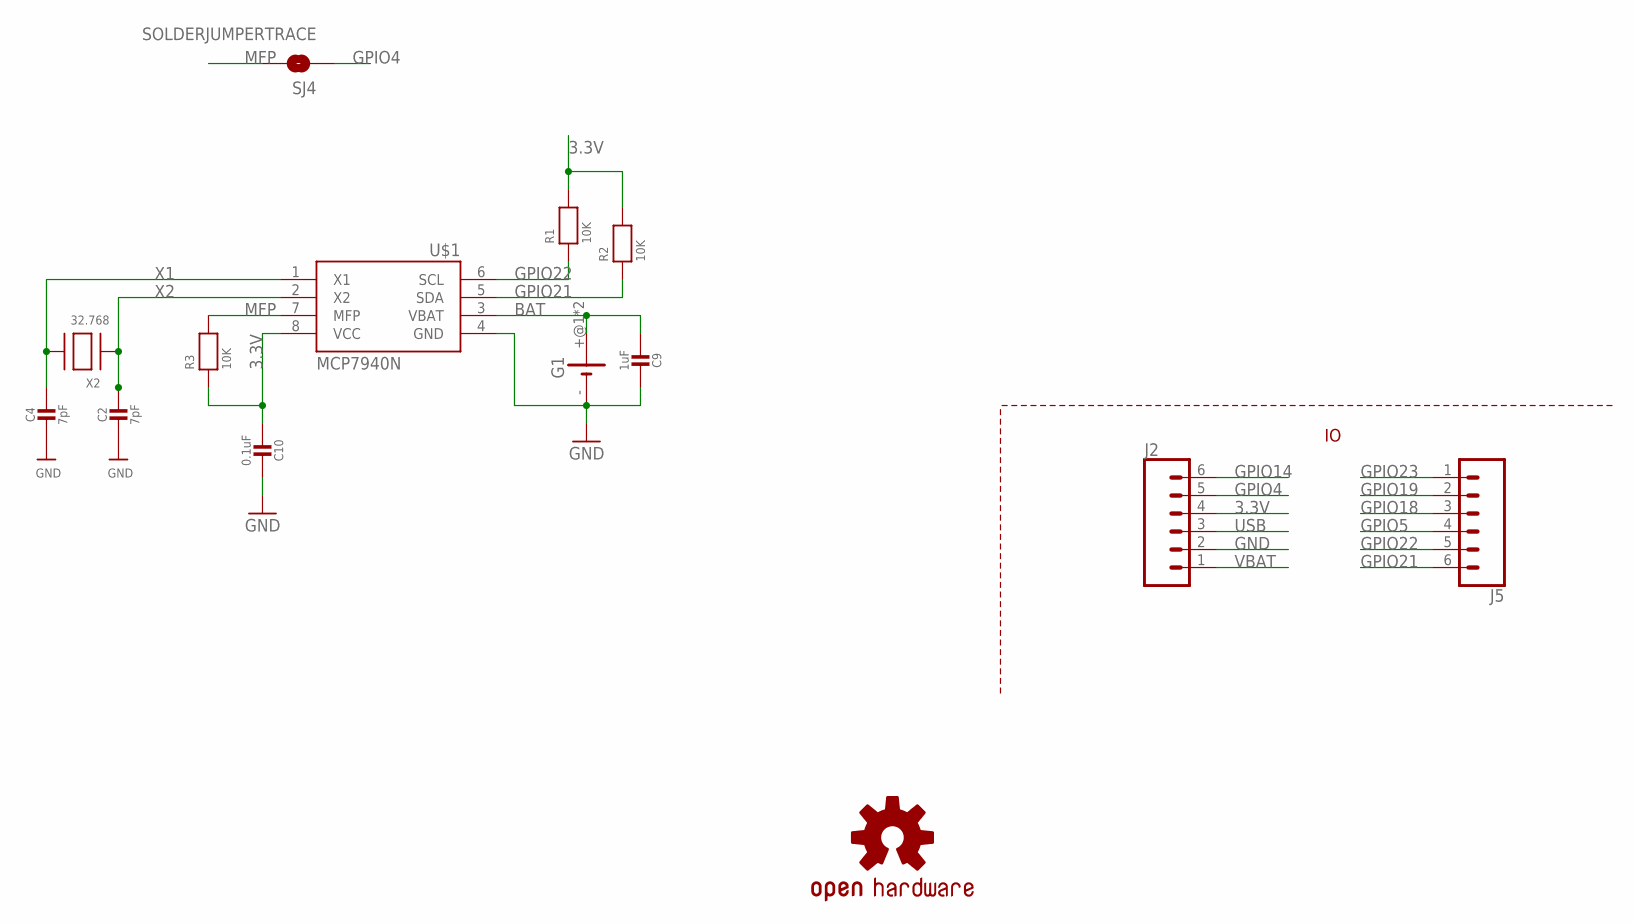
[picture p164: schematic Shield_RTC_MCP7940N.sch]

Parts:
C2, C4: 7pF; _0603MP
C9: 1uF; _0603MP
C10: 0.1uF; _0603MP
G1: 10MM_SM_COIN_CELL_CLIP
J2, J5: CONN_06NO_SILK_FEMALE_PTH; 1X06_NO_SILK
LOGO1: OSHW-LOGOS; OSHW-LOGO-S
R1, R2, R3: 10K; _0603MP
SJ4: SOLDERJUMPERTRACE; SPARKFUN_SJ_2S-TRACE
U$1: MCP7940N; SOIC8_150MIL
X2: 32.768; XTAL3215

Connections:
3.3V: C10.2, J2.4, R1.2, R2.2, R3.1, U$1.8 (VCC)
BAT: C9.2, G1.+@1 (+), G1.+@2 (+), U$1.3 (VBAT)
GND: C2.2, C4.2, C9.1, C10.1, G1.-, J2.2, U$1.4 (GND)
GPIO4: J2.5, SJ4.1
GPIO5: J5.4
GPIO14: J2.6
GPIO18: J5.3
GPIO19: J5.2
GPIO21: J5.6, R2.1, U$1.5 (SDA)
GPIO22: J5.5, R1.1, U$1.6 (SCL)
GPIO23: J5.1
MFP: R3.2, SJ4.2, U$1.7 (MFP)
USB: J2.3
VBAT: J2.1
X1: C4.1, U$1.1 (X1), X2.P$2
X2: C2.1, U$1.2 (X2), X2.P$1
