Scaniox/Glassphones/V1 - esp32/electronics/glassphones - main pcb/components/esp32 - tinypico/Shields/RTC/Eagle/Shield_RTC_MCP7940N.brd

## EAGLE design V1 - esp32/electronics/glassphones - main pcb/components/esp32 - tinypico/Shields/RTC/Eagle/Shield_RTC_MCP7940N.brd (continued)

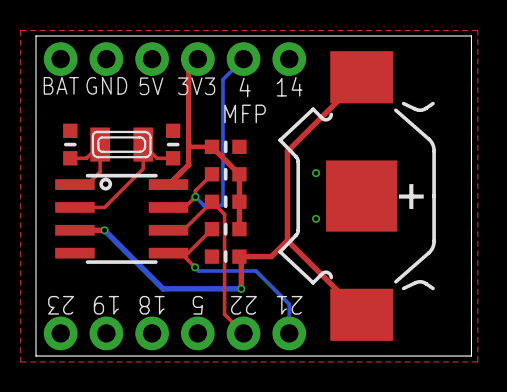
[picture p165: board Shield_RTC_MCP7940N.brd from above]

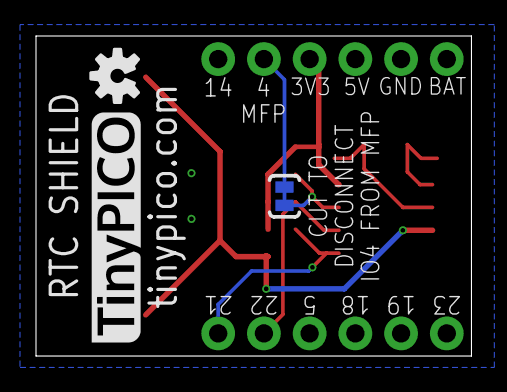
[picture p166: board Shield_RTC_MCP7940N.brd from below]

Board: 2 copper layers, 24.2 x 17.8 mm, 14 parts (2 on the bottom side), 9 nets.
