Scaniox/Glassphones/V2/code/M0 firmware/Main V2/include/main.h

/*******************************************************************************
 *         File: Glassphones/code/M0 firmware/Main V2/include/main.h
 *       Author: Alexander Mills (Scaniox#7130)
 *      License: 
 *         Date: 05/11/22
 *  Description: top level includes
 ******************************************************************************/
/* headers */
#include <Arduino.h>

#include "sys.h"
#include "menu_sys.h"
#include "serial_io.h"

#include "IS2020.h"
#include "vs1053.h"
#include "pwr_led.h"
#include "rgb.h"
#include "slider.h"

/* macros */


/* type declarations */

/* function declarations */

void setup();
void loop();
