Scaniox/Glassphones/V2/code/--IS2083 Turnkey_1.3.0--/AT1.0.1/Software/Source Code/PIC32 MCU/firmware/src/app.c

/*******************************************************************************
  MPLAB Harmony Application Source File
  
  Company:
    Microchip Technology Inc.
  
  File Name:
    app.c

  Summary:
    This file contains the source code for the MPLAB Harmony application.

  Description:
    This file contains the source code for the MPLAB Harmony application.  It 
    implements the logic of the application's state machine and it may call 
    API routines of other MPLAB Harmony modules in the system, such as drivers,
    system services, and middleware.  However, it does not call any of the
    system interfaces (such as the "Initialize" and "Tasks" functions) of any of
    the modules in the system or make any assumptions about when those functions
    are called.  That is the responsibility of the configuration-specific system
    files.
 *******************************************************************************/

// DOM-IGNORE-BEGIN
/*******************************************************************************
Copyright (c) 2013-2014 released Microchip Technology Inc.  All rights reserved.

Microchip licenses to you the right to use, modify, copy and distribute
Software only when embedded on a Microchip microcontroller or digital signal
controller that is integrated into your product or third party product
(pursuant to the sublicense terms in the accompanying license agreement).

You should refer to the license agreement accompanying this Software for
additional information regarding your rights and obligations.

SOFTWARE AND DOCUMENTATION ARE PROVIDED "AS IS" WITHOUT WARRANTY OF ANY KIND,
EITHER EXPRESS OR IMPLIED, INCLUDING WITHOUT LIMITATION, ANY WARRANTY OF
MERCHANTABILITY, TITLE, NON-INFRINGEMENT AND FITNESS FOR A PARTICULAR PURPOSE.
IN NO EVENT SHALL MICROCHIP OR ITS LICENSORS BE LIABLE OR OBLIGATED UNDER
CONTRACT, NEGLIGENCE, STRICT LIABILITY, CONTRIBUTION, BREACH OF WARRANTY, OR
OTHER LEGAL EQUITABLE THEORY ANY DIRECT OR INDIRECT DAMAGES OR EXPENSES
INCLUDING BUT NOT LIMITED TO ANY INCIDENTAL, SPECIAL, INDIRECT, PUNITIVE OR
CONSEQUENTIAL DAMAGES, LOST PROFITS OR LOST DATA, COST OF PROCUREMENT OF
SUBSTITUTE GOODS, TECHNOLOGY, SERVICES, OR ANY CLAIMS BY THIRD PARTIES
(INCLUDING BUT NOT LIMITED TO ANY DEFENSE THEREOF), OR OTHER SIMILAR COSTS.
 *******************************************************************************/
// DOM-IGNORE-END


// *****************************************************************************
// *****************************************************************************
// Section: Included Files 
// *****************************************************************************
// *****************************************************************************
#include "app.h"
#include "bt_hardware_profile.h"
#include "led.h"
#include "key.h"
#include "bt_app.h"
#include "bt_line_in.h"
#include "sta369bwdsp_handler.h"
#include "bt_hardware_profile.h"

// *****************************************************************************
// *****************************************************************************
// Section: Global Data Definitions
// *****************************************************************************
// *****************************************************************************

// *****************************************************************************
/* Application Data

  Summary:
    Holds application data

  Description:
    This structure holds the application's data.

  Remarks:
    This structure should be initialized by the APP_Initialize function.
    
    Application strings and buffers are be defined outside this structure.
*/

APP_DATA appData;
DRV_HANDLE I2C_Handle;
DRV_HANDLE UART_Handle;

// *****************************************************************************
// *****************************************************************************
// Section: Application Callback Functions
// *****************************************************************************
// *****************************************************************************

/* TODO:  Add any necessary callback functions.
*/

// *****************************************************************************
// *****************************************************************************
// Section: Application Local Functions
// *****************************************************************************
// *****************************************************************************


/* TODO:  Add any necessary local functions.
*/


// *****************************************************************************
// *****************************************************************************
// Section: Application Initialization and State Machine Functions
// *****************************************************************************
// *****************************************************************************

/*******************************************************************************
  Function:
    void APP_Initialize ( void )

  Remarks:
    See prototype in app.h.
 */

void APP_Initialize ( void )
{
    /* Place the App state machine in its initial state. */
    appData.state = APP_STATE_INIT;

    
    /* TODO: Initialize your application's state machine and other
     * parameters.
     */    
    BM6X_MFB_SetLow();
    BM6X_RESET_SetLow();
    bt_disableUartTransferIntr();
    DRV_TMR0_Start();                   //start 1ms timer, added for application
    DRV_TMR1_Start();
    I2C_Handle = DRV_I2C_Open( DRV_I2C_INDEX_0, 0 );
    UART_Handle = DRV_USART_Open(DRV_USART_INDEX_0, 0);
    ENABLE_DSP_POWER();     //enable DSP power
    LED_init();
    KEY_Initialize();
    sta369bwdsp_init();
    BTAPP_Init();
    AnalogAudioDetectInit();
    Set_LED_Style(LED_0, LED_OFF, 500, 500);
    Set_LED_Style(LED_1, LED_OFF, 500, 500);
    Set_LED_Style(LED_2, LED_OFF, 500, 500);
    Set_LED_Style(LED_3, LED_OFF, 500, 500);
    Set_LED_Style(LED_4, LED_NOT_CTRL, 500, 500);
    Set_LED_Style(LED_5, LED_NOT_CTRL, 500, 500);
    Set_LED_Style(LED_6, LED_NOT_CTRL, 500, 500);
    Set_LED_Style(LED_7, LED_NOT_CTRL, 500, 500);
#ifdef _LIGHTING_CTRL 
    LightingCtrl_Init();
#endif
}


/******************************************************************************
  Function:
    void APP_Tasks ( void )

  Remarks:
    See prototype in app.h.
 */

void APP_Tasks ( void )
{
    sta369bwdsp_task();
    BTAPP_Task();
    KEY_Task();
    AnalogAudioDetectTask();
     _wait ();
}

 

/*******************************************************************************
 End of File
 */
