Scaniox/Glassphones/V2/code/M0 firmware/Main V2/include/slider.h

/*******************************************************************************
 *         File: Glassphones\V2\code\M0 firmware\Main V2\include\slider.h
 *       Author: Alexander Mills (Scaniox#7130)
 *      License:
 *         Date: 06/11/22
 *  Description: mpr121 1d capacitive touch slider HAL header
 ******************************************************************************/


/* headers */
#include "module_common.h"
#include "Adafruit_MPR121.h"

/* types */
class Slider{
    int n_element;
    int p_irq;

    Mod_State state = Mod_State::UNINITIALISED;
    Adafruit_MPR121 cap = Adafruit_MPR121();
    int samples = 4;
    uint16_t cal_values[N_SLIDER_ELEMENTS];

    public:
        Slider(int n_element, int p_irq);
        void setup();
        void loop();
        Mod_State get_state();
        Act_rply calibrate(uint8_t cal_samples);
        uint16_t read_sensor(uint8_t sensor_no);
        void dump_raw();
        void dump_cal();
        int get_touch_points(uint8_t *points);
};
