Scaniox/Glassphones/V2/code/M0 firmware/Main V2/src/menu_sys.cpp

/*******************************************************************************
 *         File: V2\code\M0 firmware\Main V2\src\menu_sys.cpp
 *       Author: Alexander Mills (Scaniox#7130)
 *      License: 
 *         Date: 12/02/23
 *  Description: 
 ******************************************************************************/
/* headers */
#include "menu_sys.h"

/* member function definitions */
Menu_sys::Menu_sys() {}
void Menu_sys::setup() {}
void Menu_sys::loop() {}
