Scaniox/Glassphones/V2/code/M0 firmware/Main V2/src/slider.cpp

/*******************************************************************************
 *         File: V2\code\M0 firmware\Main V2\src\slider.cpp
 *       Author: Alexander Mills (Scaniox#7130)
 *      License: 
 *         Date: 12/02/23
 *  Description: 
 ******************************************************************************/
/* headers */
#include "slider.h"

/* member function definitions */
Slider::Slider(int n_element, int p_irq) :
    n_element(n_element),
    p_irq(p_irq) {}
    
void Slider::setup() {};
void Slider::loop() {};
