Scaniox/Glassphones/V2/code/M0 firmware/Main V2/src/sys.cpp

/*******************************************************************************
 *         File: V2\code\M0 firmware\Main V2\src\sys.cpp
 *       Author: Alexander Mills (Scaniox#7130)
 *      License: 
 *         Date: 12/02/23
 *  Description: 
 ******************************************************************************/
/* headers */
#include "sys.h"

/* member function definitions */
Sys::Sys() {};
void Sys::setup() {};
void Sys::loop() {};
