Scaniox/Glassphones/V2/code/M0 firmware/Main V2/src/vs1053.cpp

/*******************************************************************************
 *         File: V2\code\M0 firmware\Main V2\src\vs1053.cpp
 *       Author: Alexander Mills (Scaniox#7130)
 *      License: 
 *         Date: 12/02/23
 *  Description: 
 ******************************************************************************/
/* headers */
#include "vs1053.h"

/* member function definitions */
VS1053::VS1053() {};
void VS1053::setup() {};
void VS1053::loop() {};
