Scaniox/Glassphones/V1 - esp32/code/GlassPhones/main/globals.h

//// header file for variables shared across all files


// needed headers
#include <stdio.h>
#include <string.h>
#include <stdlib.h>
#include "freertos/FreeRTOS.h"
#include "freertos/task.h"
#include "freertos/queue.h"
#include "nvs_flash.h"
#include "esp_system.h"

#include "driver/gpio.h"
#include "driver/uart.h"

#include "esp_log.h"
#include "esp_err.h"

//bluetooth
#include "esp_bt.h"
#include "esp_bt_main.h"
#include "esp_bt_device.h"
#include "esp_gap_bt_api.h"
#include "esp_a2dp_api.h"
#include "esp_avrc_api.h"
#include "BT_event_handlers.h"
    uint8_t sender_bt_address;

//max9850e
#include "driver/i2c.h"
#include "driver/i2s.h"
#include "driver/ledc.h"
#include "maxim9850e.h"

//SD card
#include "driver/sdmmc_host.h"
#include "sdmmc_cmd.h"
#include "esp_vfs_fat.h"
#include "diskio_sdmmc.h"
#include "SD_card.h"

// serial communication
#include "serial.h"

//adf bluetooth
#include "bluetooth_service.h"
