Scaniox/Glassphones/V2/code/--IS2083 Turnkey_1.3.0--/AT1.0.1/Software/Source Code/PIC32 MCU/firmware/src/system_config/MX450_BASIC_DEMO0/system_config.h

/*******************************************************************************
  MPLAB Harmony System Configuration Header

  File Name:
    system_config.h

  Summary:
    Build-time configuration header for the system defined by this MPLAB Harmony
    project.

  Description:
    An MPLAB Project may have multiple configurations.  This file defines the
    build-time options for a single configuration.

  Remarks:
    This configuration header must not define any prototypes or data
    definitions (or include any files that do).  It only provides macro
    definitions for build-time configuration options that are not instantiated
    until used by another MPLAB Harmony module or application.

    Created with MPLAB Harmony Version 1.09
*******************************************************************************/

// DOM-IGNORE-BEGIN
/*******************************************************************************
Copyright (c) 2013-2015 released Microchip Technology Inc.  All rights reserved.

Microchip licenses to you the right to use, modify, copy and distribute
Software only when embedded on a Microchip microcontroller or digital signal
controller that is integrated into your product or third party product
(pursuant to the sublicense terms in the accompanying license agreement).

You should refer to the license agreement accompanying this Software for
additional information regarding your rights and obligations.

SOFTWARE AND DOCUMENTATION ARE PROVIDED AS IS WITHOUT WARRANTY OF ANY KIND,
EITHER EXPRESS OR IMPLIED, INCLUDING WITHOUT LIMITATION, ANY WARRANTY OF
MERCHANTABILITY, TITLE, NON-INFRINGEMENT AND FITNESS FOR A PARTICULAR PURPOSE.
IN NO EVENT SHALL MICROCHIP OR ITS LICENSORS BE LIABLE OR OBLIGATED UNDER
CONTRACT, NEGLIGENCE, STRICT LIABILITY, CONTRIBUTION, BREACH OF WARRANTY, OR
OTHER LEGAL EQUITABLE THEORY ANY DIRECT OR INDIRECT DAMAGES OR EXPENSES
INCLUDING BUT NOT LIMITED TO ANY INCIDENTAL, SPECIAL, INDIRECT, PUNITIVE OR
CONSEQUENTIAL DAMAGES, LOST PROFITS OR LOST DATA, COST OF PROCUREMENT OF
SUBSTITUTE GOODS, TECHNOLOGY, SERVICES, OR ANY CLAIMS BY THIRD PARTIES
(INCLUDING BUT NOT LIMITED TO ANY DEFENSE THEREOF), OR OTHER SIMILAR COSTS.
*******************************************************************************/
// DOM-IGNORE-END

#ifndef _SYSTEM_CONFIG_H
#define _SYSTEM_CONFIG_H

// *****************************************************************************
// *****************************************************************************
// Section: Included Files
// *****************************************************************************
// *****************************************************************************
/*  This section Includes other configuration headers necessary to completely
    define this configuration.
*/

// DOM-IGNORE-BEGIN
#ifdef __cplusplus  // Provide C++ Compatibility

extern "C" {

#endif
// DOM-IGNORE-END

// *****************************************************************************
// *****************************************************************************
// Section: System Service Configuration
// *****************************************************************************
// *****************************************************************************
// *****************************************************************************
/* Common System Service Configuration Options
*/
#define SYS_VERSION_STR           "1.09"
#define SYS_VERSION               10900

// *****************************************************************************
/* Clock System Service Configuration Options
*/
#define SYS_CLK_FREQ                        20000000ul
#define SYS_CLK_BUS_PERIPHERAL_1            20000000ul
#define SYS_CLK_UPLL_BEFORE_DIV2_FREQ       96000000ul
#define SYS_CLK_CONFIG_PRIMARY_XTAL         16000000ul
#define SYS_CLK_CONFIG_SECONDARY_XTAL       0ul
   
/*** Interrupt System Service Configuration ***/
#define SYS_INT                     true

/*** Ports System Service Configuration ***/

#define SYS_PORT_A_ANSEL        0x0
#define SYS_PORT_A_TRIS         0xc68f
#define SYS_PORT_A_LAT          0x0
#define SYS_PORT_A_ODC          0x0
#define SYS_PORT_A_CNPU         0x600
#define SYS_PORT_A_CNPD         0x0
#define SYS_PORT_A_CNEN         0x0

#define SYS_PORT_B_ANSEL        0x0
#define SYS_PORT_B_TRIS         0xfff
#define SYS_PORT_B_LAT          0xf000
#define SYS_PORT_B_ODC          0x0
#define SYS_PORT_B_CNPU         0xf8d
#define SYS_PORT_B_CNPD         0x0
#define SYS_PORT_B_CNEN         0x0

#define SYS_PORT_C_ANSEL        0x0
#define SYS_PORT_C_TRIS         0xf01e
#define SYS_PORT_C_LAT          0x0
#define SYS_PORT_C_ODC          0x0
#define SYS_PORT_C_CNPU         0x0
#define SYS_PORT_C_CNPD         0x0
#define SYS_PORT_C_CNEN         0x0

#define SYS_PORT_D_ANSEL        0x0
#define SYS_PORT_D_TRIS         0x3fff
#define SYS_PORT_D_LAT          0xc000
#define SYS_PORT_D_ODC          0x0
#define SYS_PORT_D_CNPU         0x0
#define SYS_PORT_D_CNPD         0x0
#define SYS_PORT_D_CNEN         0x0

#define SYS_PORT_E_ANSEL        0x0
#define SYS_PORT_E_TRIS         0x3ff
#define SYS_PORT_E_LAT          0x0
#define SYS_PORT_E_ODC          0x0
#define SYS_PORT_E_CNPU         0x0
#define SYS_PORT_E_CNPD         0x0
#define SYS_PORT_E_CNEN         0x0

#define SYS_PORT_F_ANSEL        0x0
#define SYS_PORT_F_TRIS         0x137
#define SYS_PORT_F_LAT          0x3000
#define SYS_PORT_F_ODC          0x0
#define SYS_PORT_F_CNPU         0x0
#define SYS_PORT_F_CNPD         0x0
#define SYS_PORT_F_CNEN         0x0

#define SYS_PORT_G_ANSEL        0x0
#define SYS_PORT_G_TRIS         0xf3c2
#define SYS_PORT_G_LAT          0x0
#define SYS_PORT_G_ODC          0x0
#define SYS_PORT_G_CNPU         0x0
#define SYS_PORT_G_CNPD         0x0
#define SYS_PORT_G_CNEN         0x0


// *****************************************************************************
// *****************************************************************************
// Section: Driver Configuration
// *****************************************************************************
// *****************************************************************************
/*** Timer Driver Configuration ***/
#define DRV_TMR_INTERRUPT_MODE             true

/*** Timer Driver 0 Configuration ***/
#define DRV_TMR_PERIPHERAL_ID_IDX0          TMR_ID_1
#define DRV_TMR_INTERRUPT_SOURCE_IDX0       INT_SOURCE_TIMER_1
#define DRV_TMR_INTERRUPT_VECTOR_IDX0       INT_VECTOR_T1
#define DRV_TMR_ISR_VECTOR_IDX0             _TIMER_1_VECTOR
#define DRV_TMR_INTERRUPT_PRIORITY_IDX0     INT_PRIORITY_LEVEL2
#define DRV_TMR_INTERRUPT_SUB_PRIORITY_IDX0 INT_SUBPRIORITY_LEVEL0
#define DRV_TMR_CLOCK_SOURCE_IDX0           DRV_TMR_CLKSOURCE_INTERNAL
#define DRV_TMR_PRESCALE_IDX0               TMR_PRESCALE_VALUE_8
#define DRV_TMR_OPERATION_MODE_IDX0         DRV_TMR_OPERATION_MODE_16_BIT
#define DRV_TMR_ASYNC_WRITE_ENABLE_IDX0     false
#define DRV_TMR_POWER_STATE_IDX0            

/*** Timer Driver 1 Configuration ***/
#define DRV_TMR_PERIPHERAL_ID_IDX1          TMR_ID_2
#define DRV_TMR_INTERRUPT_SOURCE_IDX1       INT_SOURCE_TIMER_2
#define DRV_TMR_INTERRUPT_VECTOR_IDX1       INT_VECTOR_T2
#define DRV_TMR_ISR_VECTOR_IDX1             _TIMER_2_VECTOR
#define DRV_TMR_INTERRUPT_PRIORITY_IDX1     INT_PRIORITY_LEVEL3
#define DRV_TMR_INTERRUPT_SUB_PRIORITY_IDX1 INT_SUBPRIORITY_LEVEL0
#define DRV_TMR_CLOCK_SOURCE_IDX1           DRV_TMR_CLKSOURCE_INTERNAL
#define DRV_TMR_PRESCALE_IDX1               TMR_PRESCALE_VALUE_2
#define DRV_TMR_OPERATION_MODE_IDX1         DRV_TMR_OPERATION_MODE_16_BIT
#define DRV_TMR_ASYNC_WRITE_ENABLE_IDX1     false
#define DRV_TMR_POWER_STATE_IDX1            

 // *****************************************************************************
/* USART Driver Configuration Options
*/
#define DRV_USART_INSTANCES_NUMBER                  1
#define DRV_USART_CLIENTS_NUMBER                    1
#define DRV_USART_INTERRUPT_MODE                    true
#define DRV_USART_BYTE_MODEL_SUPPORT                true
#define DRV_USART_READ_WRITE_MODEL_SUPPORT          false
#define DRV_USART_BUFFER_QUEUE_SUPPORT              false
#define DRV_USART_SUPPORT_TRANSMIT_DMA              false
#define DRV_USART_SUPPORT_RECEIVE_DMA               false
#define DRV_I2C_INTERRUPT_MODE                    		true


// *****************************************************************************
// *****************************************************************************
// Section: Middleware & Other Library Configuration
// *****************************************************************************
// *****************************************************************************




// *****************************************************************************
// *****************************************************************************
// Section: Application Configuration
// *****************************************************************************
// *****************************************************************************

/*** Application Instance 0 Configuration ***/

//DOM-IGNORE-BEGIN
#ifdef __cplusplus
}
#endif
//DOM-IGNORE-END


#endif // _SYSTEM_CONFIG_H
/*******************************************************************************
 End of File
*/
