Scaniox/Glassphones/V2/code/--IS2083 Turnkey_1.3.0--/AT1.0.1/Tools/Config GUI Tool/hdfile/App_cfg_dsp.h

/********************************************************************
  File Information:
    FileName:       app_cfg_dsp.h
    Processor:      8051
    Hardware:
    Complier:       Keil C51
    Company:        Microchip Technology, Inc.

    Software License Agreement:

    The software supplied herewith by Microchip Technology Incorporated
    (the "Company") for 8051 Microcontroller is intended and supplied
    to you, the Company's customer, for use solely and exclusively on
    Microchip 8051 Microcontroller products. The software is owned by
    the Company and/or its supplier, and is protected under applicable
    copyright laws. All rights are reserved. Any use in violation of
    the foregoing restrictions may subject the user to criminal
    sanctions under applicable laws, as well as to civil liability for
    the breach of the terms and conditions of this license.

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
********************************************************************/

#ifndef APP_CFG_DSP_H
#define APP_CFG_DSP_H

/**
  @addtogroup APP_CFG_MODULE_AUD_DSP AUD_DSP Configuration
  @{
  @brief Definitions and prototypes for the MODULE_AUD_DSP Configuration.
 */


/**
 * @brief Configuration key definition of the module @ref CFG_MODULE_ID_AUD_DSP.
 *  
 */

//Config Key definiton of MODULE_AUD_DSP(0x0C)
typedef enum _AUD_DSP_CFG_Key_IdDefinition_T
{
    AUD_DSP_CFG_KEY_LINEIN                      = 0x01, /**<\#PARAM_NAME : AUD_DSP_CFG_KEY_LINEIN \n
                                                            \#ALIAS : AUD DSP CFG KEY LINEIN \n
                                                            \#PARAM_TYPE : Private \n
                                                            \#PARAM_DESC : Line in silence detection threshold determines silence power threshold level for line-in signal for auto power off mechanism \n
                                                                           Gain to amplify the external signal source and playback to the speaker \n
                                                                           Byte 0:VOICE_CFG_SUB_KEY_H_LINEIN_TUNNING_SILENCE_MV_THRD \n
                                                                           BYTE1:VOICE_CFG_SUB_KEY_H_LINEIN_ENCODER_DELAY_TIME(Line in Encoder delay time(o to 40 ms) \n
                                                            \#DESC_END
                                                            \#GROUP_ID : 0x0C \n
                                                            \#KEY_ID : 0x01 \n
                                                	    */
                                                	          
    AUD_DSP_CFG_KEY_MBDRC                       = 0x02, /**<\#PARAM_NAME : AUD_DSP_CFG_KEY_MBDRC \n
                                                            \#ALIAS : AUD DSP CFG KEY MBDRC \n
                                                            \#PARAM_TYPE : Private \n
                                                            \#PARAM_DESC : 
                                                                           Byte 1: \n
                                                                            MBDRC compressor_thrd_spkout :CR is a compression ratio which compresses the average sound level, \n
                                                                            exceeding “Knee TH”, of the audio signal \n
                                                                            bit[0:1]: audio_mbdrc_compressor_thrd_spkout_LowBand \n
                                                                            0: -6dBov  1: -12dBov  2: -18dBov  3: -24dBov   \n
                                                                            bit[2:3]: audio_mbdrc_compressor_thrd_spkout_MiddleBand  \n
                                                                            0: -6dBov  1: -12dBov  2: -18dBov  3: -24dBov \n
                                                                            bit[4:5]: audio_mbdrc_compressor_thrd_spkout_HighBand   \n
                                                                            0: -6dBov  1: -12dBov  2: -18dBov  3: -24dBov \n
                                                                            Bit[6:7]: virtual bass enhancement cutoff frequency selections \n
                                                                            0:100Hz  1: 150Hz  2: 200Hz   3:300Hz   \n
                                                                            
                                                                           Byte 2: \n
                                                                            MBDRC compressor_slope_spkout_LowBand  : Slope = (1/ratio) - 1; \n
                                                                            bit[0:1]: audio_mbdrc_compressor_slope_spkout_LowBand (ratio) \n
                                                                            0: 2/3  1:  1/ 2 2: 1/ 3    3:  1/4     \n
                                                                            bit[2:3]: audio_mbdrc_compressor_slope_spkout_MiddleBand  \n
                                                                            0: 2/3  1:  1/ 2 2: 1/ 3    3:  1/4    \n
                                                                            bit[4:5]: audio_mbdrc_compressor_slope_spkout_HighBand    \n
                                                                            0: 2/3  1:  1/ 2 2: 1/ 3    3:  1/4  \n
                                                                            Bit [6]: Virtual bass enhacement \n
                                                                            0: disable VB,   1: enable VB \n
                                                                            Bit [7]: natural smoothing for surround effect \n
                                                                            0: disable   1: enable natural smoothings  \n
                                                                            
                                                                           Byte 3: \n
                                                                            MBDRC compressor_Gain_spkout \n
                                                                            bit[0:3]: audio_mbdrc_compressor_Gain_spkout_LowBand(value range : 0 ~ 11) \n
                                                                            bit[4:7]: audio_mbdrc_compressor_Gain_spkout_MiddleBand (value range : 0 ~ 11) \n
                                                                           
                                                                           Byte 4: \n
                                                                            MBDRC compressor_Gain_spkout      \n
                                                                            bit[0:3]: audio_mbdrc_compressor_Gain_spkout_HighBand    \n
                                                                            value range : 0 ~ 11   \n
                                                                            MBDRC release time constants \n
                                                                            bit[4:5]:  release time for low band \n
                                                                            0:50ms  1: 100ms  2: 200ms   3:700ms     \n
                                                                            bit[6:7]:  release time for middle band \n
                                                                            0:50ms  1: 100ms  2: 200ms   3:700ms     \n
                                                                         
                                                                           Byte 5: \n
                                                                            Bit[3:0]: length of all-pass IIR filter. Length = bit[3:0] * 64 \n
                                                                            Bit[7:4]:APIIR coefficients \n
                                                                            
                                                                           Byte 6: \n
                                                                            Bit[3:0]: Main gain \n
                                                                            Bit[7:4]:Reverberation gain \n
                                                                            
                                                                           Byte 7: \n
                                                                            Bit[1:0]: attack time for low band \n
                                                                            0:10ms  1: 20ms  2: 50ms   3:100ms    \n
                                                                            Bit[3:2]: attack time for middle band \n
                                                                            0:10ms  1: 20ms  2: 50ms   3:100ms  \n
                                                                            Bit[5:4]: attack time for high band \n
                                                                            0:10ms  1: 20ms  2: 50ms   3:100ms  \n
                                                                            Bit[7:6]: Release time for high band \n
                                                                            0:50ms  1: 100ms  2: 200ms   3:700ms    \n
                                                                            
                                                                           Byte 8: \n
                                                                            This parameter controls the level of bass enhancement which is enabled along with the MB-DRC function   \n
                                                                            Range : 0x00~0xFF \n
                                                            \#DESC_END
                                                            \#GROUP_ID : 0x0C \n
                                                            \#KEY_ID : 0x02 \n
                                                	    */
                                                	          
    AUD_DSP_CFG_KEY_H_LDAC_PARAMETER            = 0x03, /**<\#PARAM_NAME : AUD_DSP_CFG_KEY_H_LDAC_PARAMETER \n
                                                            \#ALIAS : AUD DSP CFG KEY H LDAC PARAMETER \n
                                                            \#PARAM_TYPE : Private \n
                                                            \#PARAM_DESC : 
                                                                            LDAC parameters \n
                                                                            Byte 0:Reserved. \n
                                                                            Byte 1:buffer control threshold (upper)=> Usage: Media buffer upper threshold for LDAC buffer control. \n
                                                                            If number of frames in media buffer exceeds this upper threshold, LDAC buffer control will enter SKIP state. \n
                                                                            In SKIP state, frames with low energy will be dropped. 0 ~ 255. \n
                                                                            Byte 2: buffer control threshold (lower) => Usage: Media buffer lower threshold for LDAC buffer control. \n
                                                                            If number of frames in media buffer is below this lower threshold, LDAC buffer control will enter COPY state. \n
                                                                            In COPY state, frames with low energy will be duplicated. 0 ~ 255 \n
                                                                            Byte 3: Reserved. \n
                                                                            Byte 4: Reserved. \n
                                                                            Byte 5: buffer control threshold (target)=> Usage: Media buffer target threshold for LDAC buffer control. \n
                                                                            In SKIP/COPY state, If number of frames in media buffer hit this target threshold, LDAC buffer control will return to NORMAL state. \n
                                                                            In NORMAL state, LDAC buffer control do nothing. \n
                                                                            0 ~ 255 \n
                                                                            Byte 6: Reserved. \n
                                                            \#DESC_END
                                                            \#GROUP_ID : 0x0C \n
                                                            \#KEY_ID : 0x03 \n
                                                	    */
                                                	          
	AUD_DSP_CFG_KEY_CUSTOM_EQ_SPK_AUDIO		    = 0x04, /**<\#PARAM_NAME : AUD_DSP_CFG_KEY_CUSTOM_EQ_SPK_AUDIO \n
                                                            \#ALIAS : AUD DSP CFG KEY CUSTOM EQ SPK AUDIO \n
                                                            \#PARAM_TYPE : Private \n
                                                            \#PARAM_DESC : Custom EQ Spk \n
                                                            \#DESC_END
                                                            \#GROUP_ID : 0x0C \n
                                                            \#KEY_ID : 0x04 \n
                                                	    */
                                                	          
    AUD_DSP_CFG_KEY_H_CUSTOM_RX_EQ				= 0x05,  /**<\#PARAM_NAME : AUD_DSP_CFG_KEY_H_CUSTOM_RX_EQ \n
                                                             \#ALIAS : AUD DSP CFG KEY H CUSTOM RX EQ \n
                                                             \#PARAM_TYPE : Private \n
                                                             \#PARAM_DESC : RX Custom EQ, not implemented \n
                                                             \#DESC_END
                                                             \#KEY_ID : 0x05 \n
                                                    	 */
                                                	          

    AUD_DSP_CFG_KEY_END       
}AUD_DSP_CFG_Key_IdDefinition_T;



/**
 * @brief Configuration key definition of the module @ref CFG_MODULE_ID_VOICE_DSP.
 *  
 */
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
